Board-Folk/Camputers-Lynx/Lynx 96/Kicad/lynx96.kicad_sch

## KiCad design Lynx 96/Kicad/lynx96.kicad_sch (2025-07-15)

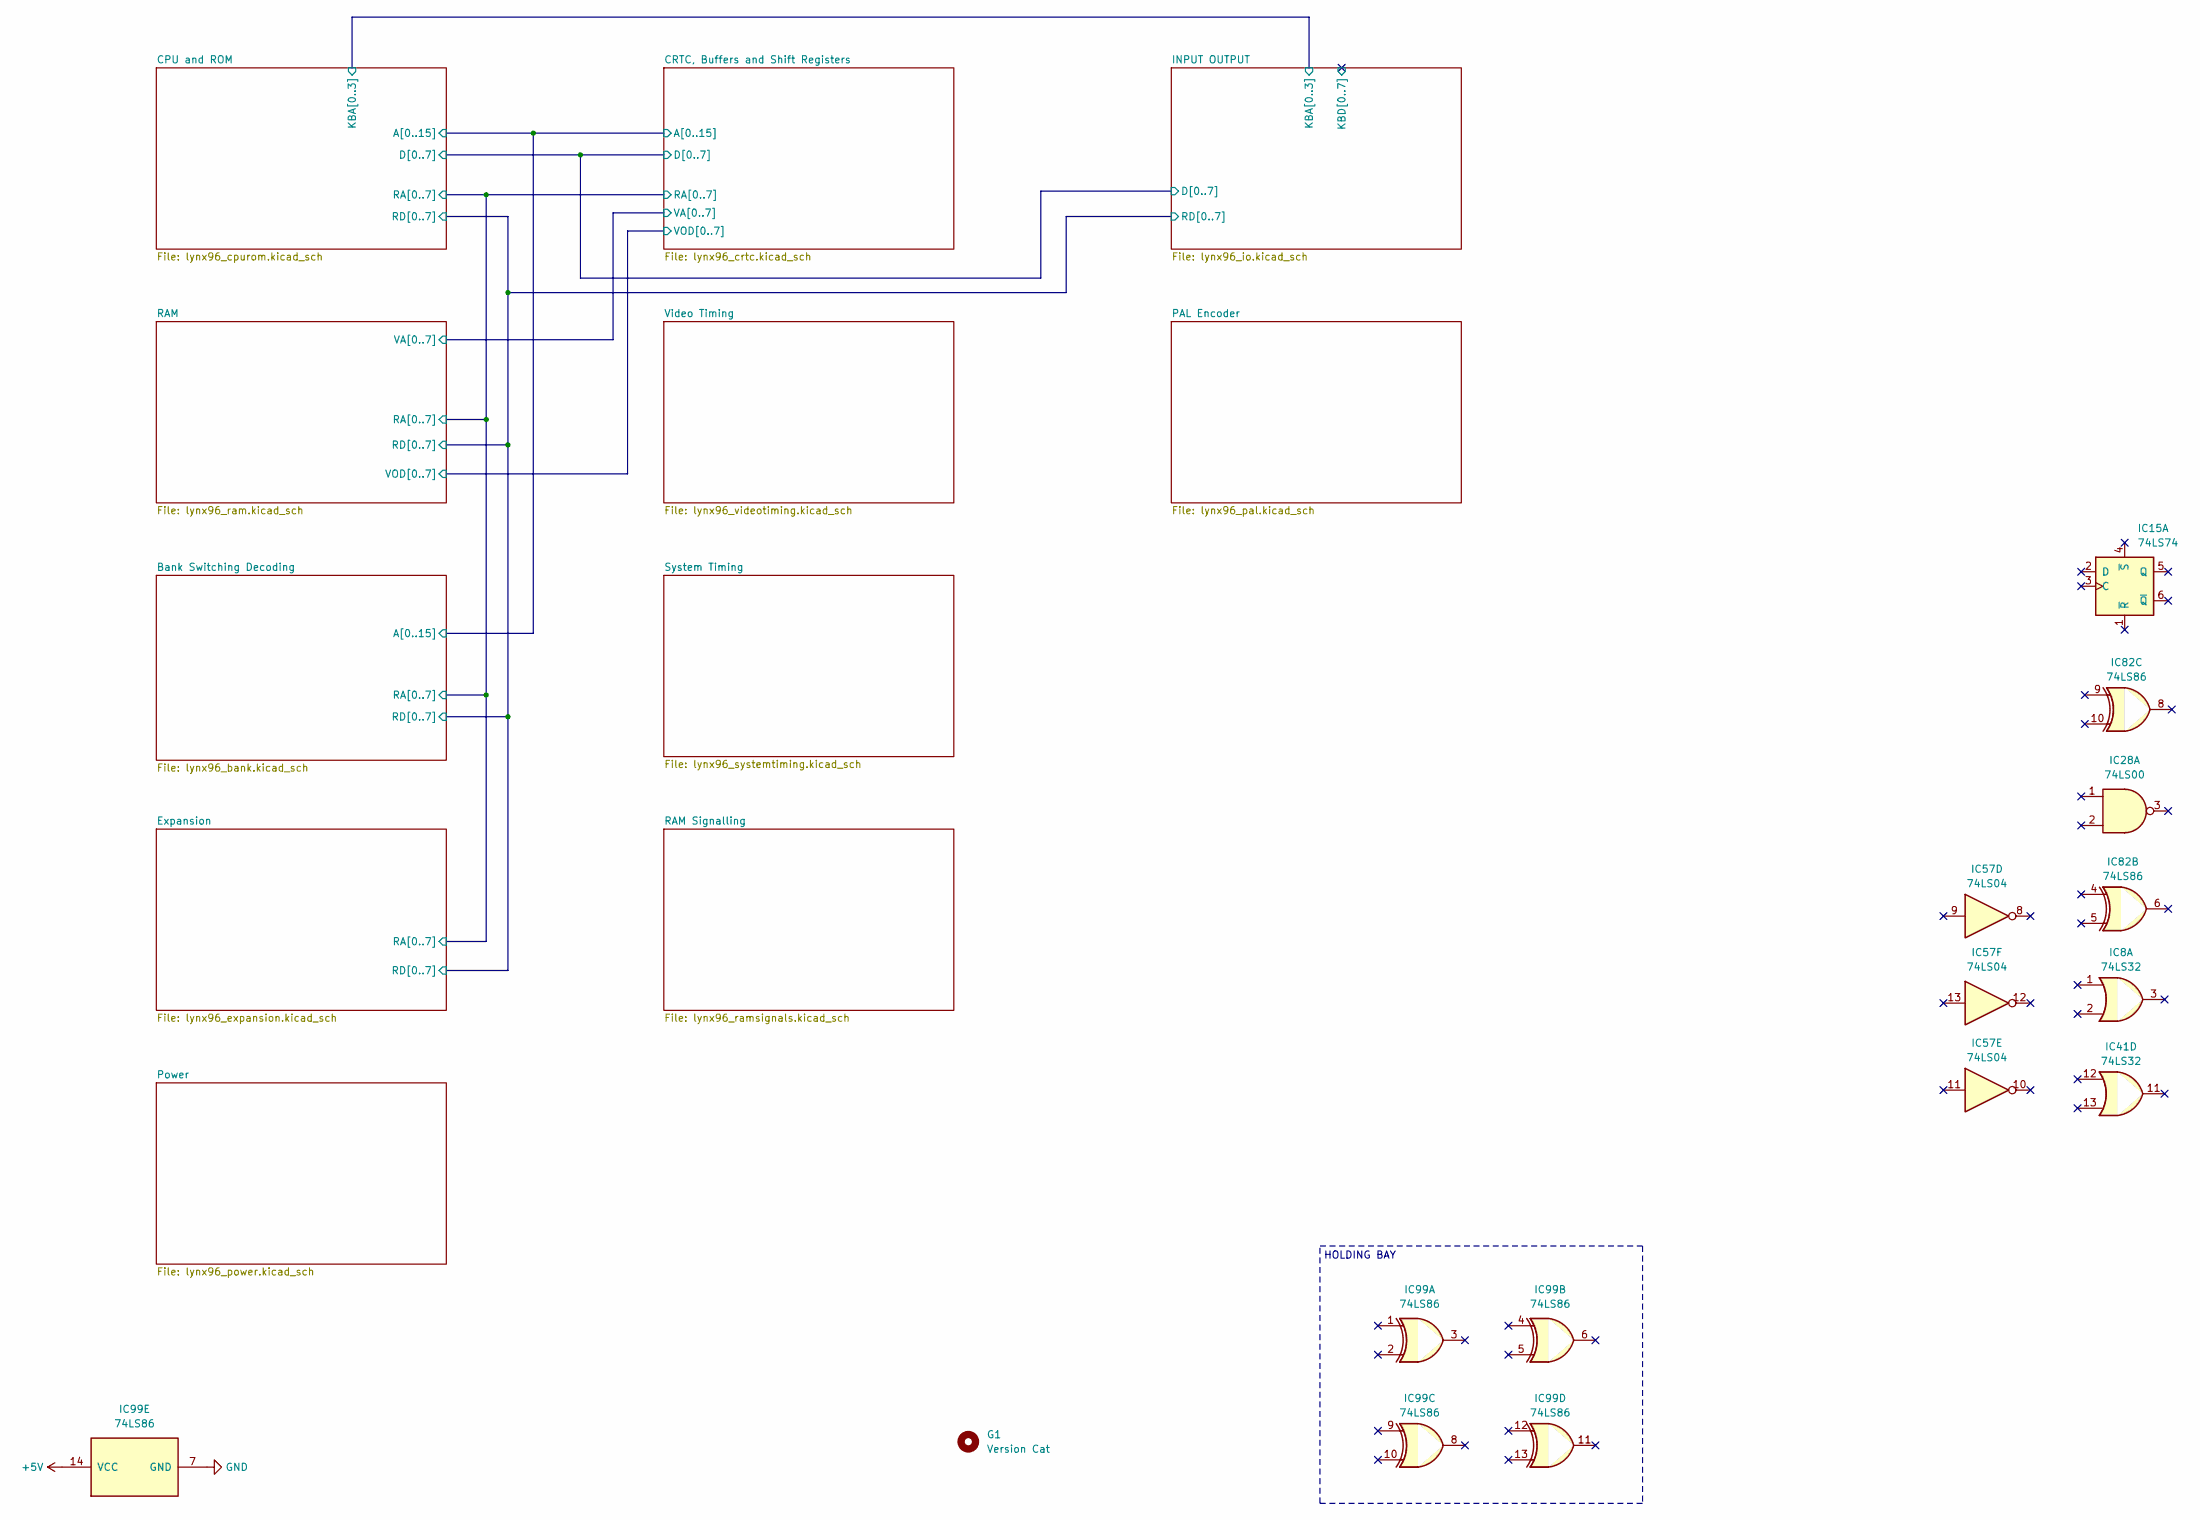
[picture p9: schematic lynx96.kicad_sch]

Parts:
G1: Version Cat; v1ncat
IC8, IC41: 74LS32; DIP-14_W7.62mm
IC15: 74LS74; DIP-14_W7.62mm
IC28: 74LS00; DIP-14_W7.62mm
IC57: 74LS04; DIP-14_W7.62mm
IC82: 74LS86; DIP-14_W7.62mm
IC99: 74LS86; FAKE

Connections:
+5V: IC99.14 (VCC)
GND: IC99.7 (GND)

Notes on the sheet:
HOLDING BAY
