Board-Folk/Camputers-Lynx/Lynx 96/Kicad/lynx96_bank.kicad_sch

## KiCad design Lynx 96/Kicad/lynx96_bank.kicad_sch (2025-07-15)

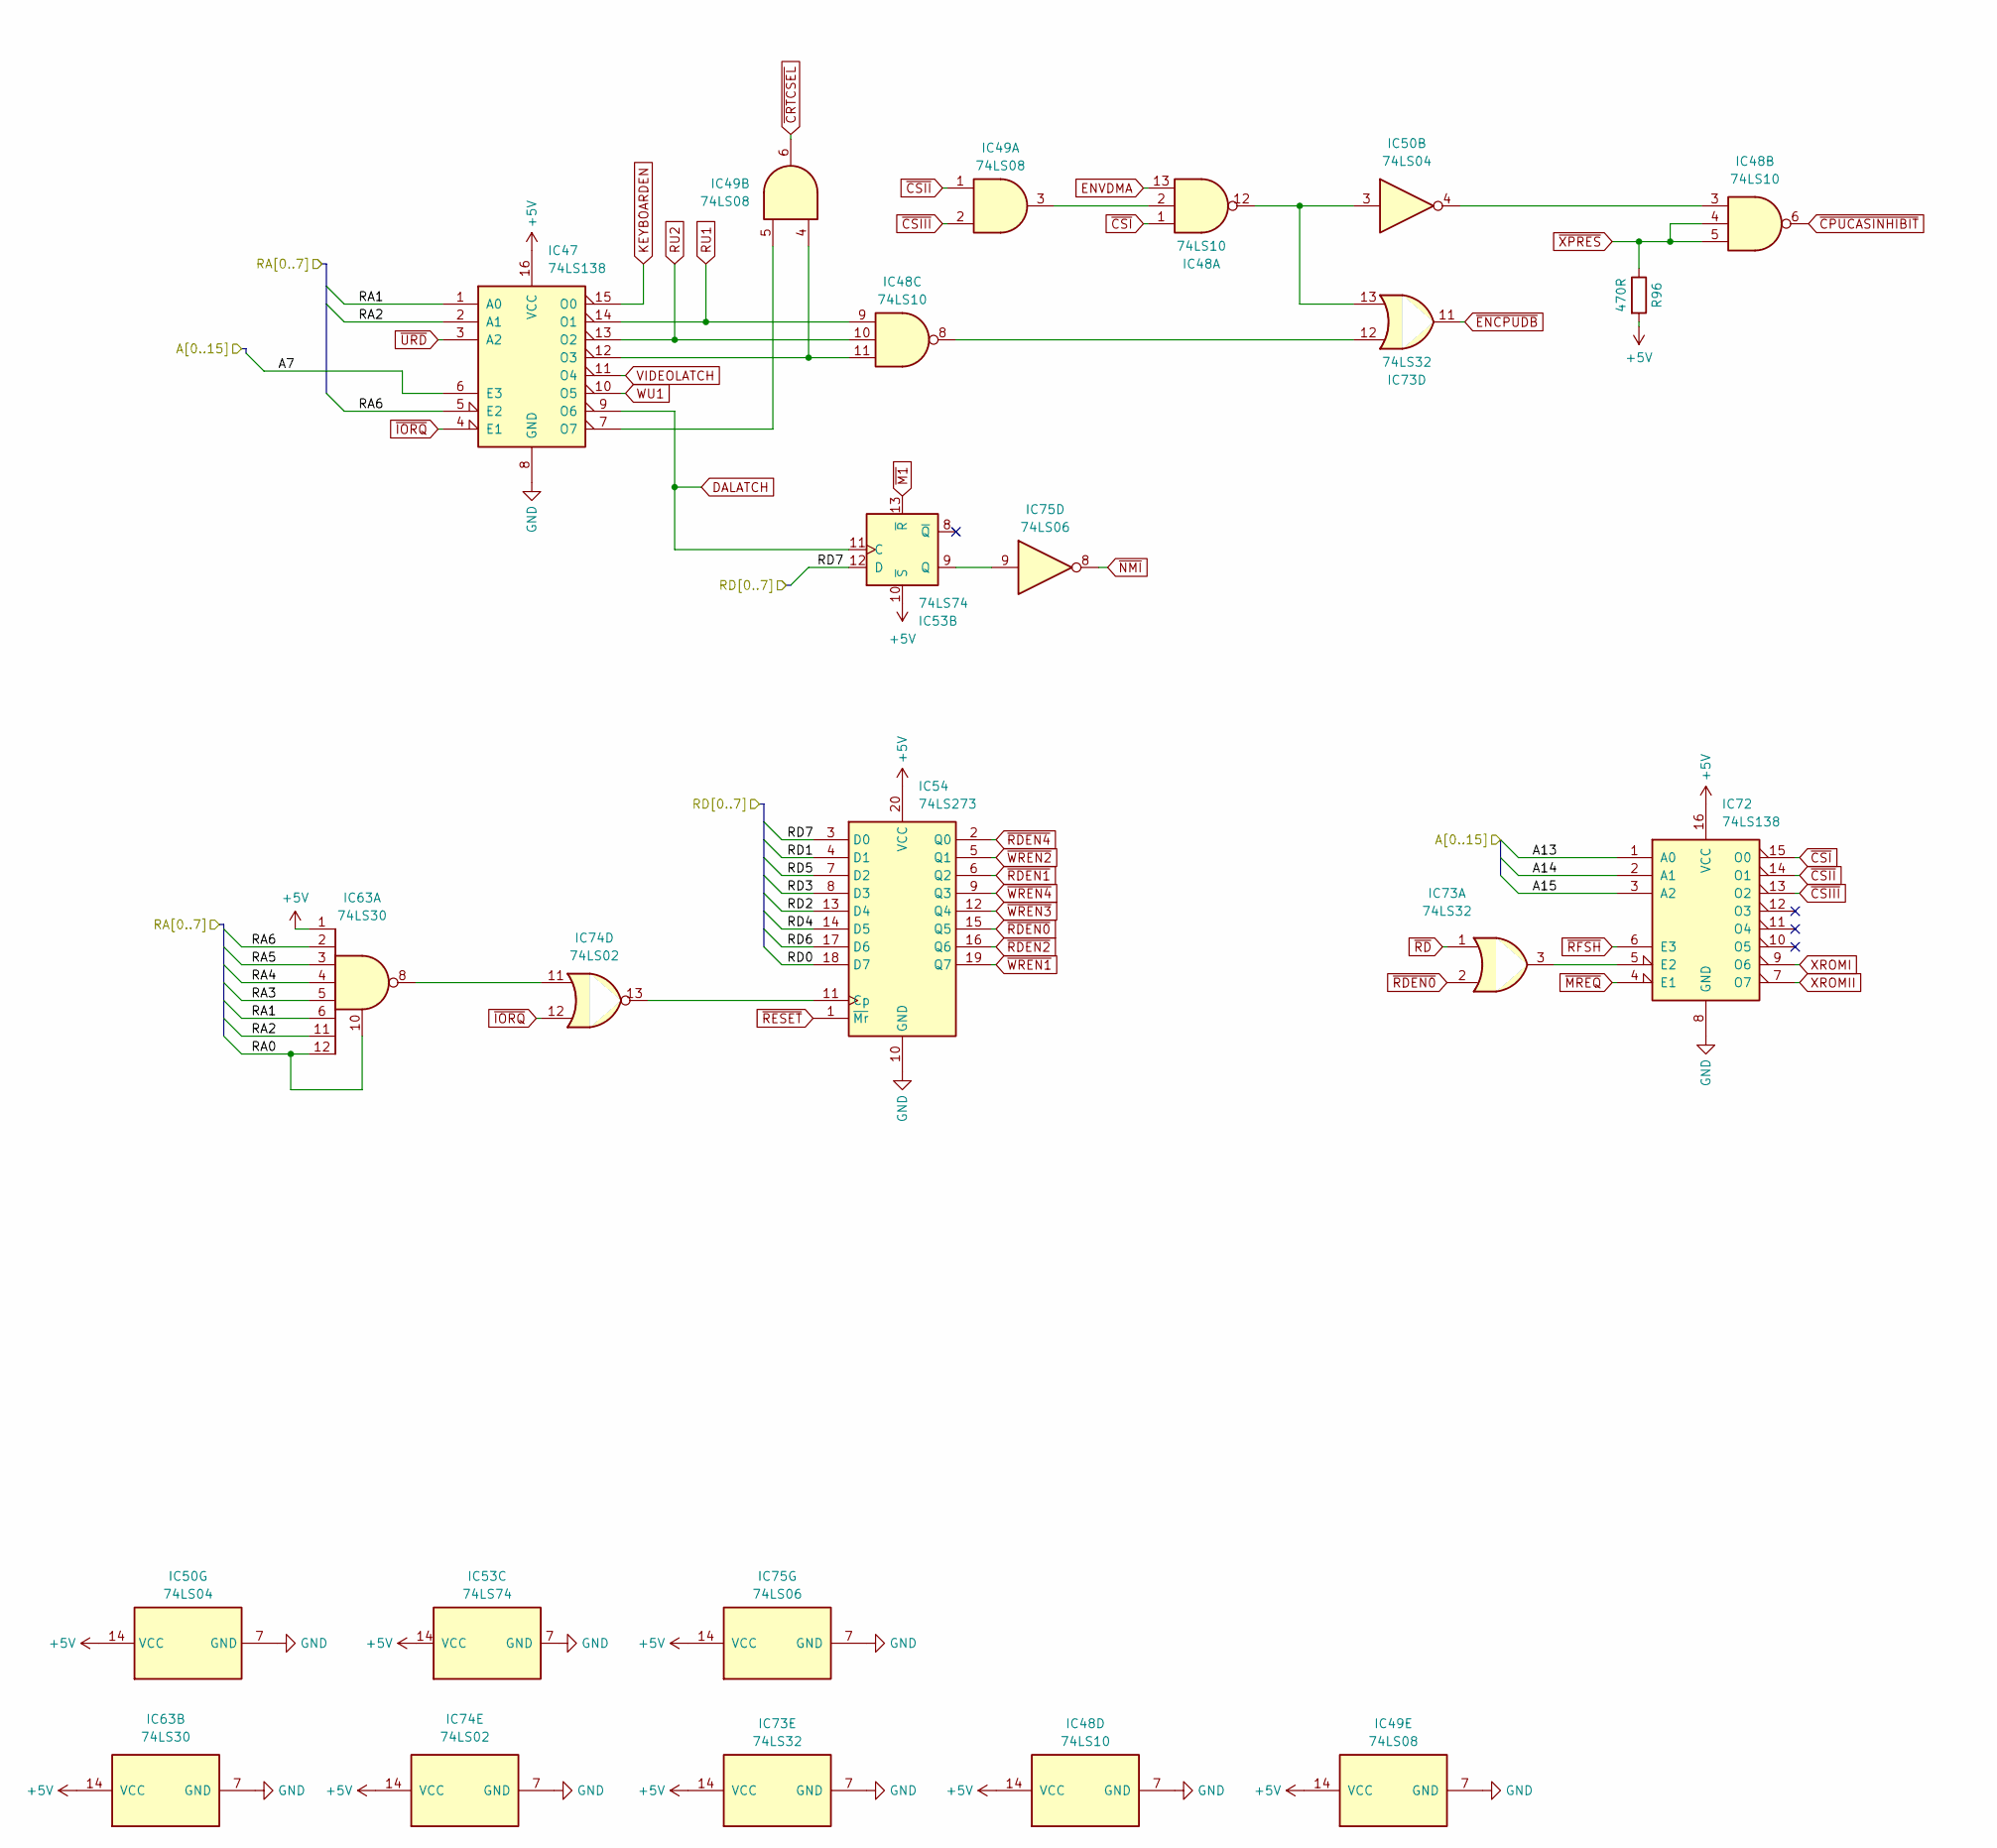
[picture p10: schematic lynx96_bank.kicad_sch]

Parts:
IC47, IC72: 74LS138; DIP-16_W7.62mm
IC48: 74LS10; DIP-14_W7.62mm
IC49: 74LS08; DIP-14_W7.62mm
IC50: 74LS04; DIP-14_W7.62mm
IC53: 74LS74; DIP-14_W7.62mm
IC54: 74LS273; DIP-20_W7.62mm
IC63: 74LS30; DIP-14_W7.62mm
IC73: 74LS32; DIP-14_W7.62mm
IC74: 74LS02; DIP-14_W7.62mm
IC75: 74LS06; DIP-14_W7.62mm
R96: 470R; Resistor 10.16mm

Connections:
+5V: IC47.16 (VCC), IC48.14 (VCC), IC49.14 (VCC), IC50.14 (VCC), IC53.10 (~S), IC53.14 (VCC), IC54.20 (VCC), IC63.1, IC63.14 (VCC), IC72.16 (VCC), IC73.14 (VCC), IC74.14 (VCC), IC75.14 (VCC), R96.2
A7: IC47.6 (E3)
A13: IC72.1 (A0)
A14: IC72.2 (A1)
A15: IC72.3 (A2)
DALATCH: IC47.9 (O6), IC53.11 (C)
ENVDMA: IC48.13
GND: IC47.8 (GND), IC48.7 (GND), IC49.7 (GND), IC50.7 (GND), IC53.7 (GND), IC54.10 (GND), IC63.7 (GND), IC72.8 (GND), IC73.7 (GND), IC74.7 (GND), IC75.7 (GND)
KEYBOARDEN: IC47.15 (O0)
unnamed: IC47.7 (O7), IC49.5
unnamed: IC47.12 (O3), IC48.11, IC49.4
unnamed: IC48.2, IC49.3
unnamed: IC48.3, IC50.4
unnamed: IC48.8, IC73.12
unnamed: IC48.12, IC50.3, IC73.13
unnamed: IC53.9 (Q), IC75.9
unnamed: IC54.11 (Cp), IC74.13
unnamed: IC63.8, IC74.11
unnamed: IC72.5 (E2), IC73.3
RA0: IC63.10, IC63.12
RA1: IC47.1 (A0), IC63.6
RA2: IC47.2 (A1), IC63.11
RA3: IC63.5
RA4: IC63.4
RA5: IC63.3
RA6: IC47.5 (E2), IC63.2
RD0: IC54.18 (D7)
RD1: IC54.4 (D1)
RD2: IC54.13 (D4)
RD3: IC54.8 (D3)
RD4: IC54.14 (D5)
RD5: IC54.7 (D2)
RD6: IC54.17 (D6)
RD7: IC53.12 (D), IC54.3 (D0)
RU1: IC47.14 (O1), IC48.9
RU2: IC47.13 (O2), IC48.10
VIDEOLATCH: IC47.11 (O4)
WU1: IC47.10 (O5)
XROMI: IC72.9 (O6)
XROMII: IC72.7 (O7)
~CPUCASINHIBIT: IC48.6
~CRTCSEL: IC49.6
~CSIII: IC49.2, IC72.13 (O2)
~CSII: IC49.1, IC72.14 (O1)
~CSI: IC48.1, IC72.15 (O0)
~ENCPUDB: IC73.11
~IORQ: IC47.4 (E1), IC74.12
~M1: IC53.13 (~R)
~MREQ: IC72.4 (E1)
~NMI: IC75.8
~RDEN0: IC54.15 (Q5), IC73.2
~RDEN1: IC54.6 (Q2)
~RDEN2: IC54.16 (Q6)
~RDEN4: IC54.2 (Q0)
~RD: IC73.1
~RESET: IC54.1 (~Mr)
~RFSH: IC72.6 (E3)
~URD: IC47.3 (A2)
~WREN1: IC54.19 (Q7)
~WREN2: IC54.5 (Q1)
~WREN3: IC54.12 (Q4)
~WREN4: IC54.9 (Q3)
~XPRES: IC48.4, IC48.5, R96.1
