Board-Folk/Camputers-Lynx/Lynx 96/Kicad/lynx96_cpurom.kicad_sch

## KiCad design Lynx 96/Kicad/lynx96_cpurom.kicad_sch (2025-07-15)

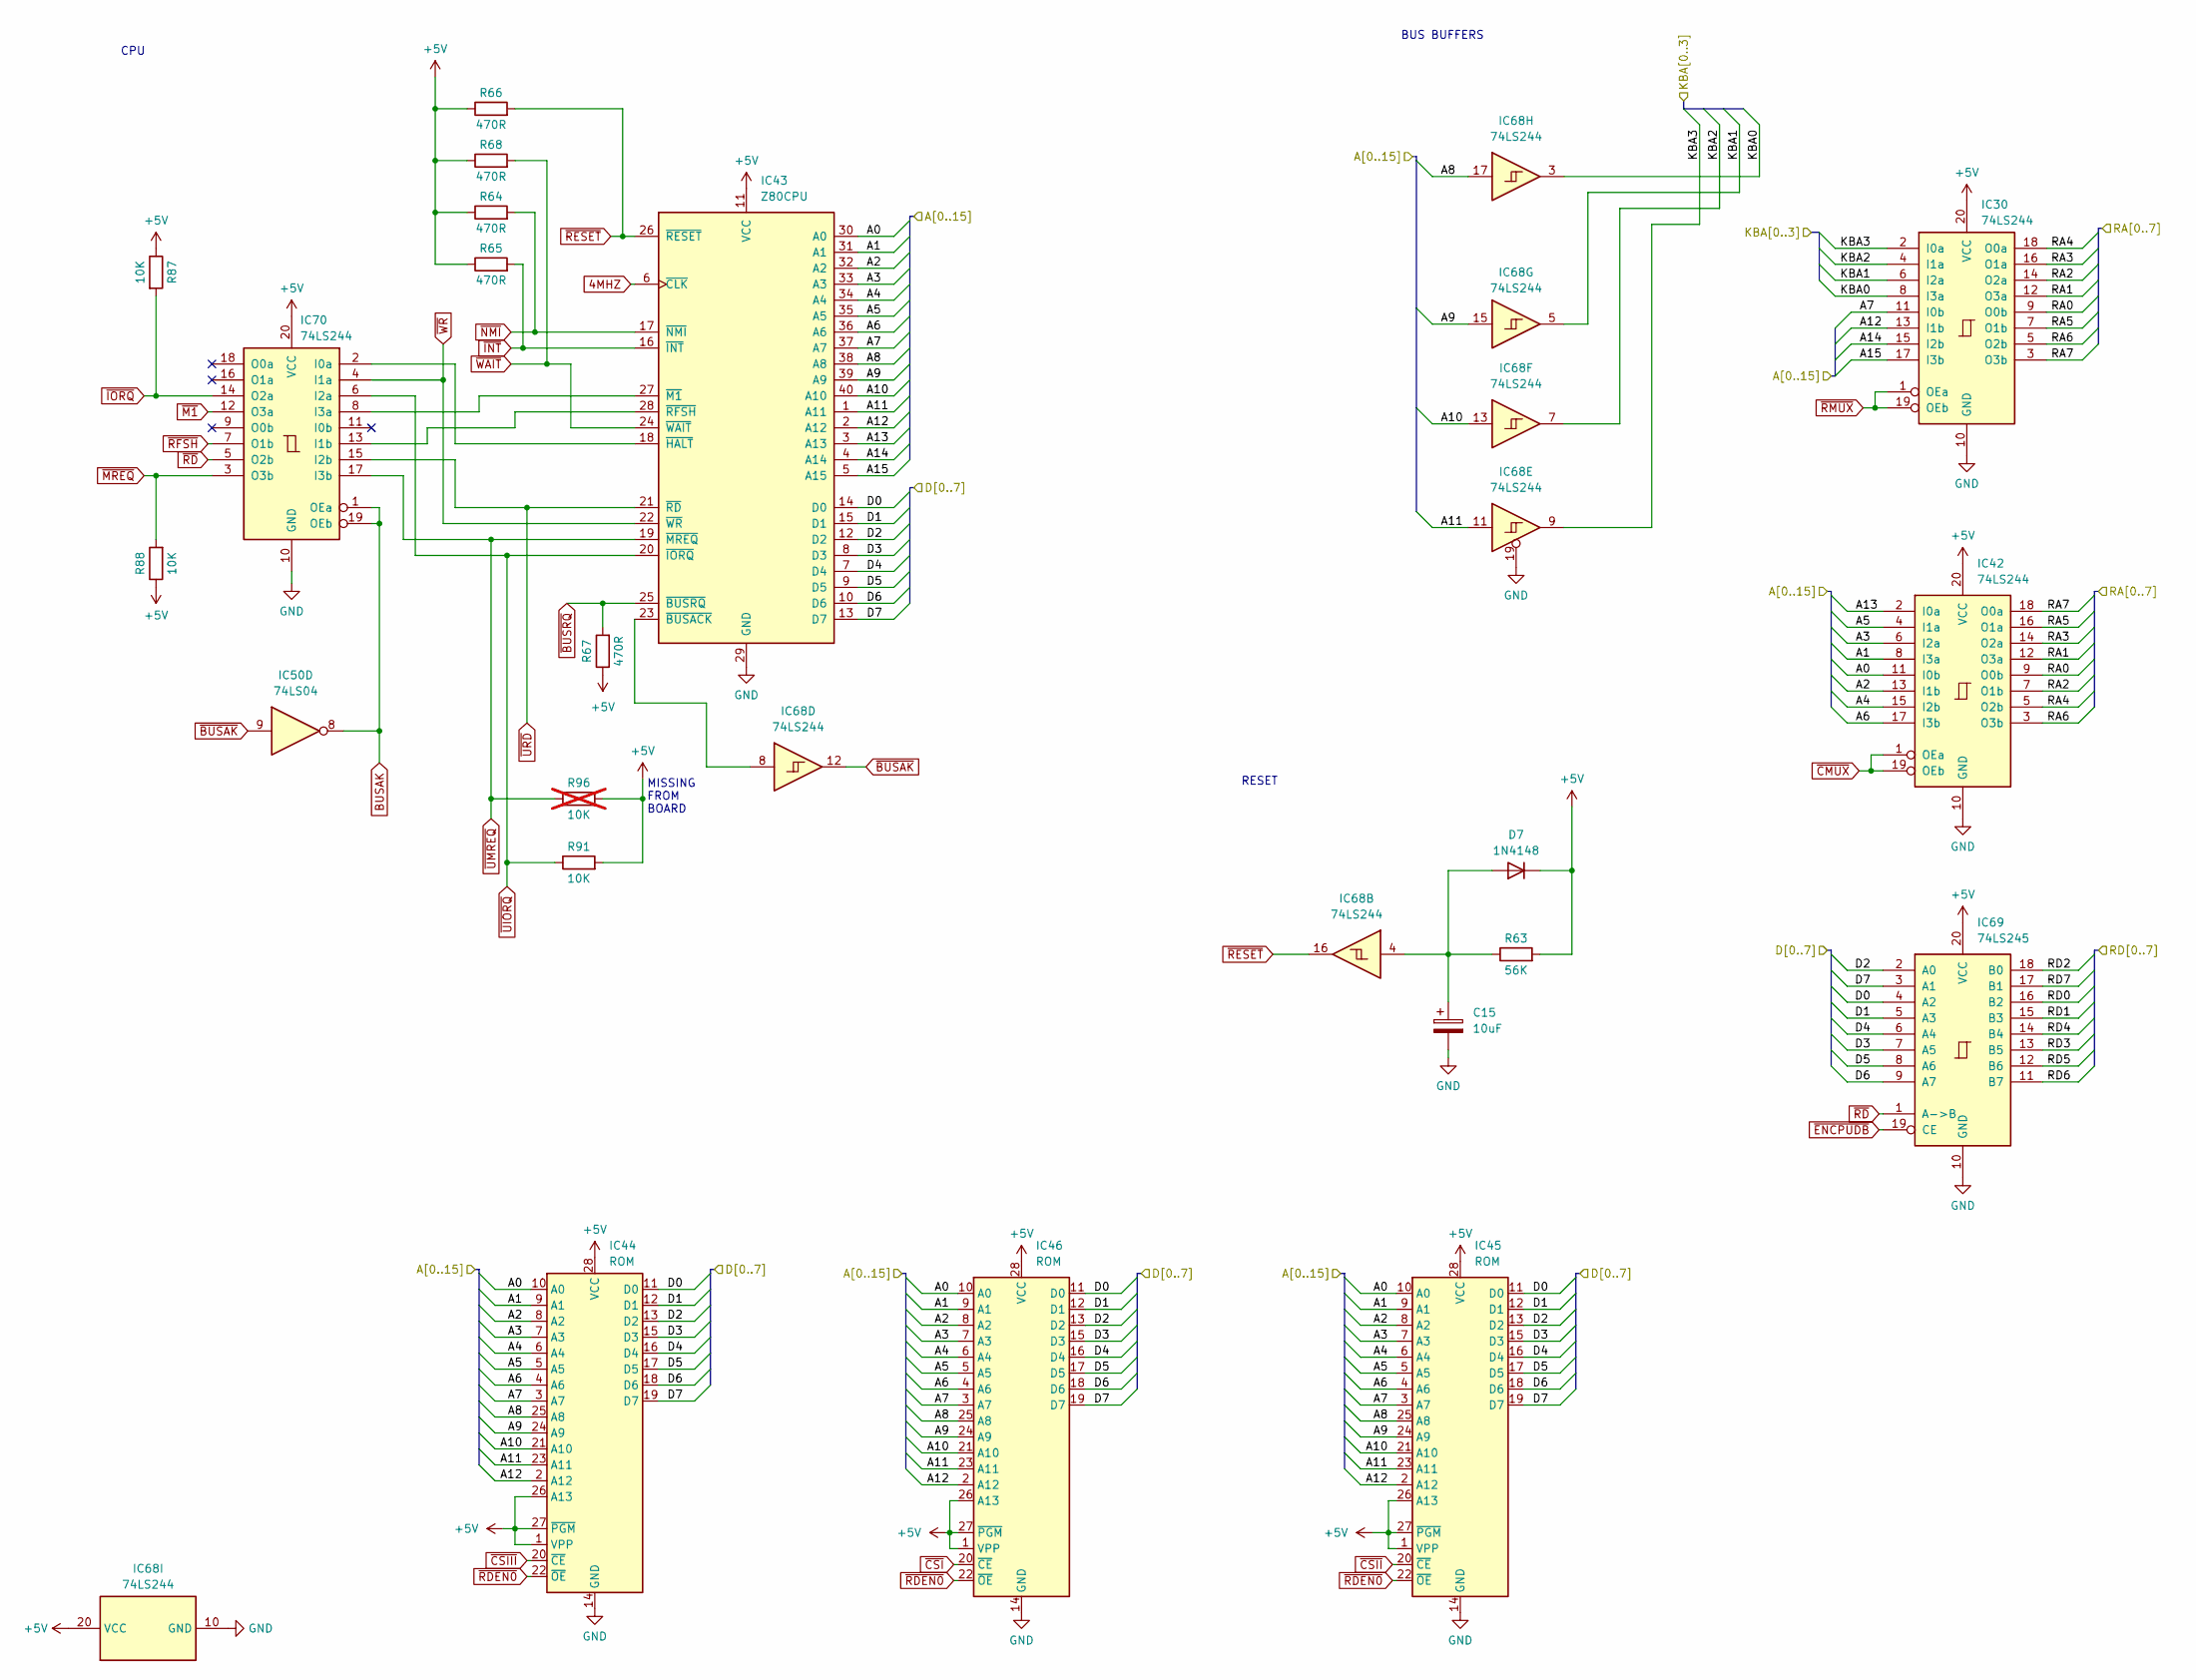
[picture p11: schematic lynx96_cpurom.kicad_sch]

Parts:
C15: 10uF; Elec_2.54mm
D7: 1N4148; Resistor 3.81mm
IC30, IC42, IC68, IC70: 74LS244; DIP-20_W7.62mm
IC43: Z80CPU; DIP-40_W15.24mm
IC44, IC45, IC46: ROM; DIP-28_W15.24mm - Double
IC50: 74LS04; DIP-14_W7.62mm
IC69: 74LS245; DIP-20_W7.62mm
R63: 56K; Resistor 3.81mm
R64, R65, R66, R67, R68: 470R; Resistor 10.16mm
R87, R88, R91: 10K; Resistor 10.16mm
R96: 10K; Resistor 5.08mm; not fitted

Connections:
4MHZ: IC43.6 (~CLK)
+5V: D7.1 (K), IC30.20 (VCC), IC42.20 (VCC), IC43.11 (VCC), IC44.1 (VPP), IC44.26 (A13), IC44.27 (~PGM), IC44.28 (VCC), IC45.1 (VPP), IC45.26 (A13), IC45.27 (~PGM), IC45.28 (VCC), IC46.1 (VPP), IC46.26 (A13), IC46.27 (~PGM), IC46.28 (VCC), IC68.20 (VCC), IC69.20 (VCC), IC70.20 (VCC), R63.2, R64.1, R65.1, R66.1, R67.1, R68.1, R87.1, R88.1, R91.2, R96.2
A0: IC42.11 (I0b), IC43.30 (A0), IC44.10 (A0), IC45.10 (A0), IC46.10 (A0)
A1: IC42.8 (I3a), IC43.31 (A1), IC44.9 (A1), IC45.9 (A1), IC46.9 (A1)
A2: IC42.13 (I1b), IC43.32 (A2), IC44.8 (A2), IC45.8 (A2), IC46.8 (A2)
A3: IC42.6 (I2a), IC43.33 (A3), IC44.7 (A3), IC45.7 (A3), IC46.7 (A3)
A4: IC42.15 (I2b), IC43.34 (A4), IC44.6 (A4), IC45.6 (A4), IC46.6 (A4)
A5: IC42.4 (I1a), IC43.35 (A5), IC44.5 (A5), IC45.5 (A5), IC46.5 (A5)
A6: IC42.17 (I3b), IC43.36 (A6), IC44.4 (A6), IC45.4 (A6), IC46.4 (A6)
A7: IC30.11 (I0b), IC43.37 (A7), IC44.3 (A7), IC45.3 (A7), IC46.3 (A7)
A8: IC43.38 (A8), IC44.25 (A8), IC45.25 (A8), IC46.25 (A8), IC68.17
A9: IC43.39 (A9), IC44.24 (A9), IC45.24 (A9), IC46.24 (A9), IC68.15
A10: IC43.40 (A10), IC44.21 (A10), IC45.21 (A10), IC46.21 (A10), IC68.13
A11: IC43.1 (A11), IC44.23 (A11), IC45.23 (A11), IC46.23 (A11), IC68.11
A12: IC30.13 (I1b), IC43.2 (A12), IC44.2 (A12), IC45.2 (A12), IC46.2 (A12)
A13: IC42.2 (I0a), IC43.3 (A13)
A14: IC30.15 (I2b), IC43.4 (A14)
A15: IC30.17 (I3b), IC43.5 (A15)
BUSAK: IC50.8, IC70.1 (OEa), IC70.19 (OEb)
D0: IC43.14 (D0), IC44.11 (D0), IC45.11 (D0), IC46.11 (D0), IC69.4 (A2)
D1: IC43.15 (D1), IC44.12 (D1), IC45.12 (D1), IC46.12 (D1), IC69.5 (A3)
D2: IC43.12 (D2), IC44.13 (D2), IC45.13 (D2), IC46.13 (D2), IC69.2 (A0)
D3: IC43.8 (D3), IC44.15 (D3), IC45.15 (D3), IC46.15 (D3), IC69.7 (A5)
D4: IC43.7 (D4), IC44.16 (D4), IC45.16 (D4), IC46.16 (D4), IC69.6 (A4)
D5: IC43.9 (D5), IC44.17 (D5), IC45.17 (D5), IC46.17 (D5), IC69.8 (A6)
D6: IC43.10 (D6), IC44.18 (D6), IC45.18 (D6), IC46.18 (D6), IC69.9 (A7)
D7: IC43.13 (D7), IC44.19 (D7), IC45.19 (D7), IC46.19 (D7), IC69.3 (A1)
GND: C15.2, IC30.10 (GND), IC42.10 (GND), IC43.29 (GND), IC44.14 (GND), IC45.14 (GND), IC46.14 (GND), IC68.10 (GND), IC68.19, IC69.10 (GND), IC70.10 (GND)
KBA0: IC30.8 (I3a), IC68.3
KBA1: IC30.6 (I2a), IC68.5
KBA2: IC30.4 (I1a), IC68.7
KBA3: IC30.2 (I0a), IC68.9
unnamed: C15.1, D7.2 (A), IC68.4, R63.1
unnamed: IC43.18 (~HALT), IC70.2 (I0a)
unnamed: IC43.23 (~BUSACK), IC68.8
unnamed: IC43.27 (~M1), IC70.8 (I3a)
unnamed: IC43.28 (~RFSH), IC70.13 (I1b)
RA0: IC30.9 (O0b), IC42.9 (O0b)
RA1: IC30.12 (O3a), IC42.12 (O3a)
RA2: IC30.14 (O2a), IC42.7 (O1b)
RA3: IC30.16 (O1a), IC42.14 (O2a)
RA4: IC30.18 (O0a), IC42.5 (O2b)
RA5: IC30.7 (O1b), IC42.16 (O1a)
RA6: IC30.5 (O2b), IC42.3 (O3b)
RA7: IC30.3 (O3b), IC42.18 (O0a)
RD0: IC69.16 (B2)
RD1: IC69.15 (B3)
RD2: IC69.18 (B0)
RD3: IC69.13 (B5)
RD4: IC69.14 (B4)
RD5: IC69.12 (B6)
RD6: IC69.11 (B7)
RD7: IC69.17 (B1)
~BUSAK: IC50.9, IC68.12
~BUSRQ: IC43.25 (~BUSRQ), R67.2
~CMUX: IC42.1 (OEa), IC42.19 (OEb)
~CSIII: IC44.20 (~CE)
~CSII: IC45.20 (~CE)
~CSI: IC46.20 (~CE)
~ENCPUDB: IC69.19 (CE)
~INT: IC43.16 (~INT), R65.2
~IORQ: IC70.14 (O2a), R87.2
~M1: IC70.12 (O3a)
~MREQ: IC70.3 (O3b), R88.2
~NMI: IC43.17 (~NMI), R64.2
~RDEN0: IC44.22 (~OE), IC45.22 (~OE), IC46.22 (~OE)
~RD: IC69.1 (A->B), IC70.5 (O2b)
~RESET: IC43.26 (~RESET), IC68.16, R66.2
~RFSH: IC70.7 (O1b)
~RMUX: IC30.1 (OEa), IC30.19 (OEb)
~UIORQ: IC43.20 (~IORQ), IC70.6 (I2a), R91.1
~UMREQ: IC43.19 (~MREQ), IC70.17 (I3b), R96.1
~URD: IC43.21 (~RD), IC70.15 (I2b)
~WAIT: IC43.24 (~WAIT), R68.2
~WR: IC43.22 (~WR), IC70.4 (I1a)

Notes on the sheet:
CPU
MISSING FROM BOARD
BUS BUFFERS
RESET
