Board-Folk/Camputers-Lynx/Lynx 96/Kicad/lynx96_crtc.kicad_sch

## KiCad design Lynx 96/Kicad/lynx96_crtc.kicad_sch (2025-07-15)

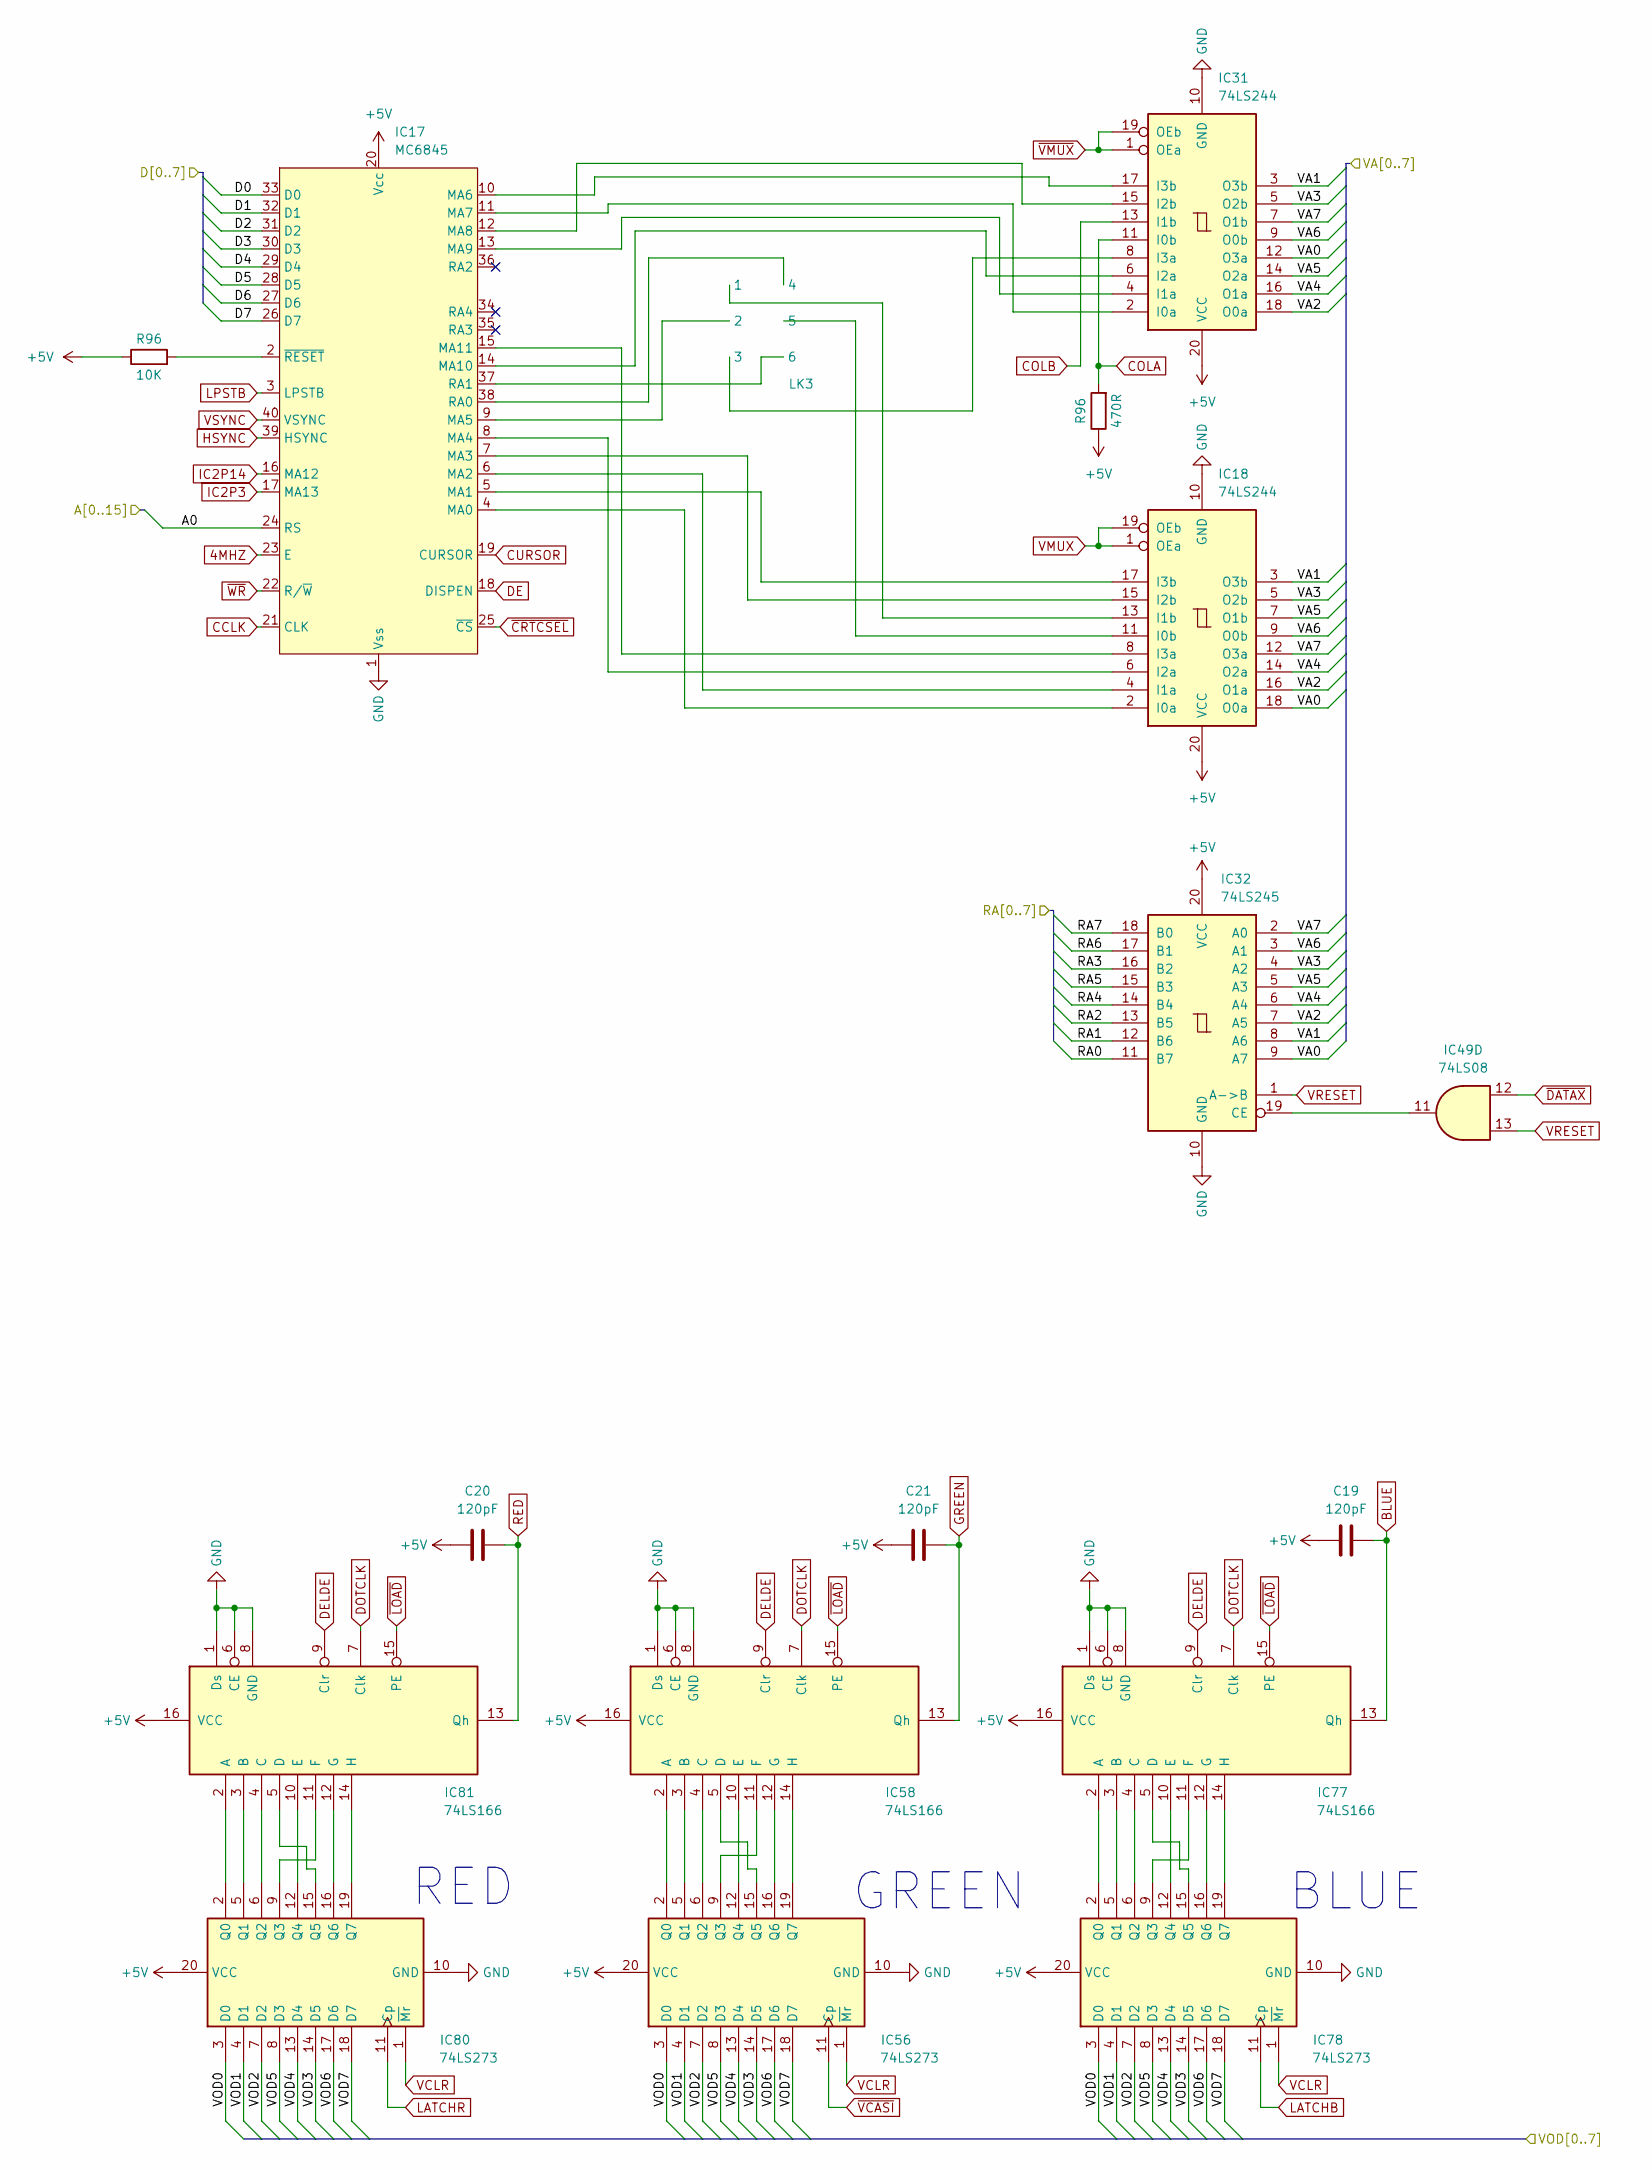
[picture p12: schematic lynx96_crtc.kicad_sch]

Parts:
C19, C20, C21: 120pF; Resistor 5.08mm
IC17: MC6845; DIP-40_W15.24mm
IC18, IC31: 74LS244; DIP-20_W7.62mm
IC32: 74LS245; DIP-20_W7.62mm
IC49: 74LS08; DIP-14_W7.62mm
IC56, IC78, IC80: 74LS273; DIP-20_W7.62mm
IC58, IC77, IC81: 74LS166; DIP-16_W7.62mm
LK3: LK9
R96: 470R; Resistor 4.20mm

Connections:
4MHZ: IC17.23 (E)
+5V: C19.1, C20.1, C21.1, IC17.20 (Vcc), IC18.20 (VCC), IC31.20 (VCC), IC32.20 (VCC), IC56.20 (VCC), IC58.16 (VCC), IC77.16 (VCC), IC78.20 (VCC), IC80.20 (VCC), IC81.16 (VCC), R96.1
A0: IC17.24 (RS)
BLUE: C19.2, IC77.13 (Qh)
CCLK: IC17.21 (CLK)
COLA: IC31.11 (I0b), R96.2
COLB: IC31.13 (I1b)
CURSOR: IC17.19 (CURSOR)
D0: IC17.33 (D0)
D1: IC17.32 (D1)
D2: IC17.31 (D2)
D3: IC17.30 (D3)
D4: IC17.29 (D4)
D5: IC17.28 (D5)
D6: IC17.27 (D6)
D7: IC17.26 (D7)
DE: IC17.18 (DISPEN)
DELDE: IC58.9 (Clr), IC77.9 (Clr), IC81.9 (Clr)
DOTCLK: IC58.7 (Clk), IC77.7 (Clk), IC81.7 (Clk)
GND: IC17.1 (Vss), IC18.10 (GND), IC31.10 (GND), IC32.10 (GND), IC56.10 (GND), IC58.1 (Ds), IC58.6 (CE), IC58.8 (GND), IC77.1 (Ds), IC77.6 (CE), IC77.8 (GND), IC78.10 (GND), IC80.10 (GND), IC81.1 (Ds), IC81.6 (CE), IC81.8 (GND)
GREEN: C21.2, IC58.13 (Qh)
HSYNC: IC17.39 (HSYNC)
IC2P3: IC17.17 (MA13)
IC2P14: IC17.16 (MA12)
LATCHB: IC78.11 (Cp)
LATCHR: IC80.11 (Cp)
LPSTB: IC17.3 (LPSTB)
unnamed: IC17.2 (~RESET), R96.2
unnamed: IC17.4 (MA0), IC18.2 (I0a)
unnamed: IC17.5 (MA1), IC18.17 (I3b)
unnamed: IC17.6 (MA2), IC18.4 (I1a)
unnamed: IC17.7 (MA3), IC18.15 (I2b)
unnamed: IC17.8 (MA4), IC18.6 (I2a)
unnamed: IC17.9 (MA5), LK3.2
unnamed: IC17.10 (MA6), IC31.17 (I3b)
unnamed: IC17.11 (MA7), IC31.2 (I0a)
unnamed: IC17.12 (MA8), IC31.15 (I2b)
unnamed: IC17.13 (MA9), IC31.4 (I1a)
unnamed: IC17.14 (MA10), IC31.6 (I2a)
unnamed: IC17.15 (MA11), IC18.8 (I3a)
unnamed: IC17.37 (RA1), LK3.6
unnamed: IC17.38 (RA0), LK3.4
unnamed: IC18.11 (I0b), LK3.5
unnamed: IC18.13 (I1b), LK3.1
unnamed: IC31.8 (I3a), LK3.3
unnamed: IC32.19 (CE), IC49.11
unnamed: IC56.2 (Q0), IC58.2 (A)
unnamed: IC56.5 (Q1), IC58.3 (B)
unnamed: IC56.6 (Q2), IC58.4 (C)
unnamed: IC56.9 (Q3), IC58.11 (F)
unnamed: IC56.12 (Q4), IC58.10 (E)
unnamed: IC56.15 (Q5), IC58.5 (D)
unnamed: IC56.16 (Q6), IC58.12 (G)
unnamed: IC56.19 (Q7), IC58.14 (H)
unnamed: IC77.2 (A), IC78.2 (Q0)
unnamed: IC77.3 (B), IC78.5 (Q1)
unnamed: IC77.4 (C), IC78.6 (Q2)
unnamed: IC77.5 (D), IC78.15 (Q5)
unnamed: IC77.10 (E), IC78.12 (Q4)
unnamed: IC77.11 (F), IC78.9 (Q3)
unnamed: IC77.12 (G), IC78.16 (Q6)
unnamed: IC77.14 (H), IC78.19 (Q7)
unnamed: IC80.2 (Q0), IC81.2 (A)
unnamed: IC80.5 (Q1), IC81.3 (B)
unnamed: IC80.6 (Q2), IC81.4 (C)
unnamed: IC80.9 (Q3), IC81.11 (F)
unnamed: IC80.12 (Q4), IC81.10 (E)
unnamed: IC80.15 (Q5), IC81.5 (D)
unnamed: IC80.16 (Q6), IC81.12 (G)
unnamed: IC80.19 (Q7), IC81.14 (H)
RA0: IC32.11 (B7)
RA1: IC32.12 (B6)
RA2: IC32.13 (B5)
RA3: IC32.16 (B2)
RA4: IC32.14 (B4)
RA5: IC32.15 (B3)
RA6: IC32.17 (B1)
RA7: IC32.18 (B0)
RED: C20.2, IC81.13 (Qh)
VA0: IC18.18 (O0a), IC31.12 (O3a), IC32.9 (A7)
VA1: IC18.3 (O3b), IC31.3 (O3b), IC32.8 (A6)
VA2: IC18.16 (O1a), IC31.18 (O0a), IC32.7 (A5)
VA3: IC18.5 (O2b), IC31.5 (O2b), IC32.4 (A2)
VA4: IC18.14 (O2a), IC31.16 (O1a), IC32.6 (A4)
VA5: IC18.7 (O1b), IC31.14 (O2a), IC32.5 (A3)
VA6: IC18.9 (O0b), IC31.9 (O0b), IC32.3 (A1)
VA7: IC18.12 (O3a), IC31.7 (O1b), IC32.2 (A0)
VCLR: IC56.1 (~Mr), IC78.1 (~Mr), IC80.1 (~Mr)
VMUX: IC18.1 (OEa), IC18.19 (OEb)
VOD0: IC56.3 (D0), IC78.3 (D0), IC80.3 (D0)
VOD1: IC56.4 (D1), IC78.4 (D1), IC80.4 (D1)
VOD2: IC56.7 (D2), IC78.7 (D2), IC80.7 (D2)
VOD3: IC56.14 (D5), IC78.14 (D5), IC80.14 (D5)
VOD4: IC56.13 (D4), IC78.13 (D4), IC80.13 (D4)
VOD5: IC56.8 (D3), IC78.8 (D3), IC80.8 (D3)
VOD6: IC56.17 (D6), IC78.17 (D6), IC80.17 (D6)
VOD7: IC56.18 (D7), IC78.18 (D7), IC80.18 (D7)
VRESET: IC32.1 (A->B), IC49.13
VSYNC: IC17.40 (VSYNC)
~CRTCSEL: IC17.25 (~CS)
~DATAX: IC49.12
~LOAD: IC58.15 (PE), IC77.15 (PE), IC81.15 (PE)
~VCASI: IC56.11 (Cp)
~VMUX: IC31.1 (OEa), IC31.19 (OEb)
~WR: IC17.22 (R/~W)

Notes on the sheet:
RED
BLUE
GREEN
