Board-Folk/Camputers-Lynx/Lynx 96/Kicad/lynx96_expansion.kicad_sch

## KiCad design Lynx 96/Kicad/lynx96_expansion.kicad_sch (2025-07-15)

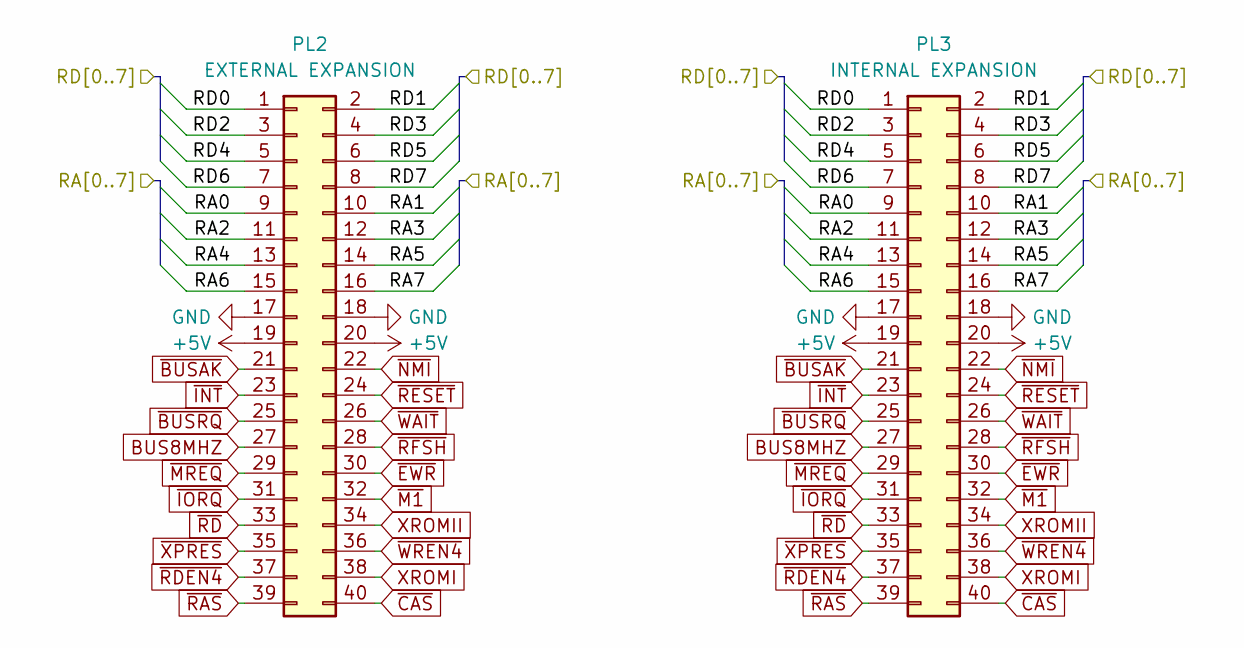
[picture p13: schematic lynx96_expansion.kicad_sch]

Parts:
PL2: EXTERNAL EXPANSION; PL - 02x20
PL3: INTERNAL EXPANSION; PL - 02x20

Connections:
+5V: PL2.19, PL2.20, PL3.19, PL3.20
BUS8MHZ: PL2.27, PL3.27
GND: PL2.17, PL2.18, PL3.17, PL3.18
RA0: PL2.9, PL3.9
RA1: PL2.10, PL3.10
RA2: PL2.11, PL3.11
RA3: PL2.12, PL3.12
RA4: PL2.13, PL3.13
RA5: PL2.14, PL3.14
RA6: PL2.15, PL3.15
RA7: PL2.16, PL3.16
RD0: PL2.1, PL3.1
RD1: PL2.2, PL3.2
RD2: PL2.3, PL3.3
RD3: PL2.4, PL3.4
RD4: PL2.5, PL3.5
RD5: PL2.6, PL3.6
RD6: PL2.7, PL3.7
RD7: PL2.8, PL3.8
XROMI: PL2.38, PL3.38
XROMII: PL2.34, PL3.34
~BUSAK: PL2.21, PL3.21
~BUSRQ: PL2.25, PL3.25
~CAS: PL2.40, PL3.40
~EWR: PL2.30, PL3.30
~INT: PL2.23, PL3.23
~IORQ: PL2.31, PL3.31
~M1: PL2.32, PL3.32
~MREQ: PL2.29, PL3.29
~NMI: PL2.22, PL3.22
~RAS: PL2.39, PL3.39
~RDEN4: PL2.37, PL3.37
~RD: PL2.33, PL3.33
~RESET: PL2.24, PL3.24
~RFSH: PL2.28, PL3.28
~WAIT: PL2.26, PL3.26
~WREN4: PL2.36, PL3.36
~XPRES: PL2.35, PL3.35
