Board-Folk/Camputers-Lynx/Lynx 96/Kicad/lynx96_io.kicad_sch

## KiCad design Lynx 96/Kicad/lynx96_io.kicad_sch (2025-07-15)

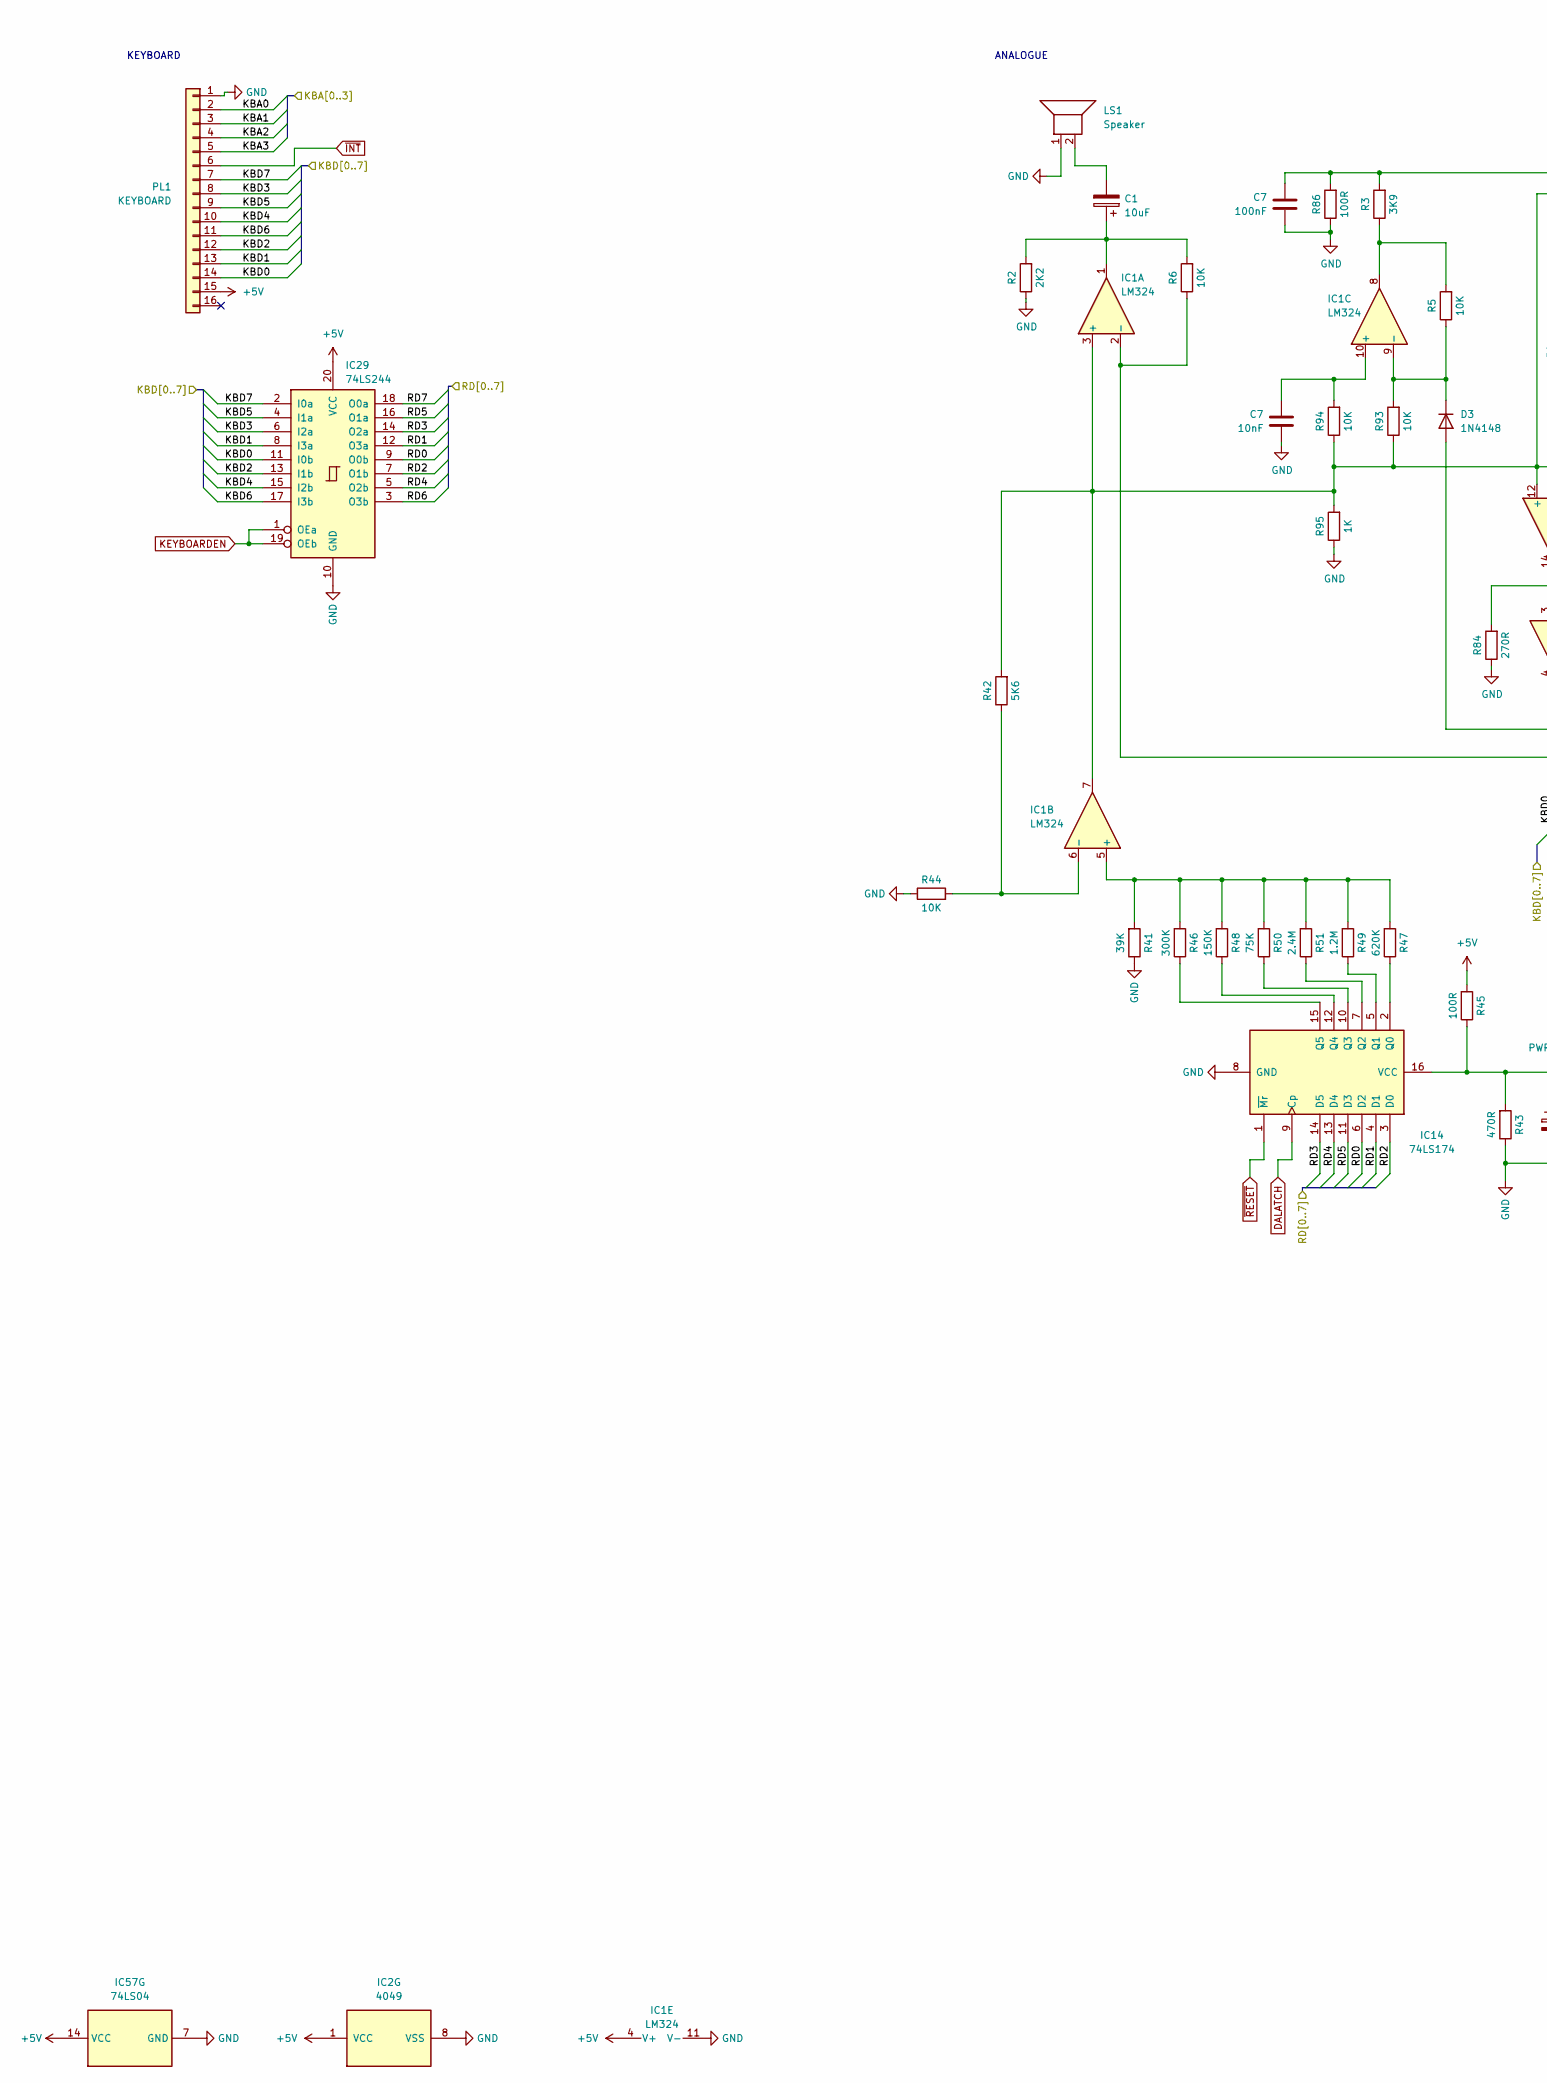
[picture p14: schematic lynx96_io.kicad_sch, part in row 1, column 1]

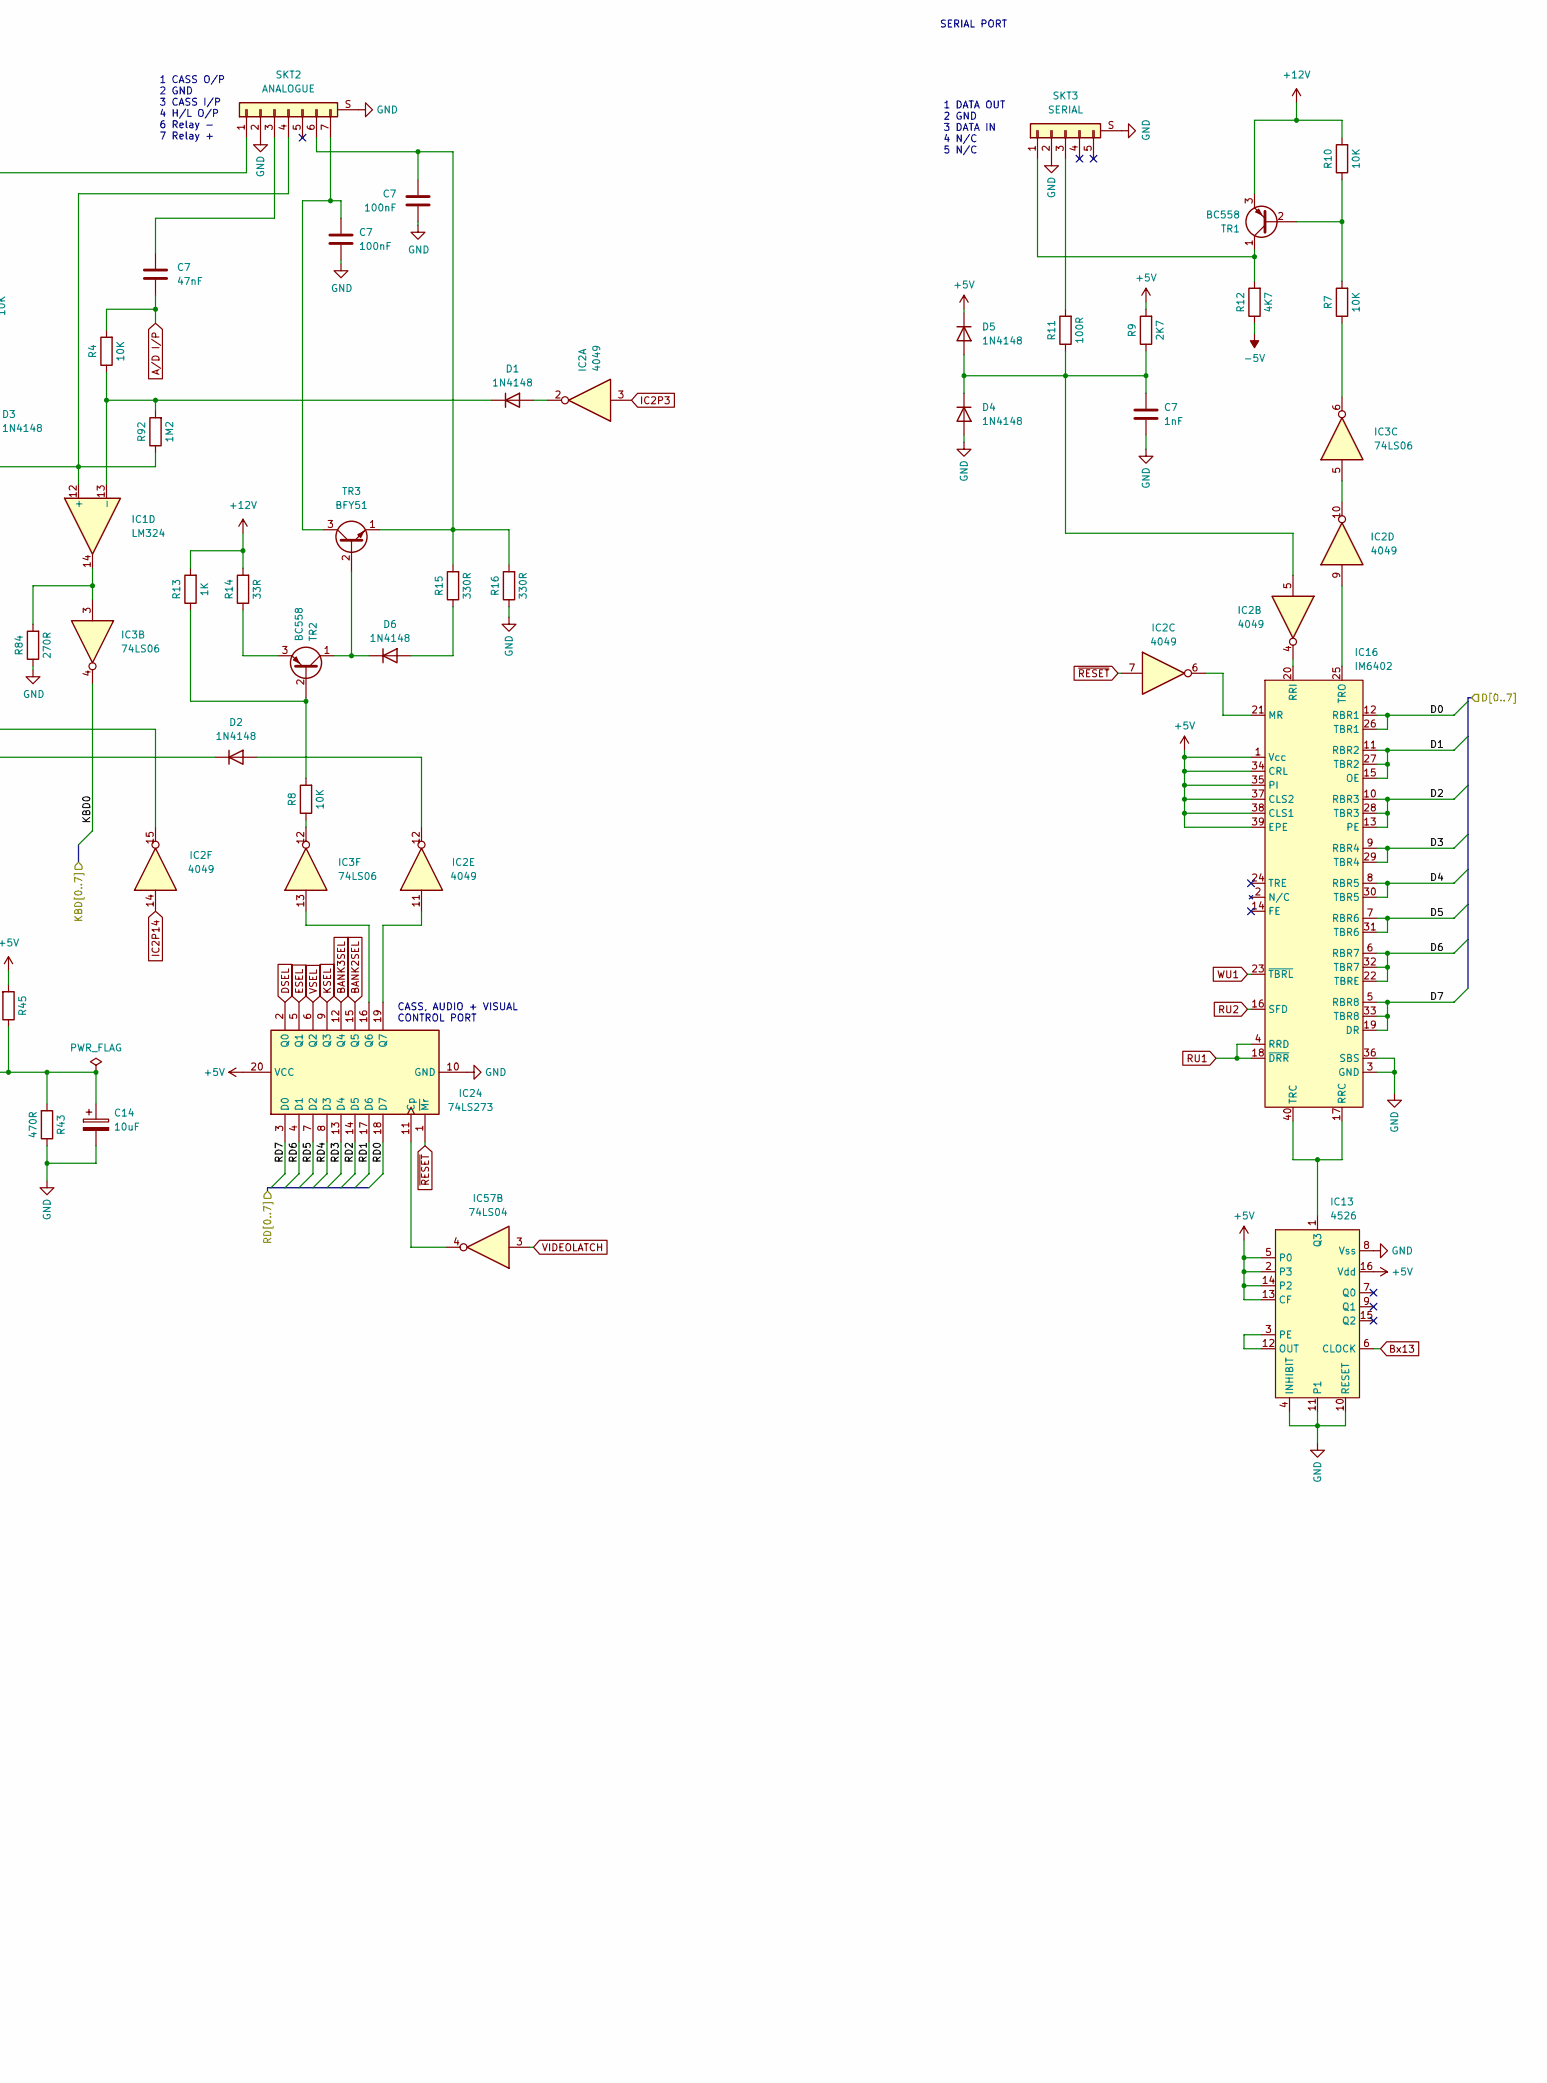
[picture p15: schematic lynx96_io.kicad_sch, part in row 1, column 2]

Parts:
C1, C14: 10uF; Elec_2.54mm
C7: 100nF; Resistor 5.08mm
D1, D2, D3, D6: 1N4148; Diode 10.16mm
D4, D5: 1N4148; Resistor 3.81mm
IC1: LM324; DIP-14_W7.62mm
IC2: 4049; DIP-16_W7.62mm
IC3: 74LS06; DIP-14_W7.62mm
IC13: 4526; DIP-16_W7.62mm
IC14: 74LS174; DIP-16_W7.62mm
IC16: IM6402; DIP-40_W15.24mm
IC24: 74LS273; DIP-20_W7.62mm
IC29: 74LS244; DIP-20_W7.62mm
IC57: 74LS04; DIP-14_W7.62mm
LS1: Speaker; LK 2-pin 2.54mm - No Box
PL1: KEYBOARD; PL1
R2: 2K2; Resistor 10.16mm
R3: 3K9; Resistor 10.16mm
R4, R5, R6, R7, R8, R93, R94: 10K; Resistor 10.16mm
R9: 2K7; Resistor 5.08mm
R10, R44: 10K; Resistor 3.81mm
R11: 100R; Resistor 5.08mm
R12: 4K7; Resistor R12
R13: 1K; Resistor 5.08mm
R14: 33R; Resistor 4.20mm
R15, R16: 330R; Resistor 10.16mm
R41: 39K; Resistor 4.20mm
R42: 5K6; Resistor 3.81mm
R43: 470R; Resistor 3.81mm
R45, R86: 100R; Resistor 10.16mm
R46: 300K; Resistor 5.08mm
R47: 620K; Resistor 5.08mm
R48: 150K; Resistor 5.08mm
R49: 1.2M; Resistor 5.08mm
R50: 75K; Resistor 5.08mm
R51: 2.4M; Resistor 5.08mm
R84: 270R; Resistor 10.16mm
R92: 1M2; Resistor 10.16mm
R95: 1K; Resistor 10.16mm
SKT2: ANALOGUE; SKT2
SKT3: SERIAL; SKT3
TR1: BC558; Transistor - No Box
TR2: BC558; Transistor
TR3: BFY51; Transistor - Alt Pads

Connections:
+5V: D5.1 (K), IC1.4 (V+), IC2.1 (VCC), IC13.2 (P3), IC13.5 (P0), IC13.13 (CF), IC13.14 (P2), IC13.16 (Vdd), IC16.1 (Vcc), IC16.34 (CRL), IC16.35 (PI), IC16.37 (CLS2), IC16.38 (CLS1), IC16.39 (EPE), IC24.20 (VCC), IC29.20 (VCC), IC57.14 (VCC), PL1.15, R9.2, R45.2
+12V: R10.2, R13.2, R14.2, TR1.3 (E)
-5V: R12.1
A/D I/P: C7.2, R4.2
BANK2SEL: IC24.15 (Q5)
BANK3SEL: IC24.12 (Q4)
Bx13: IC13.6 (CLOCK)
D0: IC16.12 (RBR1), IC16.26 (TBR1)
D1: IC16.11 (RBR2), IC16.15 (OE), IC16.27 (TBR2)
D2: IC16.10 (RBR3), IC16.13 (PE), IC16.28 (TBR3)
D3: IC16.9 (RBR4), IC16.29 (TBR4)
D4: IC16.8 (RBR5), IC16.30 (TBR5)
D5: IC16.7 (RBR6), IC16.31 (TBR6)
D6: IC16.6 (RBR7), IC16.22 (TBRE), IC16.32 (TBR7)
D7: IC16.5 (RBR8), IC16.19 (DR), IC16.33 (TBR8)
DALATCH: IC14.9 (Cp)
DSEL: IC24.2 (Q0)
ESEL: IC24.5 (Q1)
GND: C7.2, C14.2, D4.2 (A), IC1.11 (V-), IC2.8 (VSS), IC13.4 (INHIBIT), IC13.8 (Vss), IC13.10 (RESET), IC13.11 (P1), IC14.8 (GND), IC16.3 (GND), IC16.36 (SBS), IC24.10 (GND), IC29.10 (GND), IC57.7 (GND), LS1.1, PL1.1, R2.1, R16.1, R41.1, R43.1, R44.1, R84.1, R86.1, R95.1, SKT2.2, SKT2.S (SHIELD), SKT3.2, SKT3.S (SHIELD)
IC2P3: IC2.3
IC2P14: IC2.14
KBA0: PL1.2
KBA1: PL1.3
KBA2: PL1.4
KBA3: PL1.5
KBD0: IC3.4, IC29.11 (I0b), PL1.14
KBD1: IC29.8 (I3a), PL1.13
KBD2: IC29.13 (I1b), PL1.12
KBD3: IC29.6 (I2a), PL1.8
KBD4: IC29.15 (I2b), PL1.10
KBD5: IC29.4 (I1a), PL1.9
KBD6: IC29.17 (I3b), PL1.11
KBD7: IC29.2 (I0a), PL1.7
KEYBOARDEN: IC29.1 (OEa), IC29.19 (OEb)
KSEL: IC24.9 (Q3)
unnamed: C1.1, IC1.1, R2.2, R6.2
unnamed: C1.2, LS1.2
unnamed: C7.1, D4.1 (K), D5.2 (A), IC1.10 (+), IC2.5, R3.2, R9.1, R11.1, R15.2, R16.2, R86.2, R94.2, SKT2.1, SKT2.3, SKT2.6, SKT2.7, TR3.1 (E), TR3.3 (C)
unnamed: C14.1, IC14.16 (VCC), R43.2, R45.1
unnamed: D1.1 (K), IC1.13 (-), R4.1, R92.2
unnamed: D1.2 (A), IC2.2
unnamed: D2.1 (K), IC1.2 (-), R6.1
unnamed: D2.2 (A), IC2.12
unnamed: D3.1 (K), IC1.9 (-), R5.1, R93.2
unnamed: D3.2 (A), IC2.15
unnamed: D6.1 (K), TR2.1 (C), TR3.2 (B)
unnamed: D6.2 (A), R15.1
unnamed: IC1.5 (+), R41.2, R46.2, R47.2, R48.2, R49.2, R50.2, R51.2
unnamed: IC1.6 (-), R42.1, R44.2
unnamed: IC1.8, R3.1, R5.2
unnamed: IC1.3 (+), IC1.7, IC1.12 (+), R42.2, R92.1, R93.1, R94.1, R95.2, SKT2.4
unnamed: IC1.14, IC3.3, R84.2
unnamed: IC2.10, IC3.5
unnamed: IC2.11, IC24.19 (Q7)
unnamed: IC3.6, R7.1
unnamed: IC3.12, R8.1
unnamed: IC13.1 (Q3), IC16.17 (RRC), IC16.40 (TRC)
unnamed: IC13.3 (PE), IC13.12 (OUT)
unnamed: IC14.2 (Q0), R47.1
unnamed: IC14.5 (Q1), R49.1
unnamed: IC14.7 (Q2), R51.1
unnamed: IC14.10 (Q3), R50.1
unnamed: IC14.12 (Q4), R48.1
unnamed: IC14.15 (Q5), R46.1
unnamed: IC2.4, IC16.20 (RRI)
unnamed: IC2.6, IC16.21 (MR)
unnamed: IC2.9, IC16.25 (TRO)
unnamed: IC24.11 (Cp), IC57.4
unnamed: IC3.13, IC24.16 (Q6)
unnamed: R7.2, R10.1, TR1.2 (B)
unnamed: R11.2, SKT3.3
unnamed: R12.2, SKT3.1, TR1.1 (C)
unnamed: R8.2, R13.1, TR2.2 (B)
unnamed: R14.1, TR2.3 (E)
RD0: IC14.6 (D2), IC24.18 (D7), IC29.9 (O0b)
RD1: IC14.4 (D1), IC24.17 (D6), IC29.12 (O3a)
RD2: IC14.3 (D0), IC24.14 (D5), IC29.7 (O1b)
RD3: IC14.14 (D5), IC24.13 (D4), IC29.14 (O2a)
RD4: IC14.13 (D4), IC24.8 (D3), IC29.5 (O2b)
RD5: IC14.11 (D3), IC24.7 (D2), IC29.16 (O1a)
RD6: IC24.4 (D1), IC29.3 (O3b)
RD7: IC24.3 (D0), IC29.18 (O0a)
RU1: IC16.4 (RRD), IC16.18 (~DRR)
RU2: IC16.16 (SFD)
VIDEOLATCH: IC57.3
VSEL: IC24.6 (Q2)
WU1: IC16.23 (~TBRL)
~INT: PL1.6
~RESET: IC2.7, IC14.1 (~Mr), IC24.1 (~Mr)

Notes on the sheet:
SERIAL PORT
1 DATA OUT 2 GND 3 DATA IN 4 N/C 5 N/C
CASS, AUDIO + VISUAL CONTROL PORT
ANALOGUE
1 CASS O/P 2 GND 3 CASS I/P 4 H/L O/P 6 Relay - 7 Relay +
KEYBOARD
