Board-Folk/Camputers-Lynx/Lynx 96/Kicad/lynx96_pal.kicad_sch

## KiCad design Lynx 96/Kicad/lynx96_pal.kicad_sch (2025-07-15)

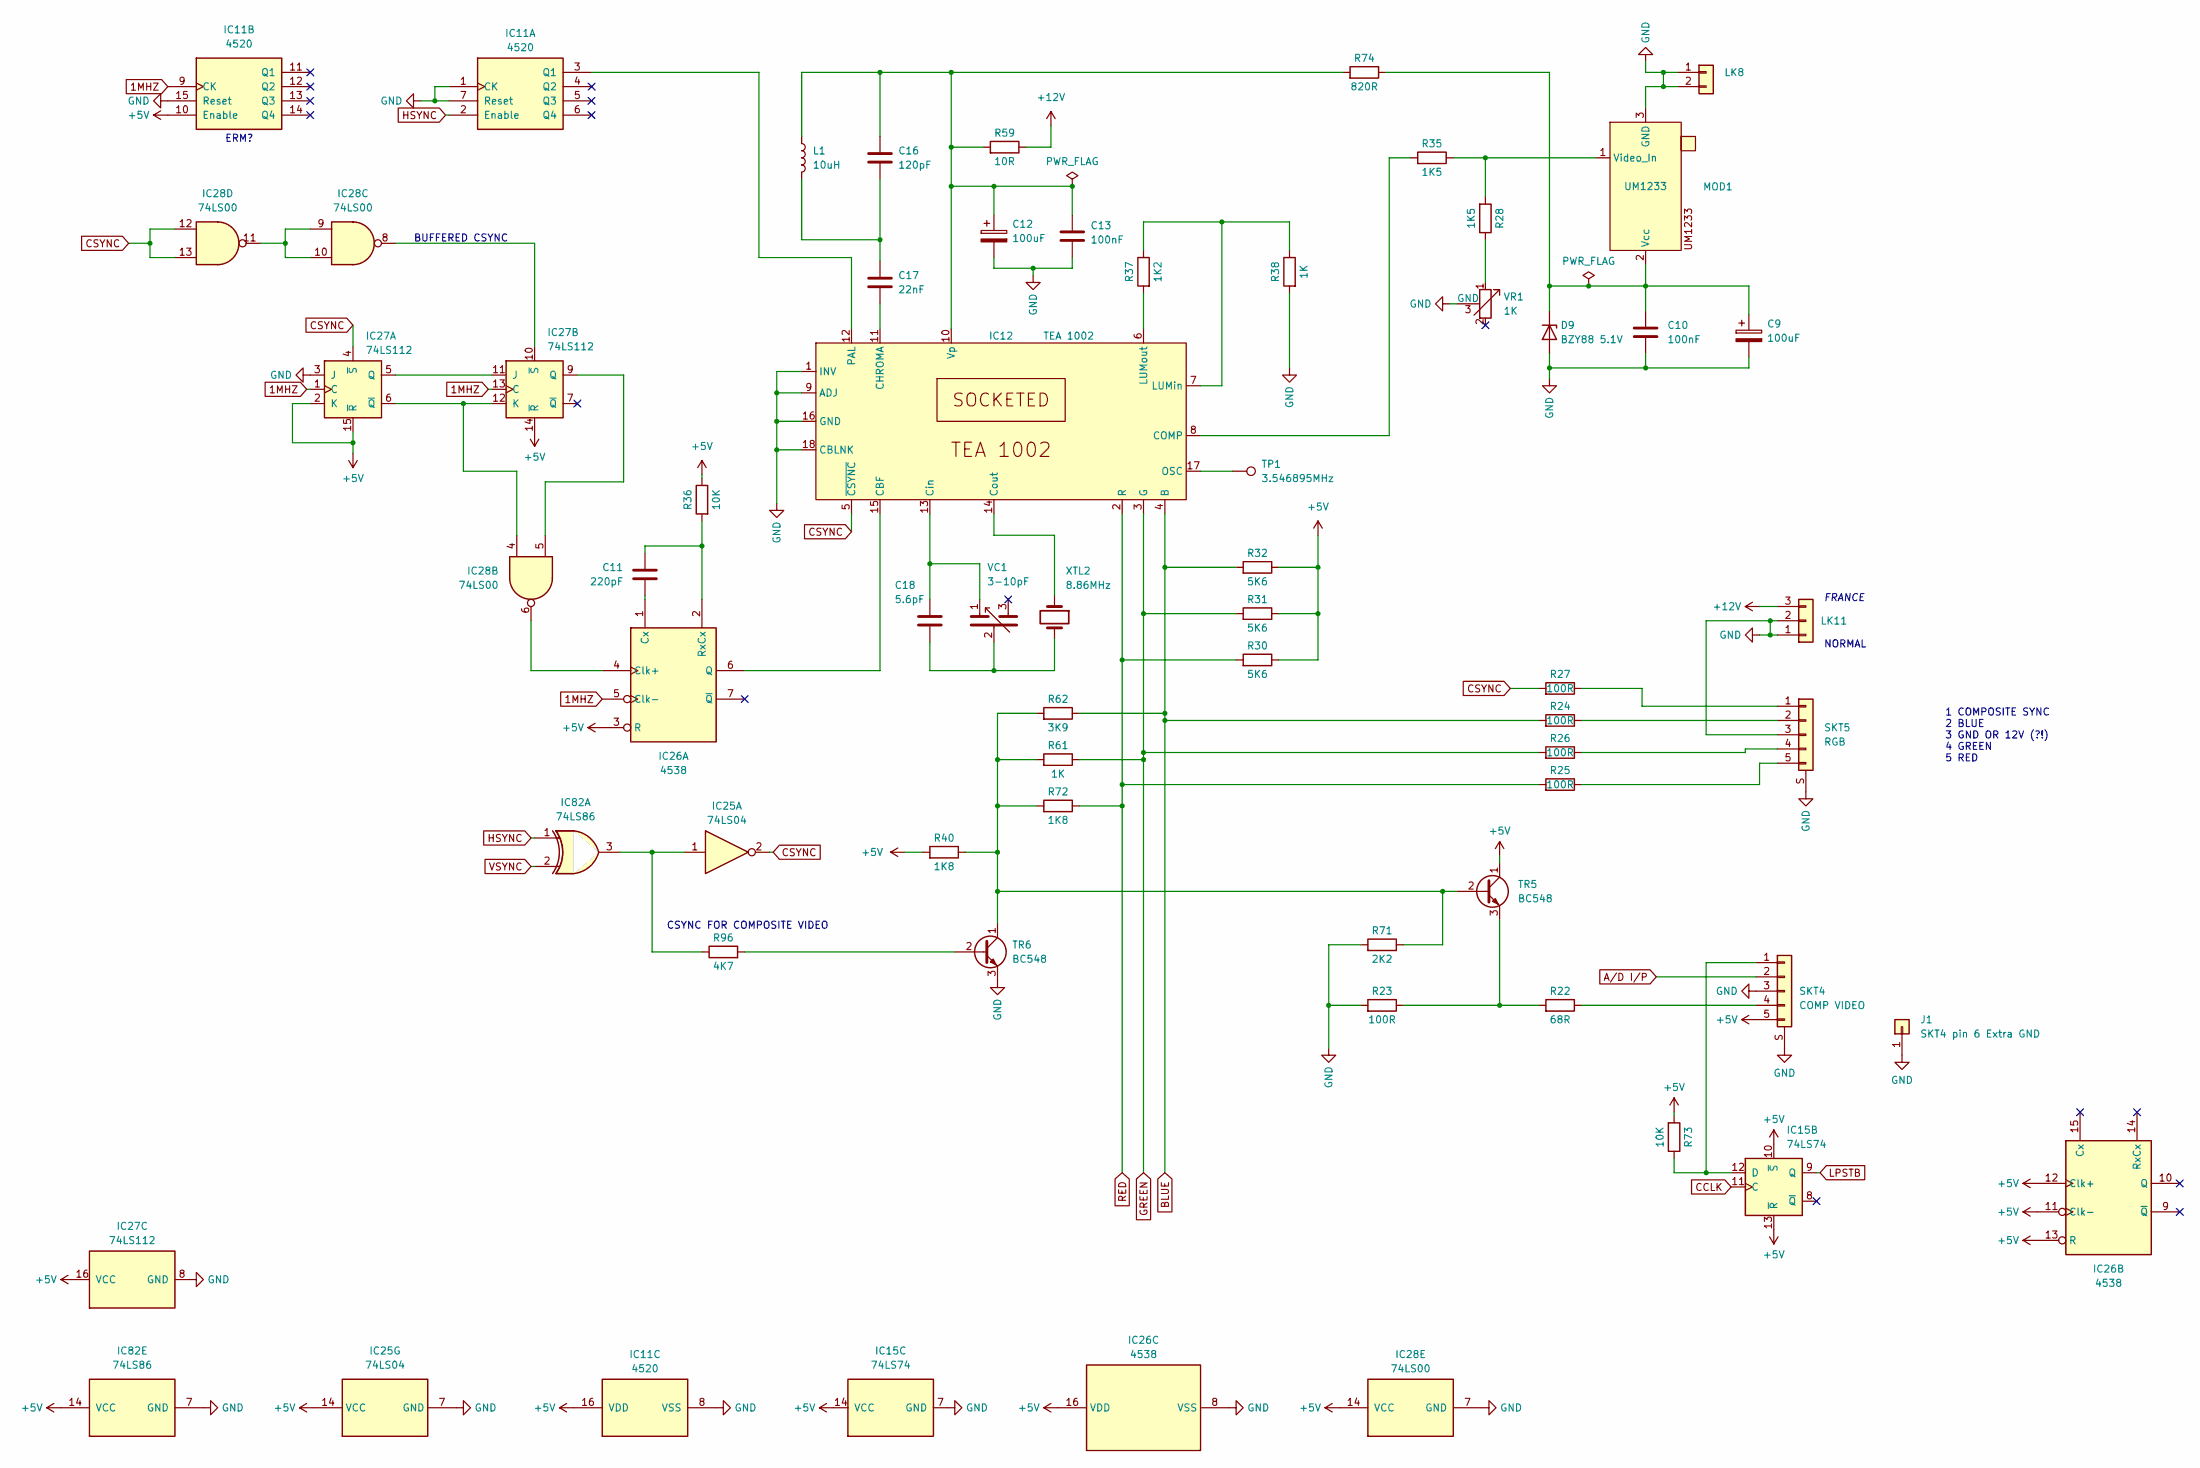
[picture p16: schematic lynx96_pal.kicad_sch]

Parts:
C9: 100uF; Elec_3.81mm
C10, C13: 100nF; Resistor 5.08mm
C11: 220pF; Resistor 5.08mm
C12: 100uF; Elec C12
C16: 120pF; Resistor 5.08mm
C17: 22nF; Resistor 5.08mm
C18: 5.6pF; Resistor 5.08mm
D9: BZY88 5.1V; Diode 5.08mm
IC11: 4520; DIP-16_W7.62mm
IC12: TEA 1002; DIP-18_W7.62mm
IC15: 74LS74; DIP-14_W7.62mm
IC25: 74LS04; DIP-14_W7.62mm
IC26: 4538; DIP-16_W7.62mm
IC27: 74LS112; DIP-16_W7.62mm
IC28: 74LS00; DIP-14_W7.62mm
IC82: 74LS86; DIP-14_W7.62mm
J1: SKT4 pin 6 Extra GND; Pin
L1: 10uH; L1
LK8: -; LK 2-pin 2.54mm - No Box
LK11: FRANCE; LK 11-Pin 2.54mm - No Box
MOD1: UM1233; Modulator
R22: 68R; Resistor 10.16mm
R23: 100R; Resistor 10.16mm
R24, R25, R26, R27: 100R; Resistor 3.81mm
R28: 1K5; Resistor R85
R30, R31: 5K6; Resistor 3.81mm
R32: 5K6; Resistor 10.16mm
R35: 1K5; Resistor 10.16mm
R36: 10K; Resistor 3.81mm
R37: 1K2; Resistor 10.16mm
R38: 1K; Resistor 10.16mm
R40: 1K8; Resistor R40
R59: 10R; Resistor 10.16mm
R61: 1K; Resistor 3.81mm
R62: 3K9; Resistor 3.81mm
R71: 2K2; Resistor R12
R72: 1K8; Resistor 3.81mm
R73: 10K; Resistor 5.08mm
R74: 820R; Resistor 10.16mm
R96: 4K7; Resistor 3.81mm
SKT4: COMP VIDEO; SKT5
SKT5: RGB; SKT5
TP1: 3.546895MHz; Test Point
TR5: BC548; Transistor
TR6: BC548; Transistor - No Box
VC1: 3-10pF; VC1 Trimmer
VR1: 1K; VR1
XTL2: 8.86MHz; 5.08mm Misc - No Box

Connections:
1MHZ: IC11.9 (CK), IC26.5 (Clk-), IC27.1 (C), IC27.13 (C)
+5V: IC11.10 (Enable), IC11.16 (VDD), IC15.10 (~S), IC15.13 (~R), IC15.14 (VCC), IC25.14 (VCC), IC26.3 (R), IC26.11 (Clk-), IC26.12 (Clk+), IC26.13 (R), IC26.16 (VDD), IC27.2 (K), IC27.14 (~R), IC27.15 (~R), IC27.16 (VCC), IC28.14 (VCC), IC82.14 (VCC), R30.1, R31.1, R32.1, R36.1, R40.2, R73.2, SKT4.5, TR5.1 (C)
+12V: LK11.3, R59.1
A/D I/P: SKT4.2
BLUE: IC12.4 (B), R24.2, R32.2, R62.1
CCLK: IC15.11 (C)
CSYNC: IC12.5 (~CSYNC), IC25.2, IC27.4 (~S), IC28.12, IC28.13, R27.2
GND: C9.2, C10.2, C12.2, C13.1, D9.2 (A), IC11.1 (CK), IC11.7 (Reset), IC11.8 (VSS), IC11.15 (Reset), IC12.1 (INV), IC12.9 (ADJ), IC12.16 (GND), IC12.18 (CBLNK), IC15.7 (GND), IC25.7 (GND), IC26.8 (VSS), IC27.3 (J), IC27.8 (GND), IC28.7 (GND), IC82.7 (GND), J1.1, LK8.1, LK8.2, LK11.1, LK11.2, MOD1.3 (GND), R23.2, R38.2, R71.2, SKT4.3, SKT4.S (SHIELD), SKT5.3, SKT5.S (SHIELD), TR6.3 (E), VR1.3 (GND)
GREEN: IC12.3 (G), R26.2, R31.2, R61.1
HSYNC: IC11.2 (Enable), IC82.1
LPSTB: IC15.9 (Q)
unnamed: C9.1, C10.1, D9.1 (K), MOD1.2 (Vcc), R74.1
unnamed: C11.1, IC26.1 (Cx)
unnamed: C11.2, IC26.2 (RxCx), R36.2
unnamed: C12.1, C13.2, C16.2, IC12.10 (Vp), L1.1, R59.2, R74.2
unnamed: C16.1, C17.2, L1.2
unnamed: C17.1, IC12.11 (CHROMA)
unnamed: C18.1, VC1.2, XTL2.2
unnamed: C18.2, IC12.13 (Cin), VC1.1
unnamed: IC11.3 (Q1), IC12.12 (PAL)
unnamed: IC12.6 (LUMout), R37.2
unnamed: IC12.7 (LUMin), R37.1, R38.1
unnamed: IC12.8 (COMP), R35.2
unnamed: IC12.14 (Cout), XTL2.1
unnamed: IC12.15 (CBF), IC26.6 (Q)
unnamed: IC12.17 (OSC), TP1.1
unnamed: IC15.12 (D), R73.1, SKT4.1
unnamed: IC25.1, IC82.3, R96.1
unnamed: IC26.4 (Clk+), IC28.6
unnamed: IC27.9 (Q), IC28.5
unnamed: IC27.10 (~S), IC28.8
unnamed: IC27.5 (Q), IC27.11 (J)
unnamed: IC27.6 (~Q), IC27.12 (K), IC28.4
unnamed: IC28.9, IC28.10, IC28.11
unnamed: MOD1.1 (Video_In), R28.2, R35.1
unnamed: R22.1, SKT4.4
unnamed: R22.2, R23.1, TR5.3 (E)
unnamed: R24.1, SKT5.2
unnamed: R25.1, SKT5.5
unnamed: R26.1, SKT5.4
unnamed: R27.1, SKT5.1
unnamed: R28.1, VR1.1
unnamed: R40.1, R61.2, R62.2, R71.1, R72.2, TR5.2 (B), TR6.1 (C)
unnamed: R96.2, TR6.2 (B)
RED: IC12.2 (R), R25.2, R30.2, R72.1
VSYNC: IC82.2

Notes on the sheet:
1 COMPOSITE SYNC 2 BLUE 3 GND OR 12V (?!) 4 GREEN 5 RED
BUFFERED CSYNC
FRANCE
NORMAL
CSYNC FOR COMPOSITE VIDEO
ERM?
