Board-Folk/Camputers-Lynx/Lynx 96/Kicad/lynx96_power.kicad_sch

## KiCad design Lynx 96/Kicad/lynx96_power.kicad_sch (2025-07-15)

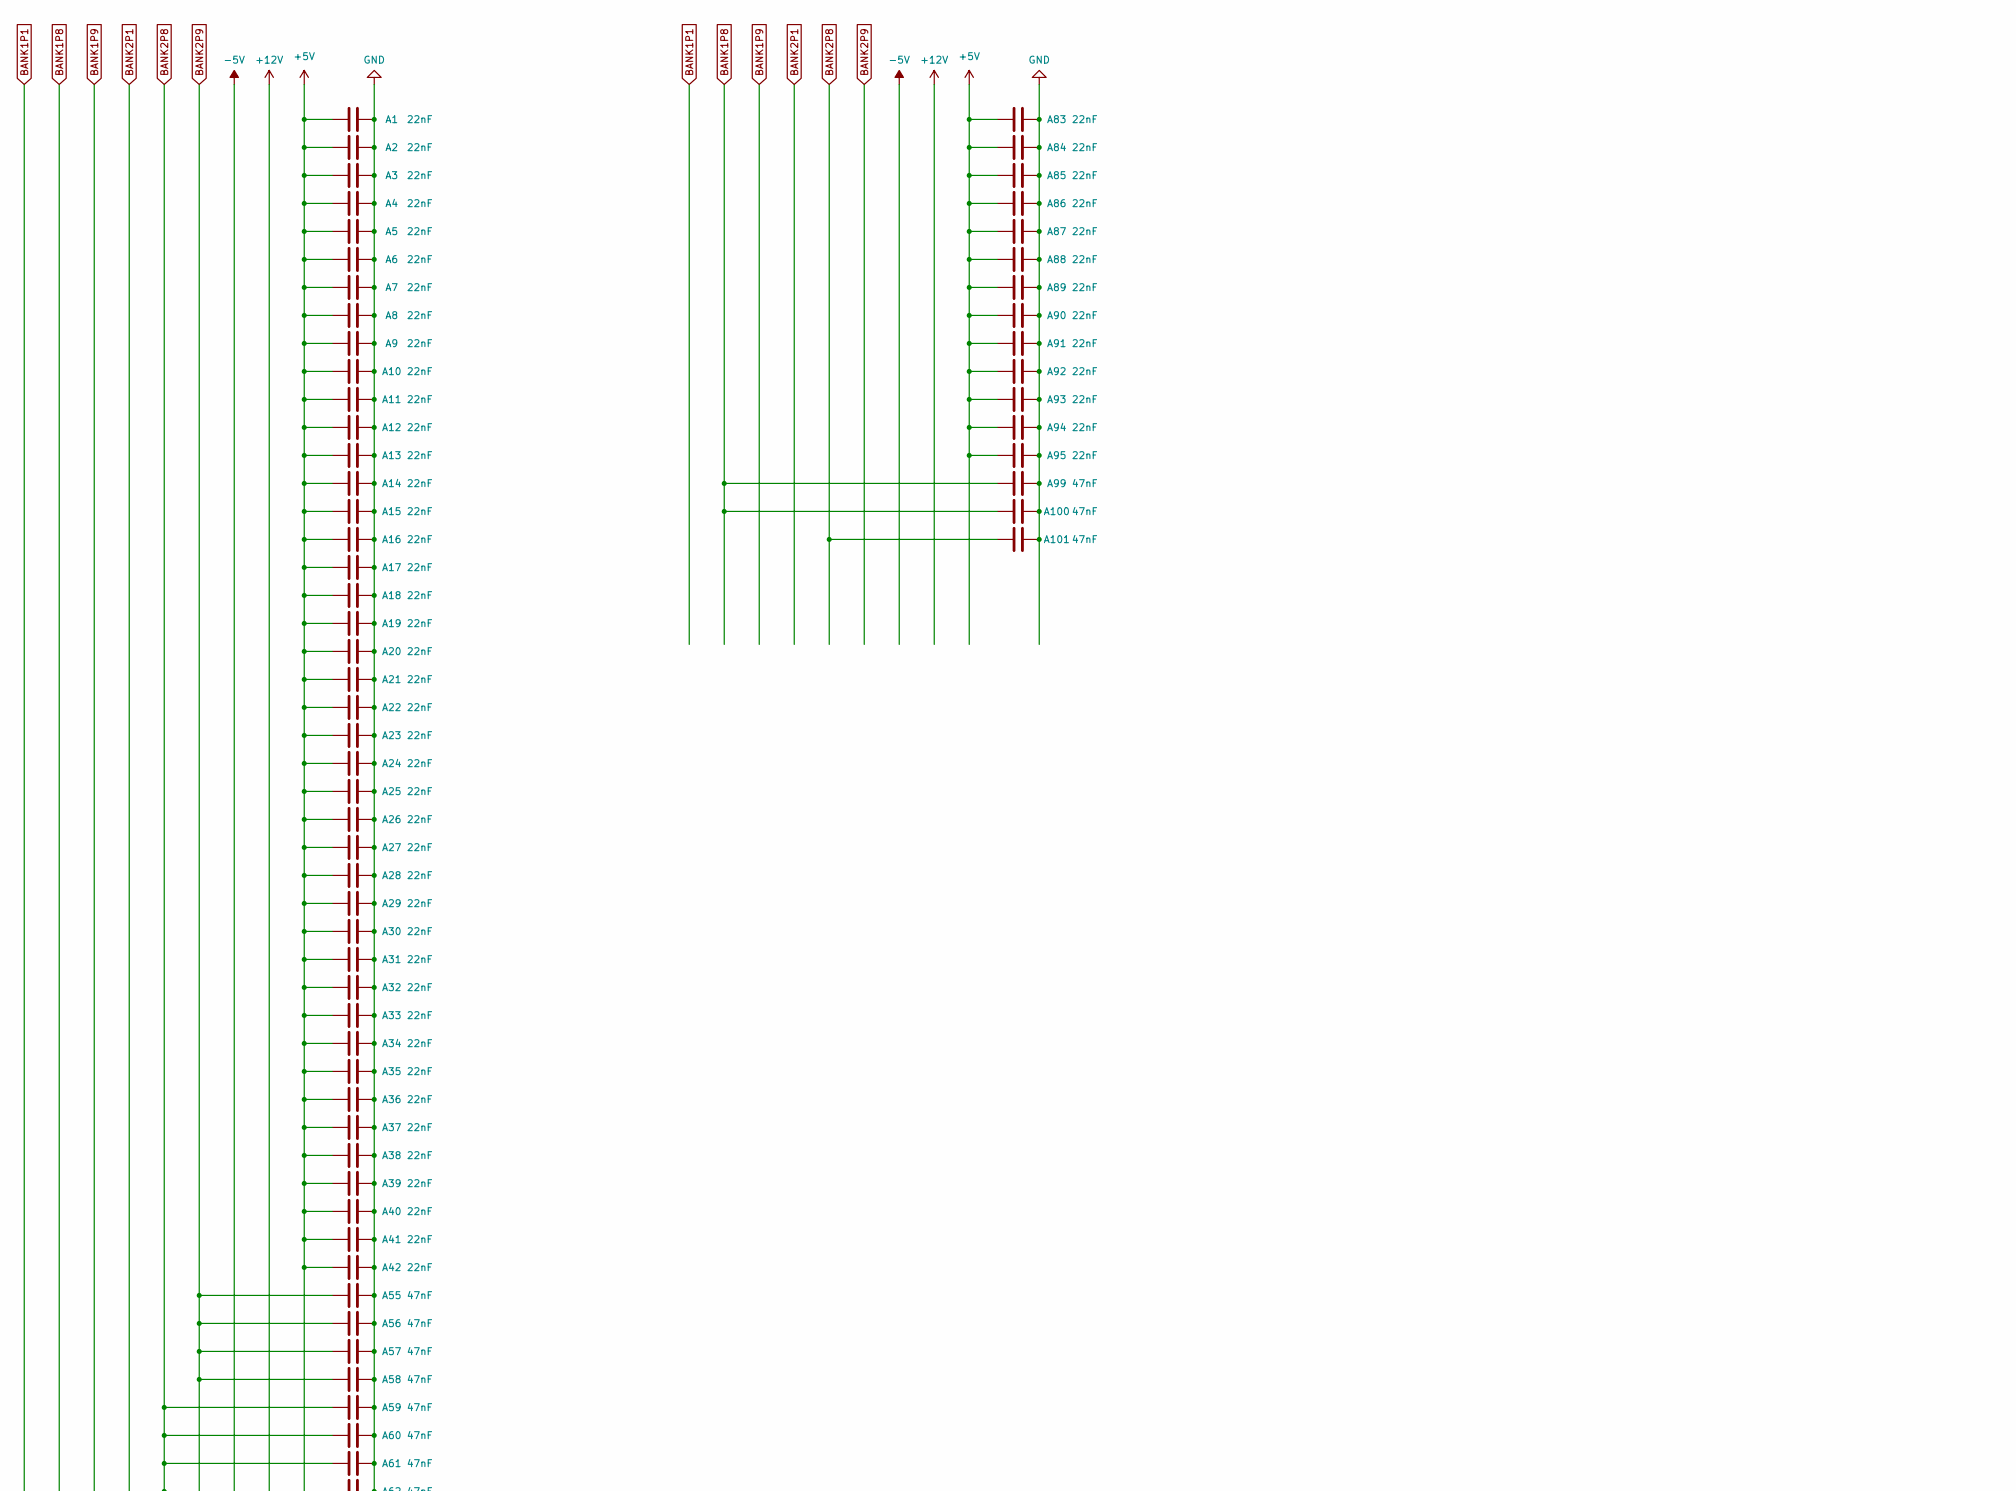
[picture p17: schematic lynx96_power.kicad_sch, part in row 1, column 1]

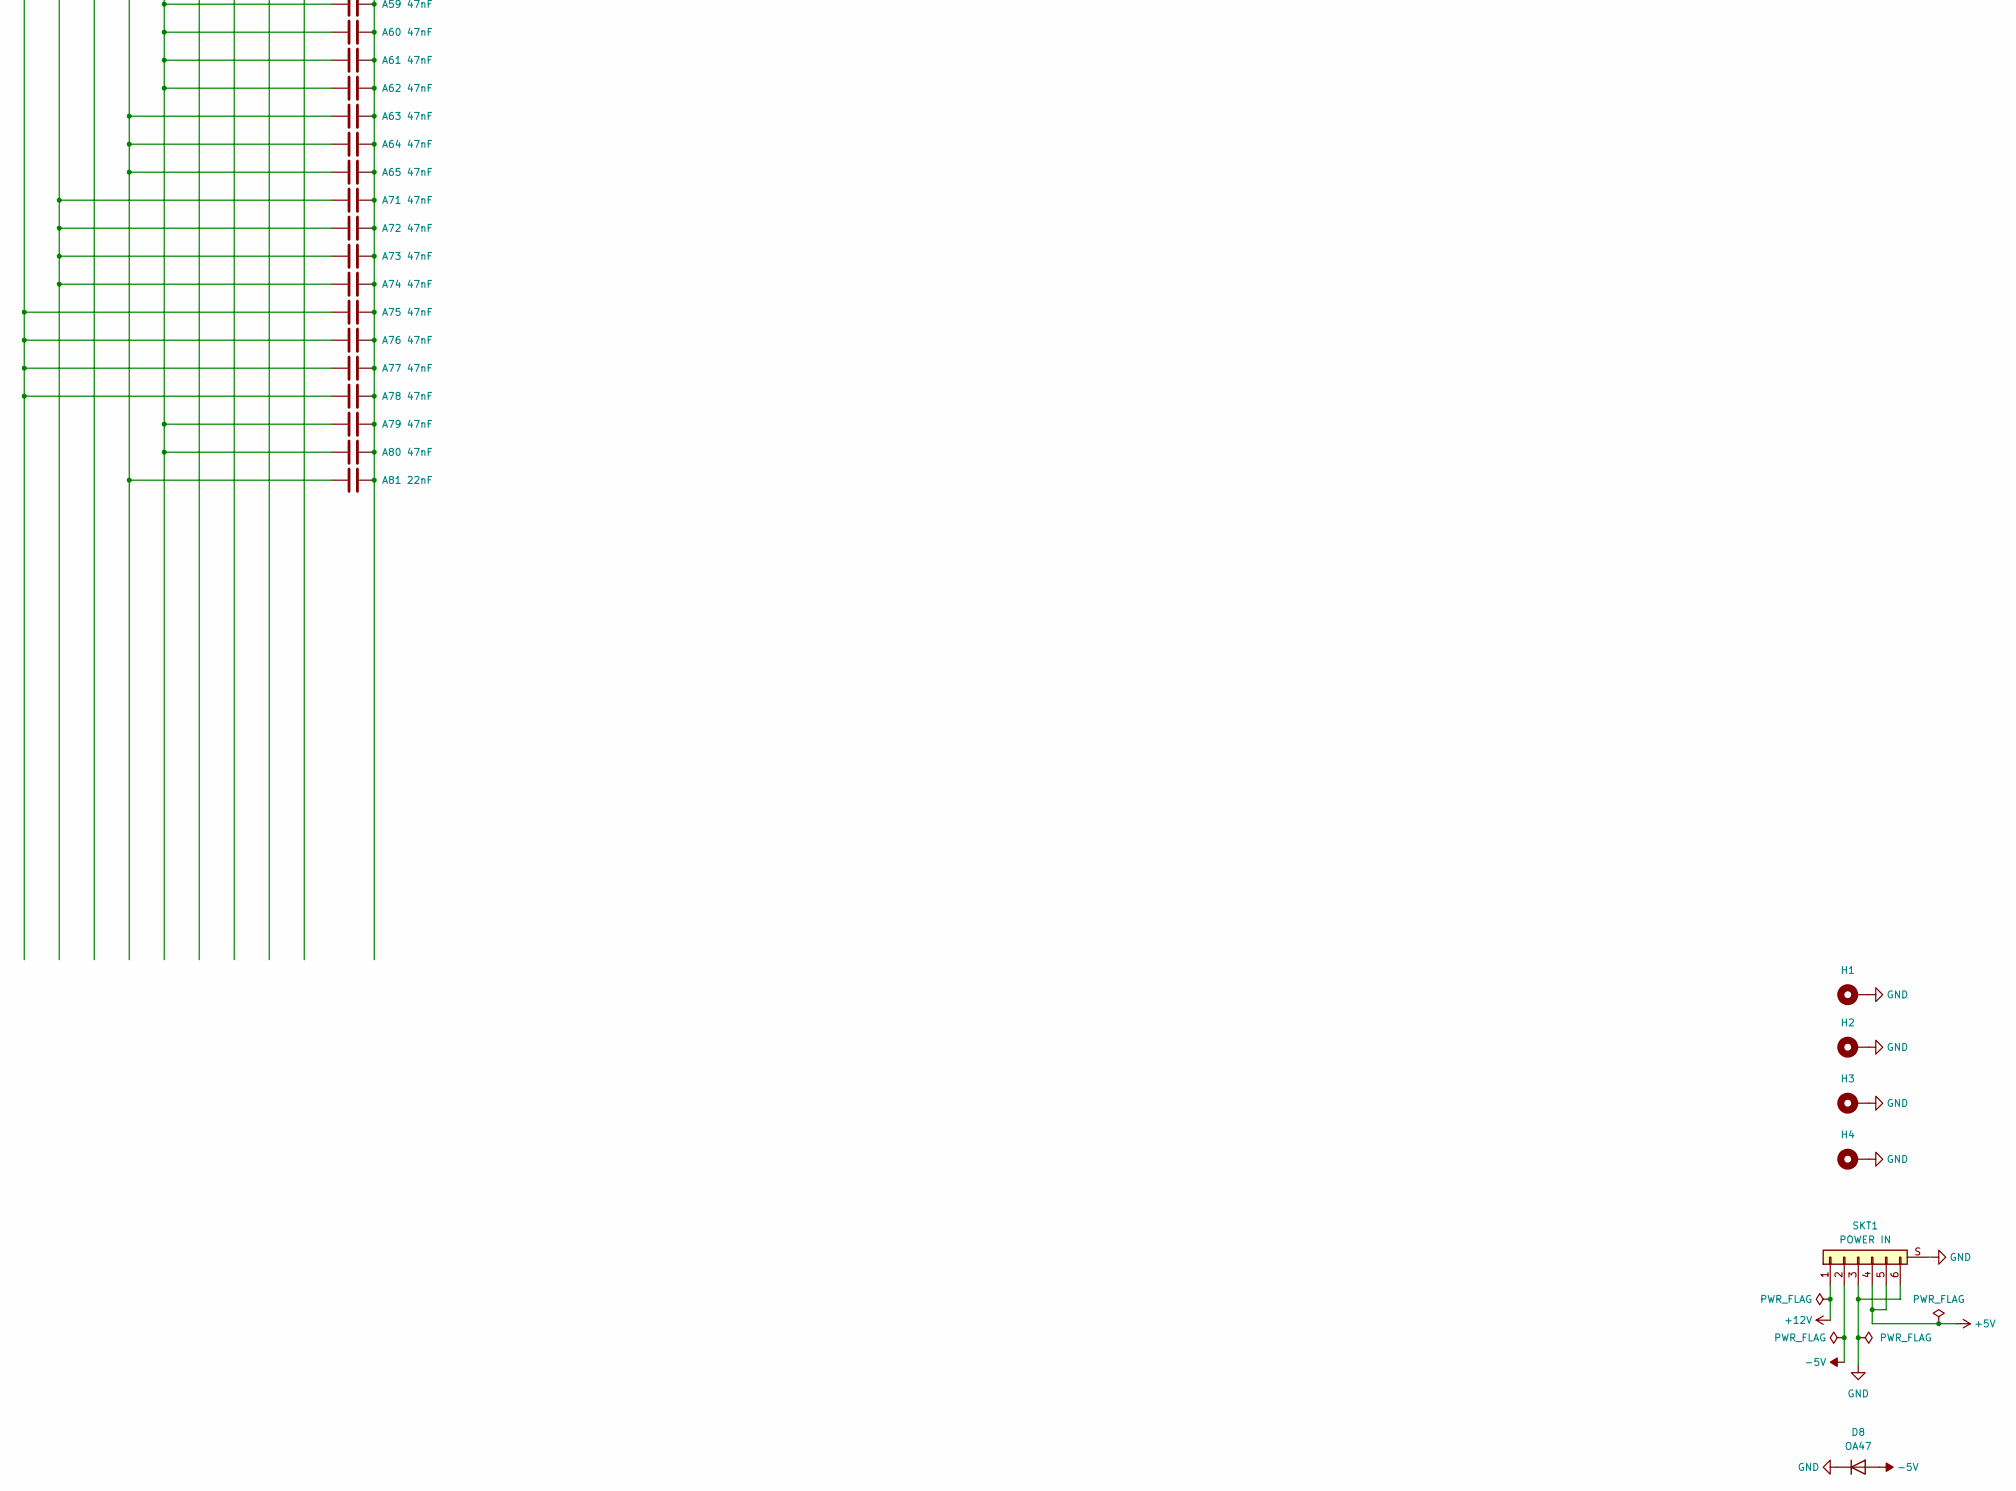
[picture p18: schematic lynx96_power.kicad_sch, part in row 2, column 1]

Parts:
A1, A2, A3, A4, A5, A6, A7, A8, A9, A10, A11, A12, A13, A14, A15, A16, A17, A18, A19, A20, A21, A22, A23, A24, A25, A26, A27, A28, A29, A30, A31, A32, A33, A34, A35, A36, A37, A38, A39, A40, A41, A42, A81, A83, A84, A85, A86, A87, A88, A89, A90, A91, A92, A93, A94, A95: 22nF; A_Standard
A55, A56, A57, A58, A59, A60, A61, A62, A63, A64, A65, A71, A72, A73, A74, A75, A76, A77, A78, A79, A80, A99, A100, A101: 47nF; A_Standard
D8: OA47; Diode D8
H1, H2, H3, H4: GND; Mounting Hole
SKT1: POWER IN; DIN6

Connections:
+5V: A1.1, A2.1, A3.1, A4.1, A5.1, A6.1, A7.1, A8.1, A9.1, A10.1, A11.1, A12.1, A13.1, A14.1, A15.1, A16.1, A17.1, A18.1, A19.1, A20.1, A21.1, A22.1, A23.1, A24.1, A25.1, A26.1, A27.1, A28.1, A29.1, A30.1, A31.1, A32.1, A33.1, A34.1, A35.1, A36.1, A37.1, A38.1, A39.1, A40.1, A41.1, A42.1, A83.1, A84.1, A85.1, A86.1, A87.1, A88.1, A89.1, A90.1, A91.1, A92.1, A93.1, A94.1, A95.1, SKT1.4, SKT1.5
+12V: SKT1.1
-5V: D8.2 (A), SKT1.2
BANK1P1: A75.1, A76.1, A77.1, A78.1
BANK1P8: A71.1, A72.1, A73.1, A74.1, A99.1, A100.1
BANK2P1: A63.1, A64.1, A65.1, A81.1
BANK2P8: A59.1, A60.1, A61.1, A62.1, A79.1, A80.1, A101.1
BANK2P9: A55.1, A56.1, A57.1, A58.1
GND: A1.2, A2.2, A3.2, A4.2, A5.2, A6.2, A7.2, A8.2, A9.2, A10.2, A11.2, A12.2, A13.2, A14.2, A15.2, A16.2, A17.2, A18.2, A19.2, A20.2, A21.2, A22.2, A23.2, A24.2, A25.2, A26.2, A27.2, A28.2, A29.2, A30.2, A31.2, A32.2, A33.2, A34.2, A35.2, A36.2, A37.2, A38.2, A39.2, A40.2, A41.2, A42.2, A55.2, A56.2, A57.2, A58.2, A59.2, A60.2, A61.2, A62.2, A63.2, A64.2, A65.2, A71.2, A72.2, A73.2, A74.2, A75.2, A76.2, A77.2, A78.2, A79.2, A80.2, A81.2, A83.2, A84.2, A85.2, A86.2, A87.2, A88.2, A89.2, A90.2, A91.2, A92.2, A93.2, A94.2, A95.2, A99.2, A100.2, A101.2, D8.1 (K), H1.1, H2.1, H3.1, H4.1, SKT1.3, SKT1.6, SKT1.S (SHIELD)
