Board-Folk/Camputers-Lynx/Lynx 96/Kicad/lynx96_ram.kicad_sch

## KiCad design Lynx 96/Kicad/lynx96_ram.kicad_sch (2025-07-15)

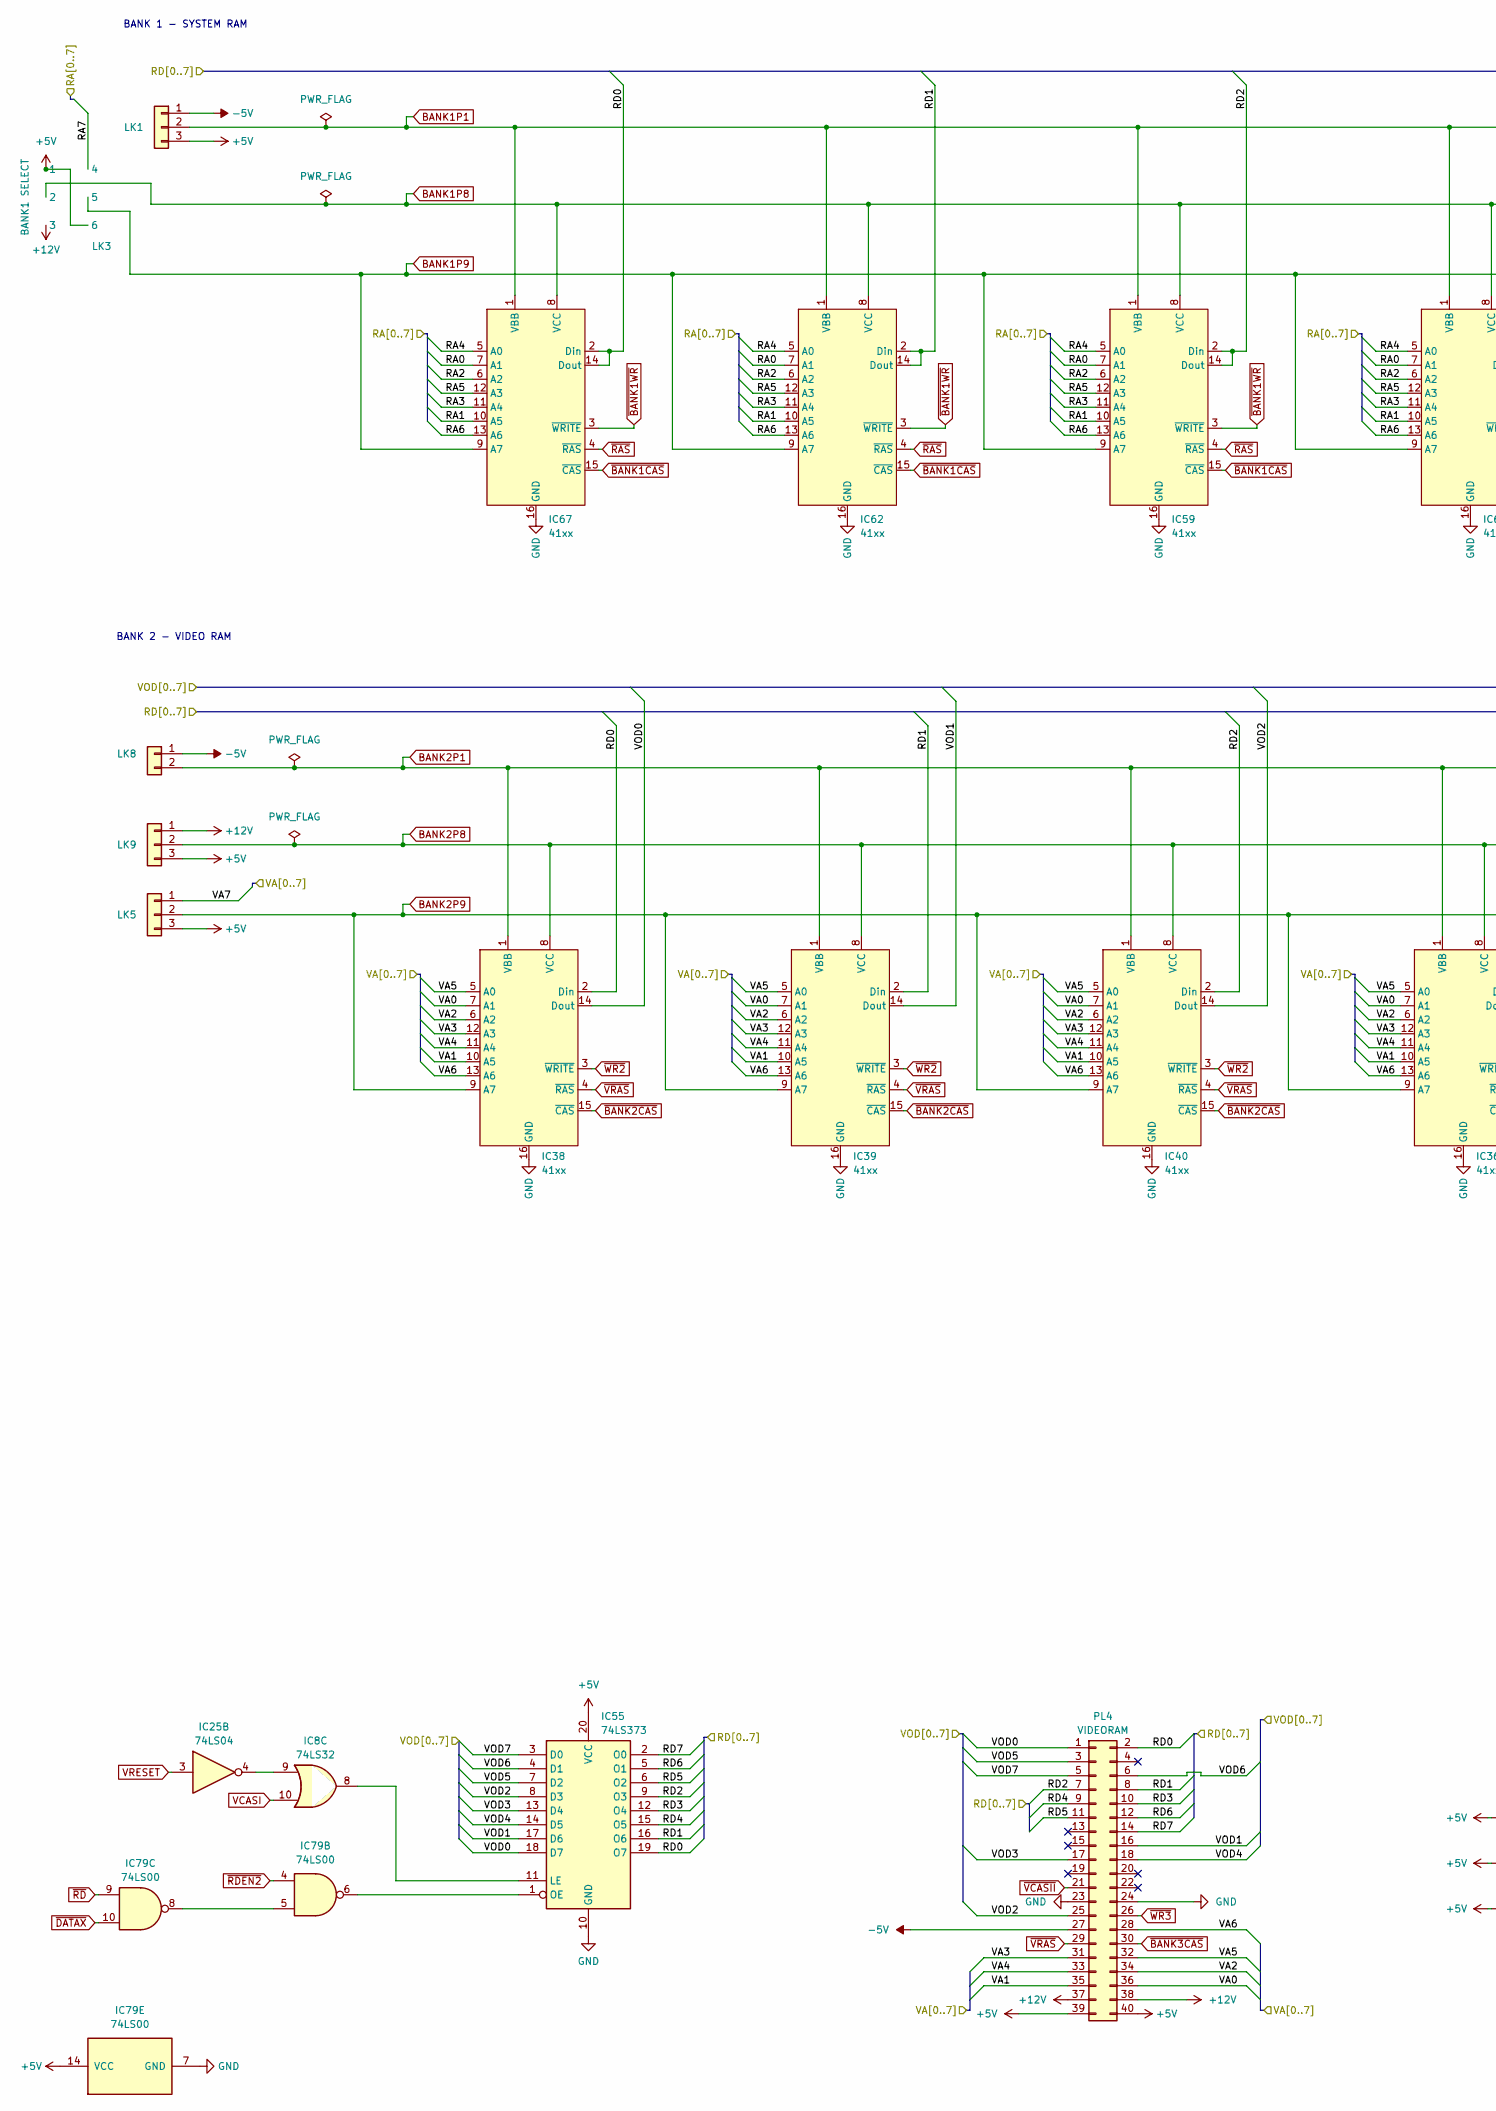
[picture p19: schematic lynx96_ram.kicad_sch, part in row 1, column 1]

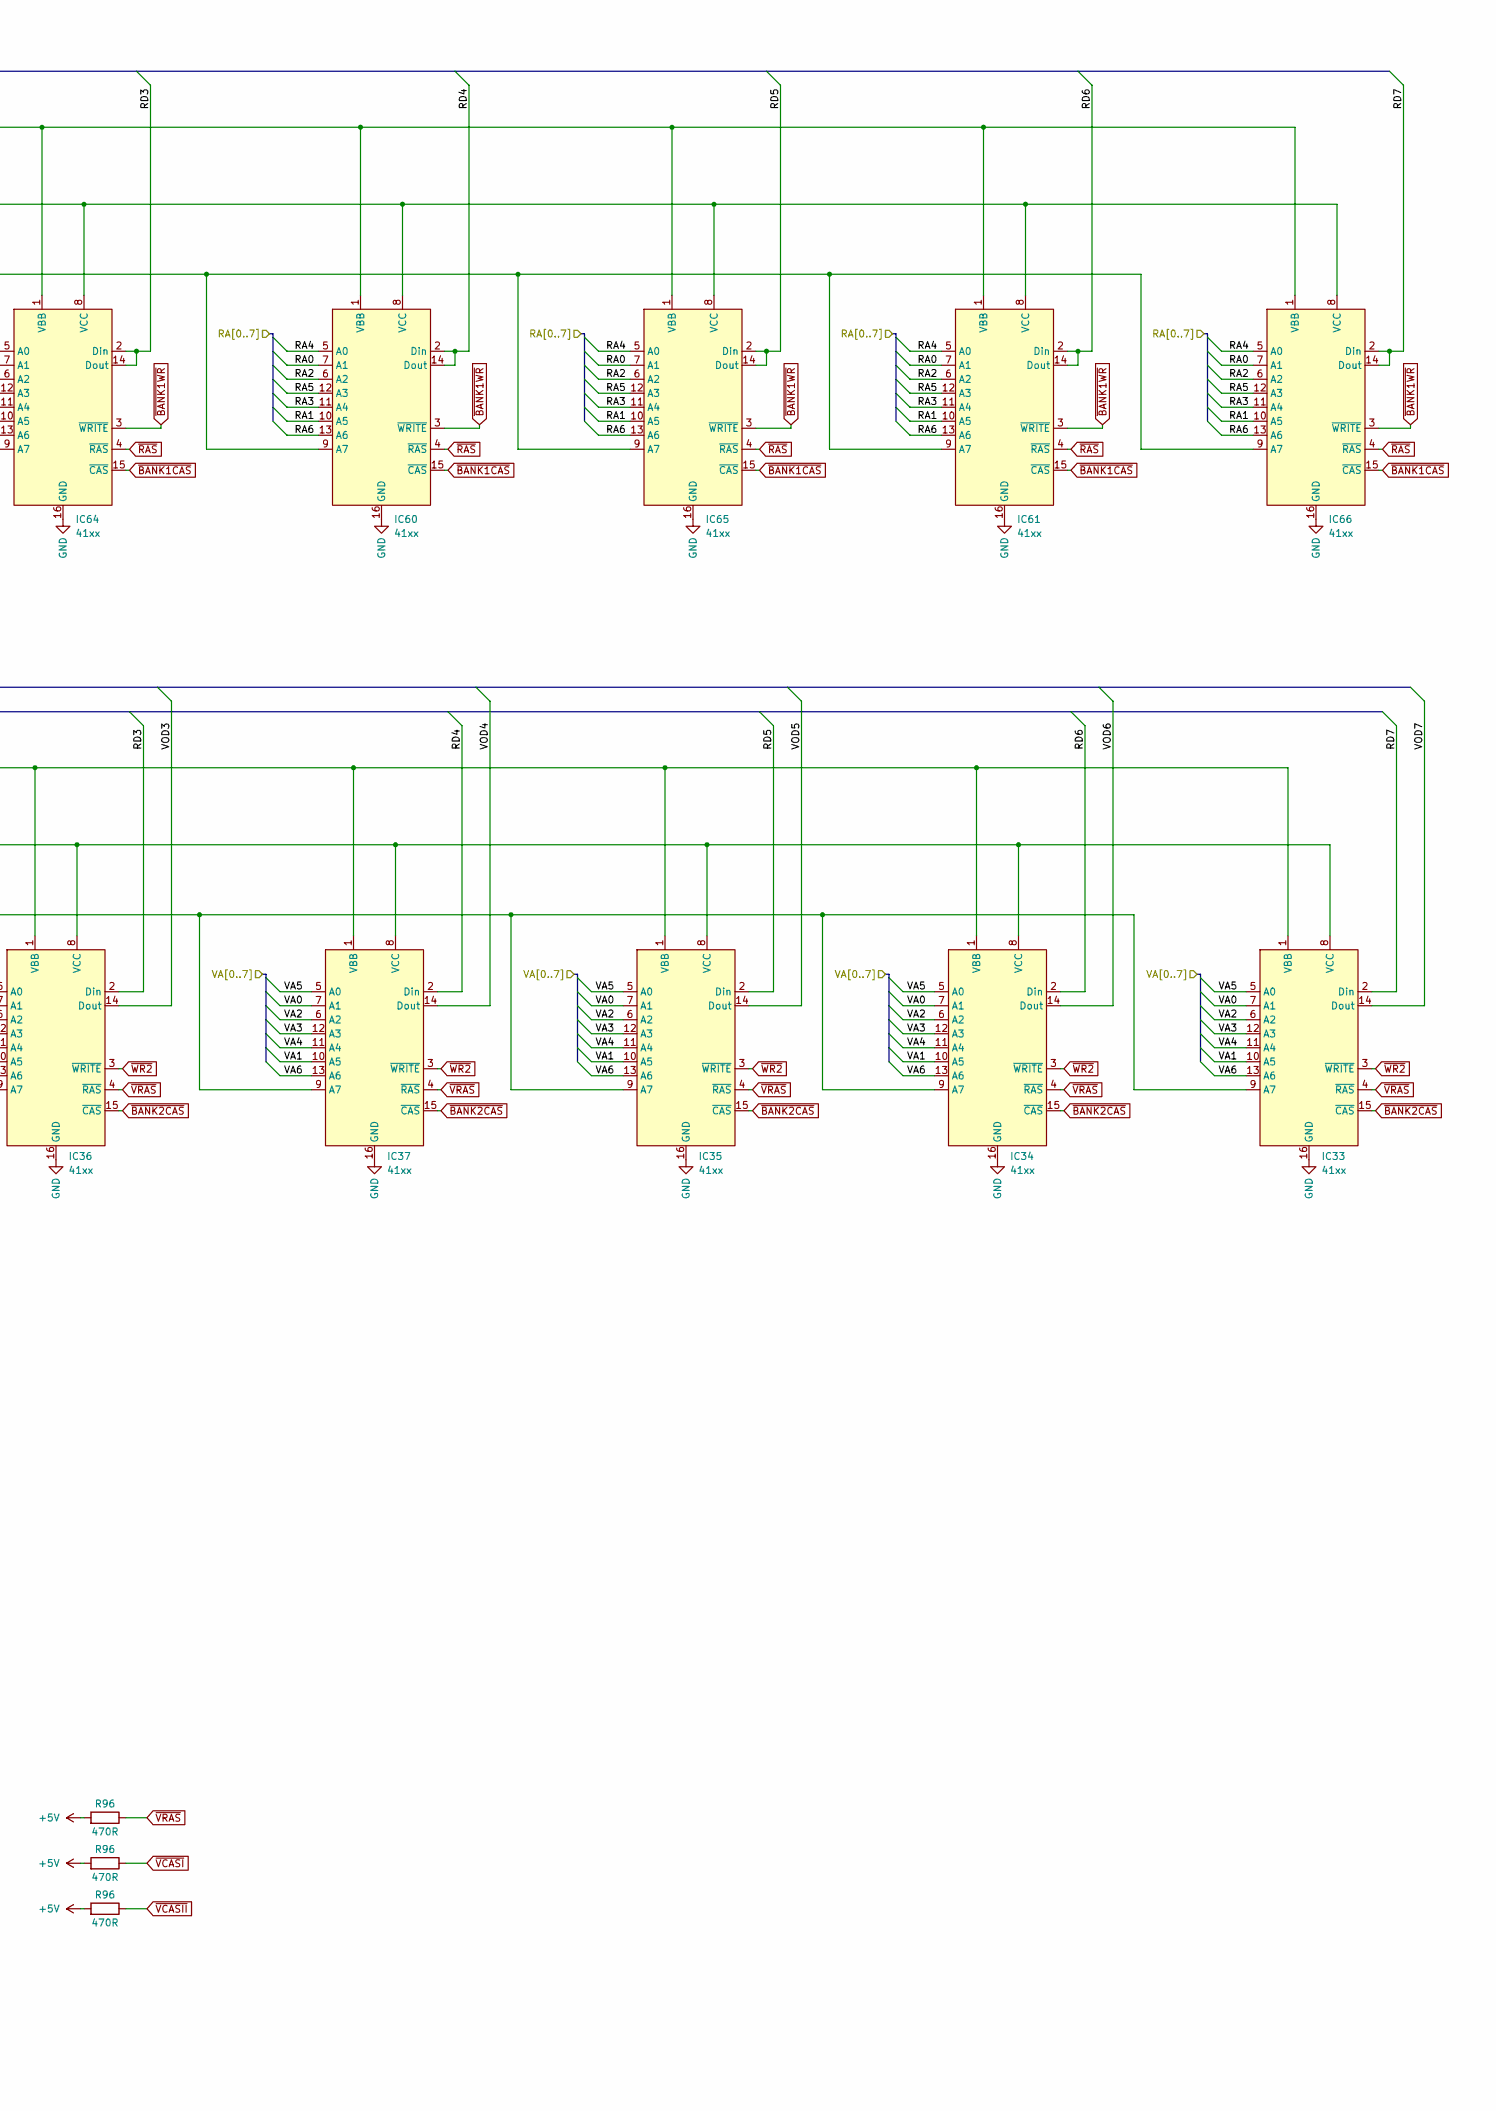
[picture p20: schematic lynx96_ram.kicad_sch, part in row 1, column 2]

Parts:
IC8: 74LS32; DIP-14_W7.62mm
IC25: 74LS04; DIP-14_W7.62mm
IC33, IC34, IC35, IC36, IC37, IC38, IC39, IC40, IC59, IC60, IC61, IC62, IC64, IC65, IC66, IC67: 41xx; DIP-16_W7.62mm
IC55: 74LS373; DIP-20_W7.62mm
IC79: 74LS00; DIP-14_W7.62mm
LK1, LK5, LK9: -; LK 3-Pin 2.54mm - No Box
LK3: BANK1 SELECT; LK2
LK8: -; LK 2-pin 2.54mm - No Box
PL4: VIDEORAM; PL - 02x20
R96: 470R; Resistor 10.16mm

Connections:
+5V: IC55.20 (VCC), IC79.14 (VCC), LK1.3, LK3.1, LK3.6, LK5.3, LK9.3, PL4.39, PL4.40, R96.2
+12V: LK3.3, LK9.1, PL4.37, PL4.38
-5V: LK1.1, LK8.1, PL4.27
BANK1P1: IC59.1 (VBB), IC60.1 (VBB), IC61.1 (VBB), IC62.1 (VBB), IC64.1 (VBB), IC65.1 (VBB), IC66.1 (VBB), IC67.1 (VBB), LK1.2
BANK1P8: IC59.8 (VCC), IC60.8 (VCC), IC61.8 (VCC), IC62.8 (VCC), IC64.8 (VCC), IC65.8 (VCC), IC66.8 (VCC), IC67.8 (VCC), LK3.2
BANK1P9: IC59.9 (A7), IC60.9 (A7), IC61.9 (A7), IC62.9 (A7), IC64.9 (A7), IC65.9 (A7), IC66.9 (A7), IC67.9 (A7), LK3.5
BANK2P1: IC33.1 (VBB), IC34.1 (VBB), IC35.1 (VBB), IC36.1 (VBB), IC37.1 (VBB), IC38.1 (VBB), IC39.1 (VBB), IC40.1 (VBB), LK8.2
BANK2P8: IC33.8 (VCC), IC34.8 (VCC), IC35.8 (VCC), IC36.8 (VCC), IC37.8 (VCC), IC38.8 (VCC), IC39.8 (VCC), IC40.8 (VCC), LK9.2
BANK2P9: IC33.9 (A7), IC34.9 (A7), IC35.9 (A7), IC36.9 (A7), IC37.9 (A7), IC38.9 (A7), IC39.9 (A7), IC40.9 (A7), LK5.2
GND: IC33.16 (GND), IC34.16 (GND), IC35.16 (GND), IC36.16 (GND), IC37.16 (GND), IC38.16 (GND), IC39.16 (GND), IC40.16 (GND), IC55.10 (GND), IC59.16 (GND), IC60.16 (GND), IC61.16 (GND), IC62.16 (GND), IC64.16 (GND), IC65.16 (GND), IC66.16 (GND), IC67.16 (GND), IC79.7 (GND), PL4.23, PL4.24
unnamed: IC8.9, IC25.4
unnamed: IC55.1 (OE), IC79.6
unnamed: IC8.8, IC55.11 (LE)
unnamed: IC79.5, IC79.8
RA0: IC59.7 (A1), IC60.7 (A1), IC61.7 (A1), IC62.7 (A1), IC64.7 (A1), IC65.7 (A1), IC66.7 (A1), IC67.7 (A1)
RA1: IC59.10 (A5), IC60.10 (A5), IC61.10 (A5), IC62.10 (A5), IC64.10 (A5), IC65.10 (A5), IC66.10 (A5), IC67.10 (A5)
RA2: IC59.6 (A2), IC60.6 (A2), IC61.6 (A2), IC62.6 (A2), IC64.6 (A2), IC65.6 (A2), IC66.6 (A2), IC67.6 (A2)
RA3: IC59.11 (A4), IC60.11 (A4), IC61.11 (A4), IC62.11 (A4), IC64.11 (A4), IC65.11 (A4), IC66.11 (A4), IC67.11 (A4)
RA4: IC59.5 (A0), IC60.5 (A0), IC61.5 (A0), IC62.5 (A0), IC64.5 (A0), IC65.5 (A0), IC66.5 (A0), IC67.5 (A0)
RA5: IC59.12 (A3), IC60.12 (A3), IC61.12 (A3), IC62.12 (A3), IC64.12 (A3), IC65.12 (A3), IC66.12 (A3), IC67.12 (A3)
RA6: IC59.13 (A6), IC60.13 (A6), IC61.13 (A6), IC62.13 (A6), IC64.13 (A6), IC65.13 (A6), IC66.13 (A6), IC67.13 (A6)
RA7: LK3.4
RD0: IC38.2 (Din), IC55.19 (O7), IC67.2 (Din), IC67.14 (Dout), PL4.2
RD1: IC39.2 (Din), IC55.16 (O6), IC62.2 (Din), IC62.14 (Dout), PL4.8
RD2: IC40.2 (Din), IC55.9 (O3), IC59.2 (Din), IC59.14 (Dout), PL4.7
RD3: IC36.2 (Din), IC55.12 (O4), IC64.2 (Din), IC64.14 (Dout), PL4.10
RD4: IC37.2 (Din), IC55.15 (O5), IC60.2 (Din), IC60.14 (Dout), PL4.9
RD5: IC35.2 (Din), IC55.6 (O2), IC65.2 (Din), IC65.14 (Dout), PL4.11
RD6: IC34.2 (Din), IC55.5 (O1), IC61.2 (Din), IC61.14 (Dout), PL4.12
RD7: IC33.2 (Din), IC55.2 (O0), IC66.2 (Din), IC66.14 (Dout), PL4.14
VA0: IC33.7 (A1), IC34.7 (A1), IC35.7 (A1), IC36.7 (A1), IC37.7 (A1), IC38.7 (A1), IC39.7 (A1), IC40.7 (A1), PL4.36
VA1: IC33.10 (A5), IC34.10 (A5), IC35.10 (A5), IC36.10 (A5), IC37.10 (A5), IC38.10 (A5), IC39.10 (A5), IC40.10 (A5), PL4.35
VA2: IC33.6 (A2), IC34.6 (A2), IC35.6 (A2), IC36.6 (A2), IC37.6 (A2), IC38.6 (A2), IC39.6 (A2), IC40.6 (A2), PL4.34
VA3: IC33.12 (A3), IC34.12 (A3), IC35.12 (A3), IC36.12 (A3), IC37.12 (A3), IC38.12 (A3), IC39.12 (A3), IC40.12 (A3), PL4.31
VA4: IC33.11 (A4), IC34.11 (A4), IC35.11 (A4), IC36.11 (A4), IC37.11 (A4), IC38.11 (A4), IC39.11 (A4), IC40.11 (A4), PL4.33
VA5: IC33.5 (A0), IC34.5 (A0), IC35.5 (A0), IC36.5 (A0), IC37.5 (A0), IC38.5 (A0), IC39.5 (A0), IC40.5 (A0), PL4.32
VA6: IC33.13 (A6), IC34.13 (A6), IC35.13 (A6), IC36.13 (A6), IC37.13 (A6), IC38.13 (A6), IC39.13 (A6), IC40.13 (A6), PL4.28
VA7: LK5.1
VCASI: IC8.10
VOD0: IC38.14 (Dout), IC55.18 (D7), PL4.1
VOD1: IC39.14 (Dout), IC55.17 (D6), PL4.16
VOD2: IC40.14 (Dout), IC55.8 (D3), PL4.25
VOD3: IC36.14 (Dout), IC55.13 (D4), PL4.17
VOD4: IC37.14 (Dout), IC55.14 (D5), PL4.18
VOD5: IC35.14 (Dout), IC55.7 (D2), PL4.3
VOD6: IC34.14 (Dout), IC55.4 (D1), PL4.6
VOD7: IC33.14 (Dout), IC55.3 (D0), PL4.5
VRESET: IC25.3
~BANK1CAS: IC59.15 (~CAS), IC60.15 (~CAS), IC61.15 (~CAS), IC62.15 (~CAS), IC64.15 (~CAS), IC65.15 (~CAS), IC66.15 (~CAS), IC67.15 (~CAS)
~BANK1WR: IC59.3 (~WRITE), IC60.3 (~WRITE), IC61.3 (~WRITE), IC62.3 (~WRITE), IC64.3 (~WRITE), IC65.3 (~WRITE), IC66.3 (~WRITE), IC67.3 (~WRITE)
~BANK2CAS: IC33.15 (~CAS), IC34.15 (~CAS), IC35.15 (~CAS), IC36.15 (~CAS), IC37.15 (~CAS), IC38.15 (~CAS), IC39.15 (~CAS), IC40.15 (~CAS)
~BANK3CAS: PL4.30
~DATAX: IC79.10
~RAS: IC59.4 (~RAS), IC60.4 (~RAS), IC61.4 (~RAS), IC62.4 (~RAS), IC64.4 (~RAS), IC65.4 (~RAS), IC66.4 (~RAS), IC67.4 (~RAS)
~RDEN2: IC79.4
~RD: IC79.9
~VCASII: PL4.21, R96.1
~VCASI: R96.1
~VRAS: IC33.4 (~RAS), IC34.4 (~RAS), IC35.4 (~RAS), IC36.4 (~RAS), IC37.4 (~RAS), IC38.4 (~RAS), IC39.4 (~RAS), IC40.4 (~RAS), PL4.29, R96.1
~WR2: IC33.3 (~WRITE), IC34.3 (~WRITE), IC35.3 (~WRITE), IC36.3 (~WRITE), IC37.3 (~WRITE), IC38.3 (~WRITE), IC39.3 (~WRITE), IC40.3 (~WRITE)
~WR3: PL4.26

Notes on the sheet:
BANK 2 - VIDEO RAM
BANK 1 - SYSTEM RAM
