Board-Folk/Camputers-Lynx/Lynx 96/Kicad/lynx96_ramsignals.kicad_sch

## KiCad design Lynx 96/Kicad/lynx96_ramsignals.kicad_sch (2025-07-15)

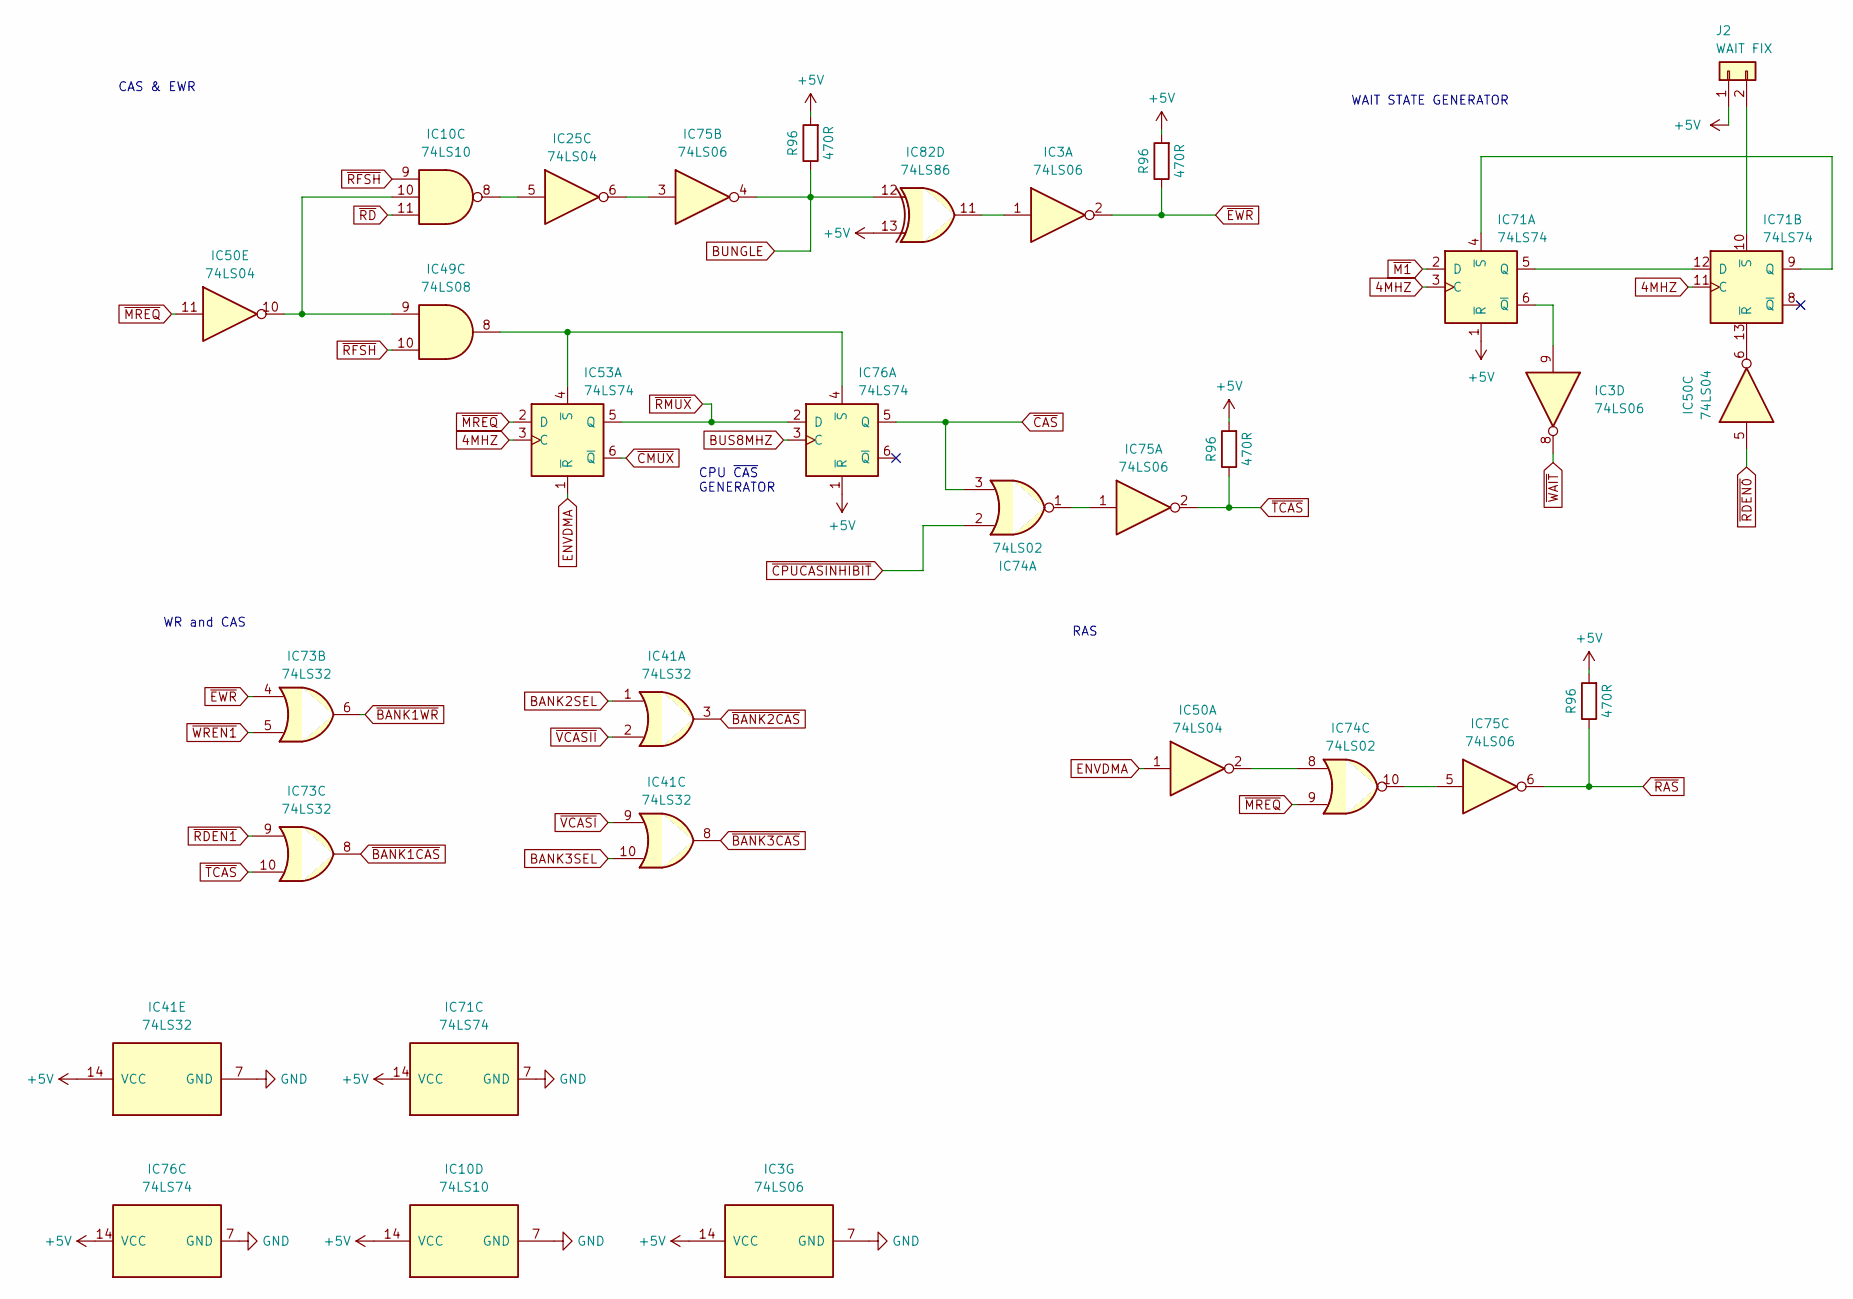
[picture p21: schematic lynx96_ramsignals.kicad_sch]

Parts:
IC3, IC75: 74LS06; DIP-14_W7.62mm
IC10: 74LS10; DIP-14_W7.62mm
IC25, IC50: 74LS04; DIP-14_W7.62mm
IC41, IC73: 74LS32; DIP-14_W7.62mm
IC49: 74LS08; DIP-14_W7.62mm
IC53, IC71, IC76: 74LS74; DIP-14_W7.62mm
IC74: 74LS02; DIP-14_W7.62mm
IC82: 74LS86; DIP-14_W7.62mm
J2: WAIT FIX; Jumper
R96: 470R; Resistor 3.81mm

Connections:
4MHZ: IC53.3 (C), IC71.3 (C), IC71.11 (C)
+5V: IC3.14 (VCC), IC10.14 (VCC), IC41.14 (VCC), IC71.1 (~R), IC71.14 (VCC), IC76.1 (~R), IC76.14 (VCC), IC82.13, J2.1, R96.2
BANK2SEL: IC41.1
BANK3SEL: IC41.10
BUNGLE: IC75.4, IC82.12, R96.1
BUS8MHZ: IC76.3 (C)
ENVDMA: IC50.1, IC53.1 (~R)
GND: IC3.7 (GND), IC10.7 (GND), IC41.7 (GND), IC71.7 (GND), IC76.7 (GND)
unnamed: IC3.1, IC82.11
unnamed: IC3.9, IC71.6 (~Q)
unnamed: IC10.8, IC25.5
unnamed: IC10.10, IC49.9, IC50.10
unnamed: IC25.6, IC75.3
unnamed: IC49.8, IC53.4 (~S), IC76.4 (~S)
unnamed: IC50.2, IC74.8
unnamed: IC50.6, IC71.13 (~R)
unnamed: IC71.4 (~S), IC71.9 (Q)
unnamed: IC71.10 (~S), J2.2
unnamed: IC71.5 (Q), IC71.12 (D)
unnamed: IC74.1, IC75.1
unnamed: IC74.10, IC75.5
~BANK1CAS: IC73.8
~BANK1WR: IC73.6
~BANK2CAS: IC41.3
~BANK3CAS: IC41.8
~CAS: IC74.3, IC76.5 (Q)
~CMUX: IC53.6 (~Q)
~CPUCASINHIBIT: IC74.2
~EWR: IC3.2, IC73.4, R96.1
~M1: IC71.2 (D)
~MREQ: IC50.11, IC53.2 (D), IC74.9
~RAS: IC75.6, R96.1
~RDEN0: IC50.5
~RDEN1: IC73.9
~RD: IC10.11
~RFSH: IC10.9, IC49.10
~RMUX: IC53.5 (Q), IC76.2 (D)
~TCAS: IC73.10, IC75.2, R96.1
~VCASII: IC41.2
~VCASI: IC41.9
~WAIT: IC3.8
~WREN1: IC73.5

Notes on the sheet:
WR and CAS
CAS & EWR
WAIT STATE GENERATOR
RAS
CPU ~{CAS} GENERATOR
