Board-Folk/Camputers-Lynx/Lynx 96/Kicad/lynx96_systemtiming.kicad_sch

## KiCad design Lynx 96/Kicad/lynx96_systemtiming.kicad_sch (2025-07-15)

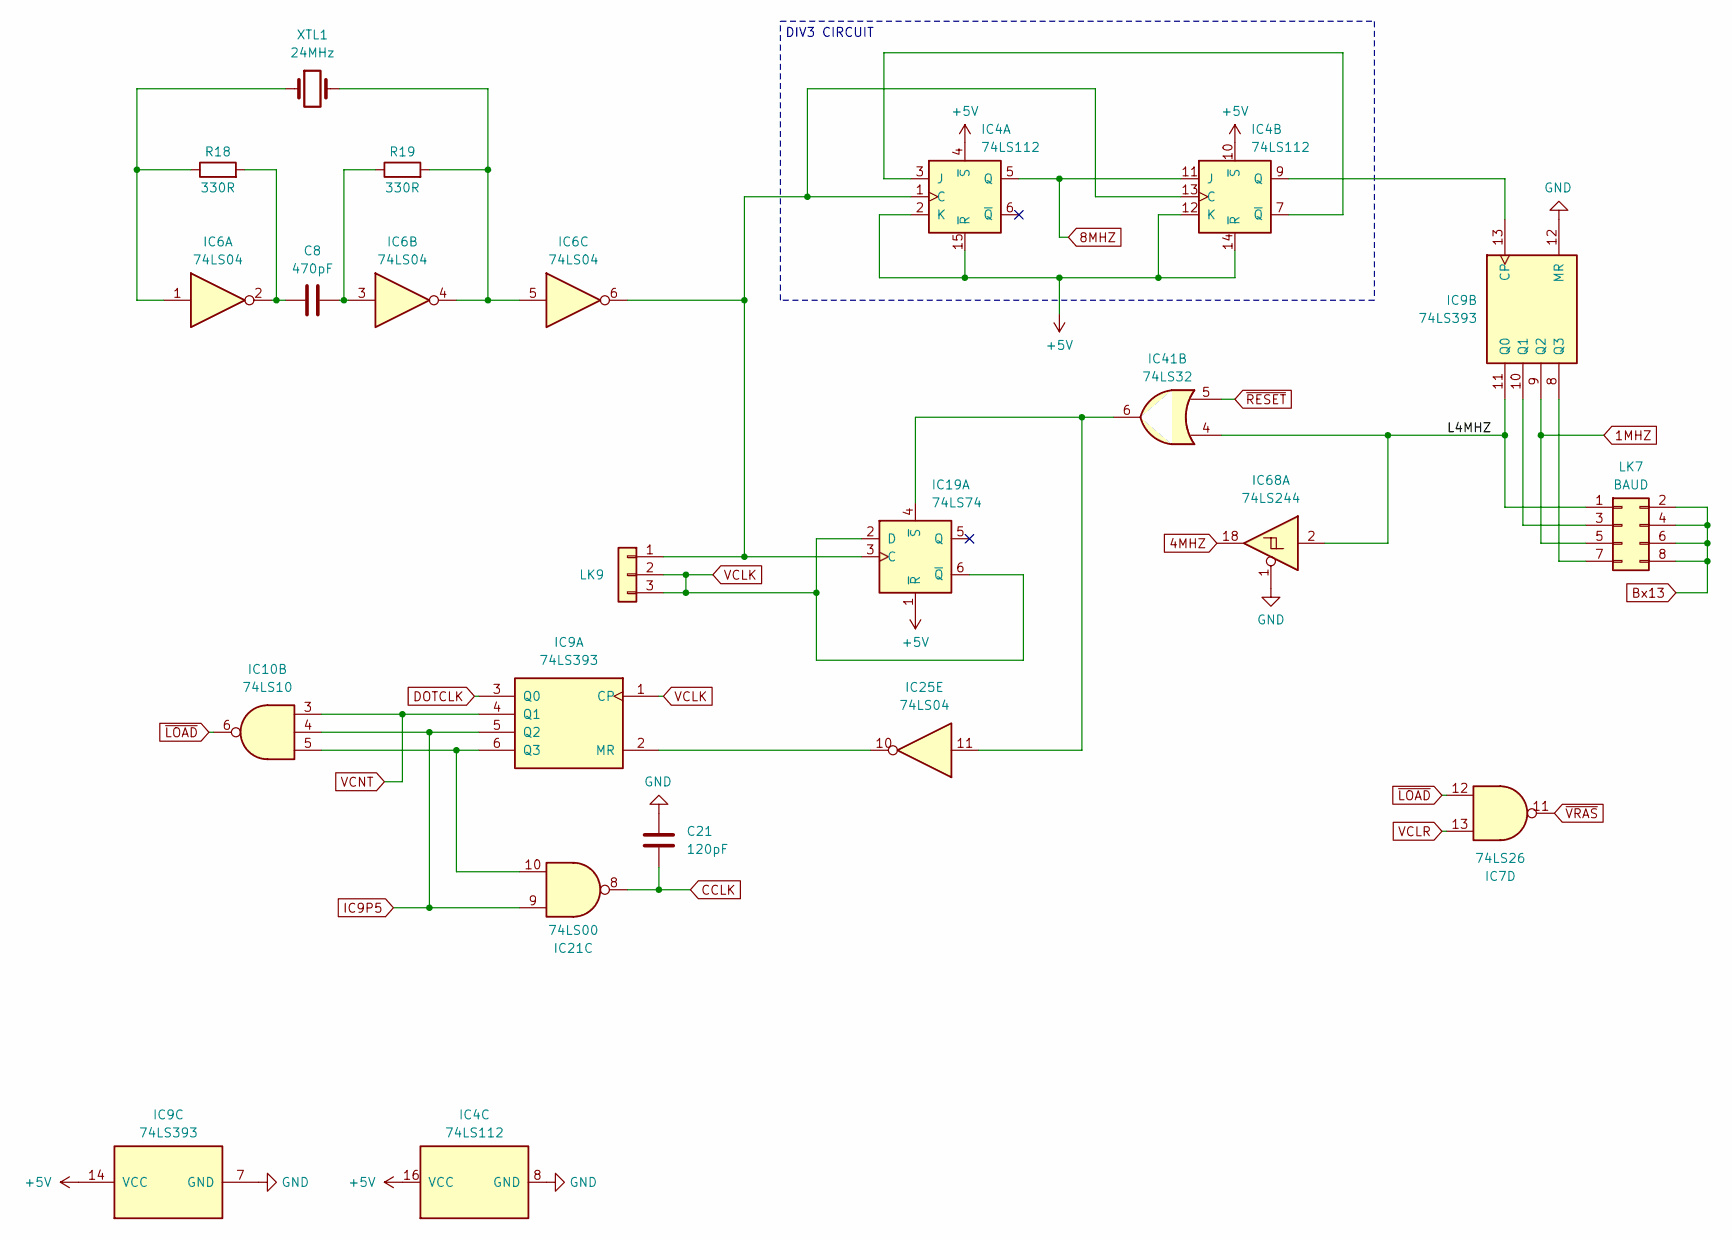
[picture p22: schematic lynx96_systemtiming.kicad_sch]

Parts:
C8: 470pF; Resistor 5.08mm
C21: 120pF; Resistor 5.08mm
IC4: 74LS112; DIP-16_W7.62mm
IC6, IC25: 74LS04; DIP-14_W7.62mm
IC7: 74LS26; DIP-14_W7.62mm
IC9: 74LS393; DIP-14_W7.62mm
IC10: 74LS10; DIP-14_W7.62mm
IC19: 74LS74; DIP-14_W7.62mm
IC21: 74LS00; DIP-14_W7.62mm
IC41: 74LS32; DIP-14_W7.62mm
IC68: 74LS244; DIP-20_W7.62mm
LK7: BAUD; LK7
LK9: -; LK 3-Pin 2.54mm - No Box
R18, R19: 330R; Resistor 2.54mm
XTL1: 24MHz; Resistor 5.08mm

Connections:
1MHZ: IC9.9 (Q2), LK7.5
4MHZ: IC68.18
8MHZ: IC4.5 (Q), IC4.11 (J)
+5V: IC4.2 (K), IC4.4 (~S), IC4.10 (~S), IC4.12 (K), IC4.14 (~R), IC4.15 (~R), IC4.16 (VCC), IC9.14 (VCC), IC19.1 (~R)
Bx13: LK7.2, LK7.4, LK7.6, LK7.8
CCLK: C21.1, IC21.8
DOTCLK: IC9.3 (Q0)
GND: C21.2, IC4.8 (GND), IC9.7 (GND), IC9.12 (MR), IC68.1
IC9P5: IC9.5 (Q2), IC10.4, IC21.9
L4MHZ: IC9.11 (Q0), IC41.4, IC68.2, LK7.1
unnamed: C8.1, IC6.2, R18.2
unnamed: C8.2, IC6.3, R19.1
unnamed: IC4.3 (J), IC4.7 (~Q)
unnamed: IC4.9 (Q), IC9.13 (CP)
unnamed: IC6.1, R18.1, XTL1.1
unnamed: IC6.4, IC6.5, R19.2, XTL1.2
unnamed: IC9.8 (Q3), LK7.7
unnamed: IC9.10 (Q1), LK7.3
unnamed: IC9.6 (Q3), IC10.5, IC21.10
unnamed: IC4.1 (C), IC4.13 (C), IC6.6, IC19.3 (C), LK9.1
unnamed: IC19.4 (~S), IC25.11, IC41.6
unnamed: IC9.2 (MR), IC25.10
VCLK: IC9.1 (CP), IC19.2 (D), IC19.6 (~Q), LK9.2, LK9.3
VCLR: IC7.13
VCNT: IC9.4 (Q1), IC10.3
~LOAD: IC7.12, IC10.6
~RESET: IC41.5
~VRAS: IC7.11

Notes on the sheet:
DIV3 CIRCUIT
