Board-Folk/Camputers-Lynx/Lynx 96/Kicad/lynx96_videotiming.kicad_sch

## KiCad design Lynx 96/Kicad/lynx96_videotiming.kicad_sch (2025-07-15)

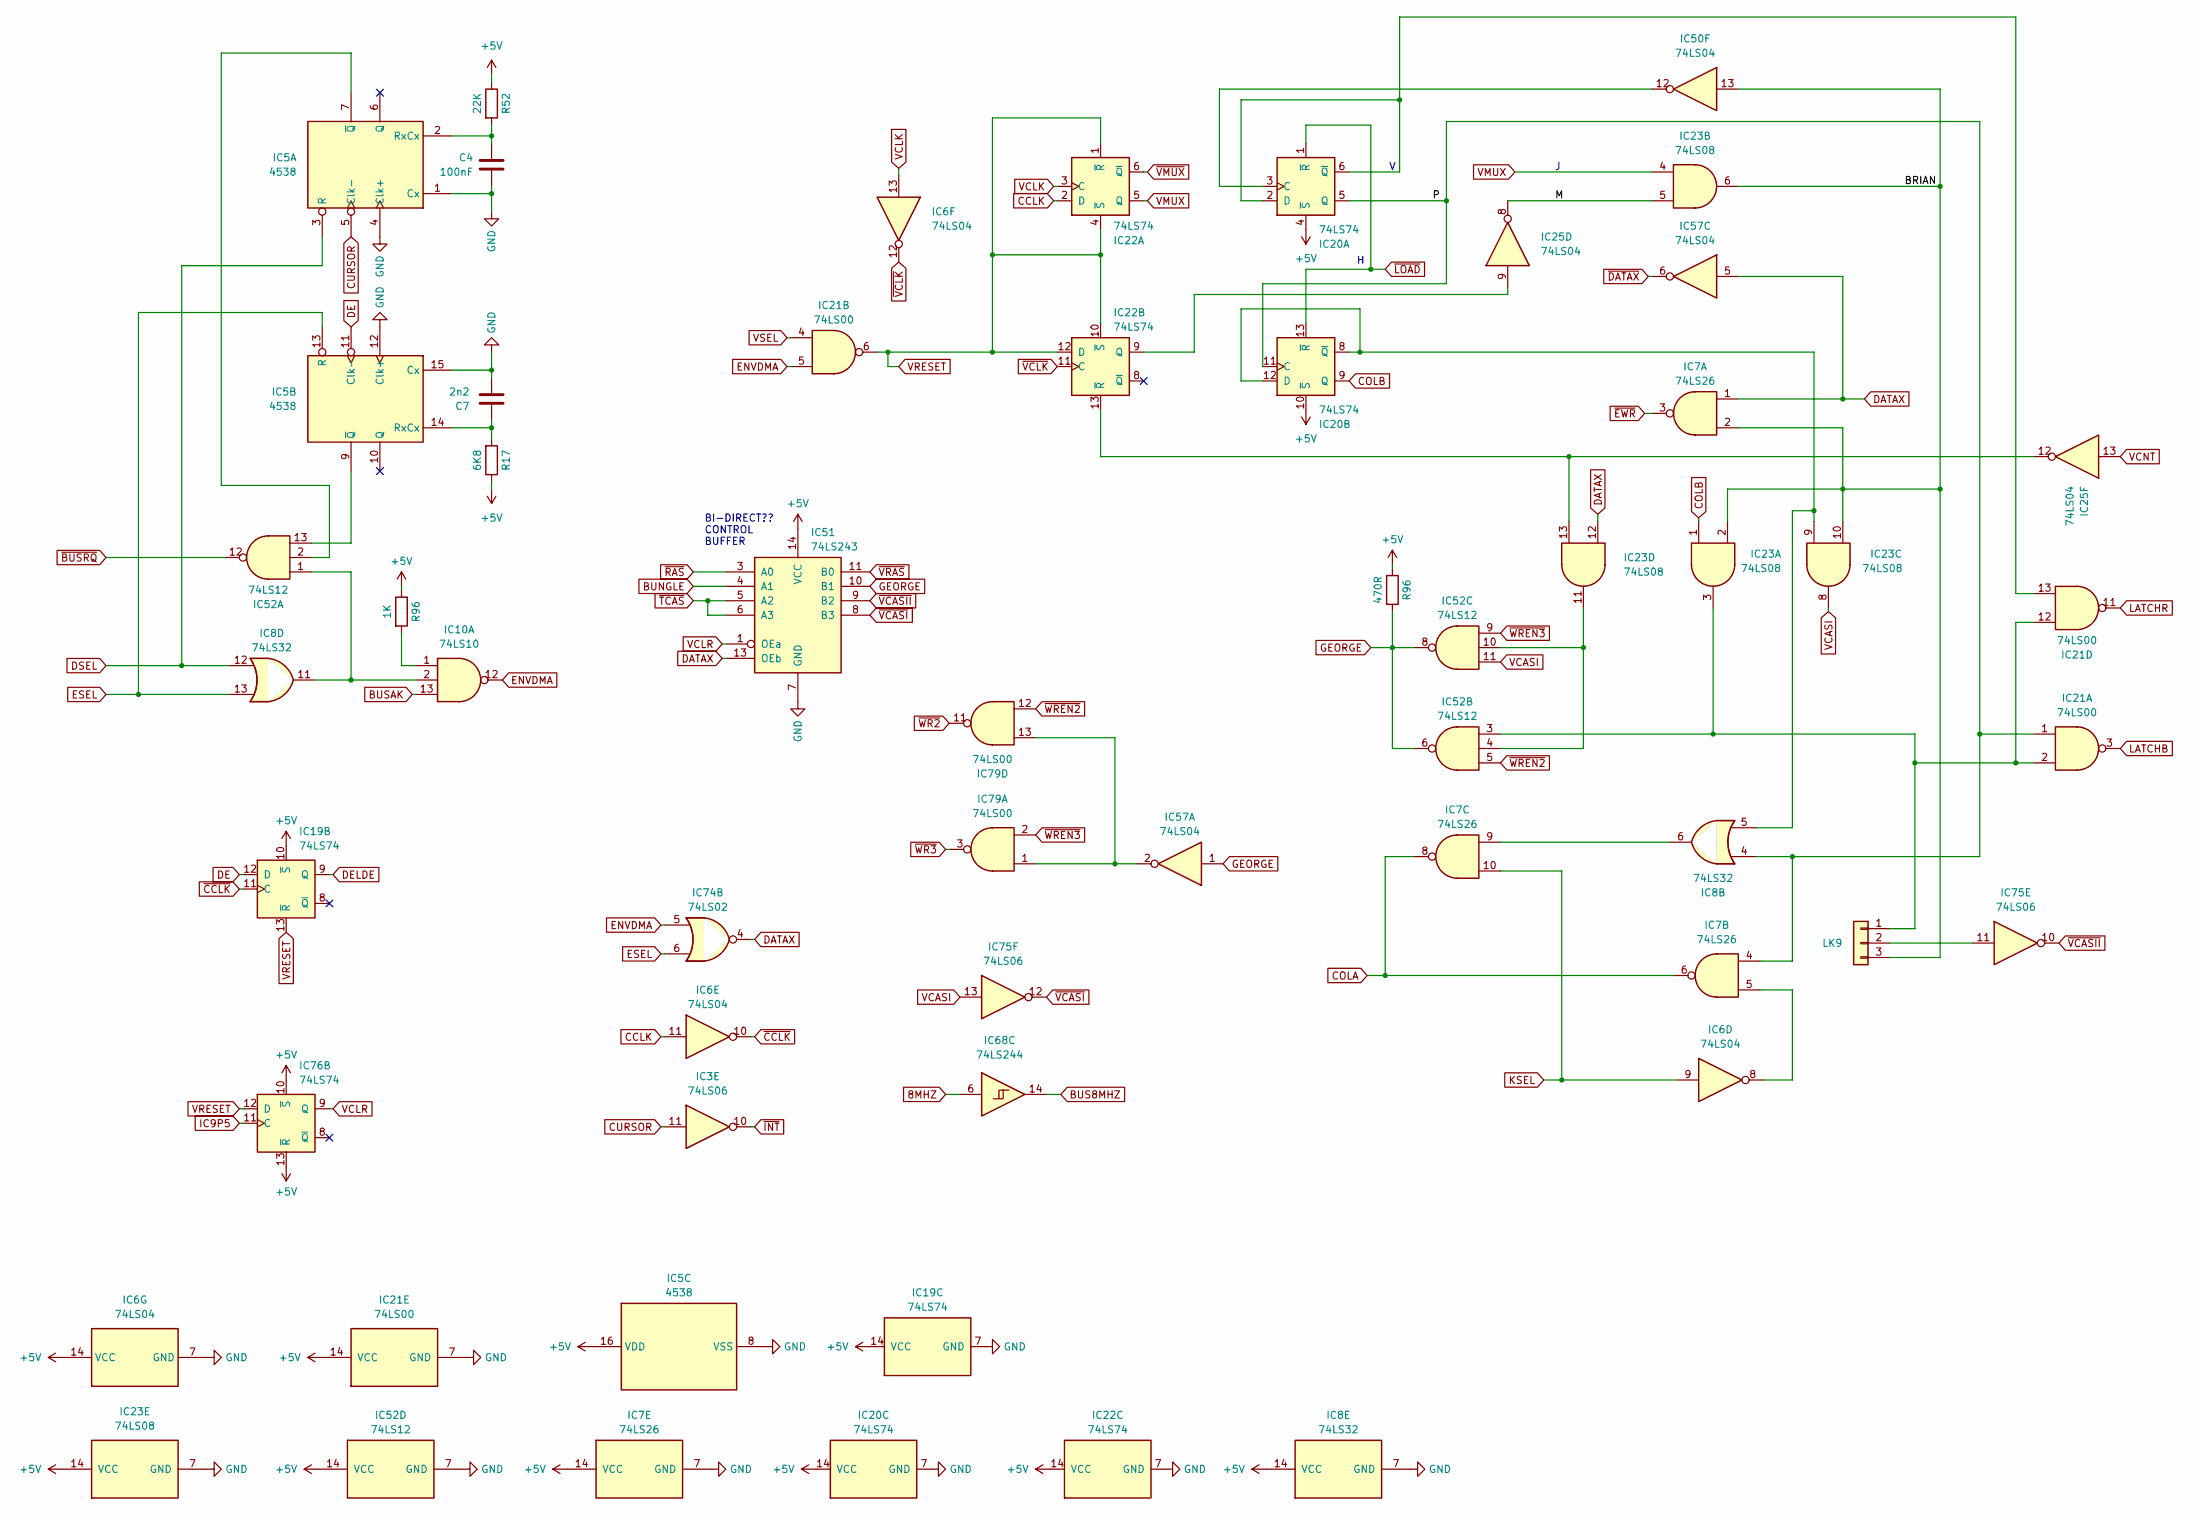
[picture p23: schematic lynx96_videotiming.kicad_sch]

Parts:
C4: 100nF; Resistor 5.08mm
C7: 2n2; Resistor 5.08mm
IC3, IC75: 74LS06; DIP-14_W7.62mm
IC5: 4538; DIP-16_W7.62mm
IC6, IC25, IC50, IC57: 74LS04; DIP-14_W7.62mm
IC7: 74LS26; DIP-14_W7.62mm
IC8: 74LS32; DIP-14_W7.62mm
IC10: 74LS10; DIP-14_W7.62mm
IC19, IC20, IC22, IC76: 74LS74; DIP-14_W7.62mm
IC21, IC79: 74LS00; DIP-14_W7.62mm
IC23: 74LS08; DIP-14_W7.62mm
IC51: 74LS243; DIP-14_W7.62mm
IC52: 74LS12; DIP-14_W7.62mm
IC68: 74LS244; DIP-20_W7.62mm
IC74: 74LS02; DIP-14_W7.62mm
LK9: -; LK 3-Pin 2.54mm - No Box
R17: 6K8; Resistor 3.81mm
R52: 22K; Resistor 3.81mm
R96: 1K; Resistor 4.20mm

Connections:
8MHZ: IC68.6
+5V: IC5.16 (VDD), IC6.14 (VCC), IC7.14 (VCC), IC8.14 (VCC), IC19.10 (~S), IC19.14 (VCC), IC20.4 (~S), IC20.10 (~S), IC20.14 (VCC), IC21.14 (VCC), IC22.14 (VCC), IC23.14 (VCC), IC51.14 (VCC), IC52.14 (VCC), IC76.10 (~S), IC76.13 (~R), R17.1, R52.1, R96.1
BRIAN: IC7.2, IC23.2, IC23.6, IC23.10, IC50.13, LK9.3
BUNGLE: IC51.4 (A1)
BUS8MHZ: IC68.14
BUSAK: IC10.13
CCLK: IC6.11, IC22.2 (D)
COLA: IC7.6, IC7.8
COLB: IC20.9 (Q), IC23.1
CURSOR: IC3.11, IC5.5 (Clk-)
DATAX: IC7.1, IC23.12, IC51.13 (OEb), IC57.5, IC74.4
DE: IC5.11 (Clk-), IC19.12 (D)
DELDE: IC19.9 (Q)
DSEL: IC5.3 (R), IC8.12
ENVDMA: IC10.12, IC21.5, IC74.5
ESEL: IC5.13 (R), IC8.13, IC74.6
GEORGE: IC51.10 (B1), IC52.6, IC52.8, IC57.1, R96.2
GND: C4.1, C7.1, IC5.1 (Cx), IC5.4 (Clk+), IC5.8 (VSS), IC5.12 (Clk+), IC5.15 (Cx), IC6.7 (GND), IC7.7 (GND), IC8.7 (GND), IC19.7 (GND), IC20.7 (GND), IC21.7 (GND), IC22.7 (GND), IC23.7 (GND), IC51.7 (GND), IC52.7 (GND)
IC9P5: IC76.11 (C)
KSEL: IC6.9, IC7.10
LATCHB: IC21.3
LATCHR: IC21.11
M: IC23.5, IC25.8
unnamed: C4.2, IC5.2 (RxCx), R52.2
unnamed: C7.2, IC5.14 (RxCx), R17.2
unnamed: IC5.7 (~Q), IC52.2
unnamed: IC5.9 (~Q), IC52.13
unnamed: IC6.8, IC7.5
unnamed: IC7.9, IC8.6
unnamed: IC10.1, R96.2
unnamed: IC8.11, IC10.2, IC52.1
unnamed: IC20.2 (D), IC20.6 (~Q), IC21.13
unnamed: IC20.3 (C), IC50.12
unnamed: IC8.5, IC20.8 (~Q), IC20.12 (D), IC23.9
unnamed: IC21.2, IC21.12, IC23.3, IC52.3, LK9.1
unnamed: IC22.9 (Q), IC25.9
unnamed: IC22.13 (~R), IC23.13, IC25.12
unnamed: IC23.11, IC52.4, IC52.10
unnamed: IC57.2, IC79.1, IC79.13
unnamed: IC75.11, LK9.2
P: IC7.4, IC8.4, IC20.5 (Q), IC20.11 (C), IC21.1
VCASI: IC23.8, IC52.11, IC75.13
VCLK: IC6.13, IC22.3 (C)
VCLR: IC51.1 (OEa), IC76.9 (Q)
VCNT: IC25.13
VMUX: IC22.5 (Q), IC23.4
VRESET: IC19.13 (~R), IC21.6, IC22.1 (~R), IC22.4 (~S), IC22.10 (~S), IC22.12 (D), IC76.12 (D)
VSEL: IC21.4
~BUSRQ: IC52.12
~CCLK: IC6.10, IC19.11 (C)
~DATAX: IC57.6
~EWR: IC7.3
~INT: IC3.10
~LOAD: IC20.1 (~R), IC20.13 (~R)
~RAS: IC51.3 (A0)
~TCAS: IC51.5 (A2), IC51.6 (A3)
~VCASII: IC51.9 (B2), IC75.10
~VCASI: IC51.8 (B3), IC75.12
~VCLK: IC6.12, IC22.11 (C)
~VMUX: IC22.6 (~Q)
~VRAS: IC51.11 (B0)
~WR2: IC79.11
~WR3: IC79.3
~WREN2: IC52.5, IC79.12
~WREN3: IC52.9, IC79.2

Notes on the sheet:
BI-DIRECT?? CONTROL BUFFER
