Board-Folk/Camputers-Lynx/Lynx 128/Kicad/lynx128.kicad_sch

## KiCad design Lynx 128/Kicad/lynx128.kicad_sch (2025-07-15)

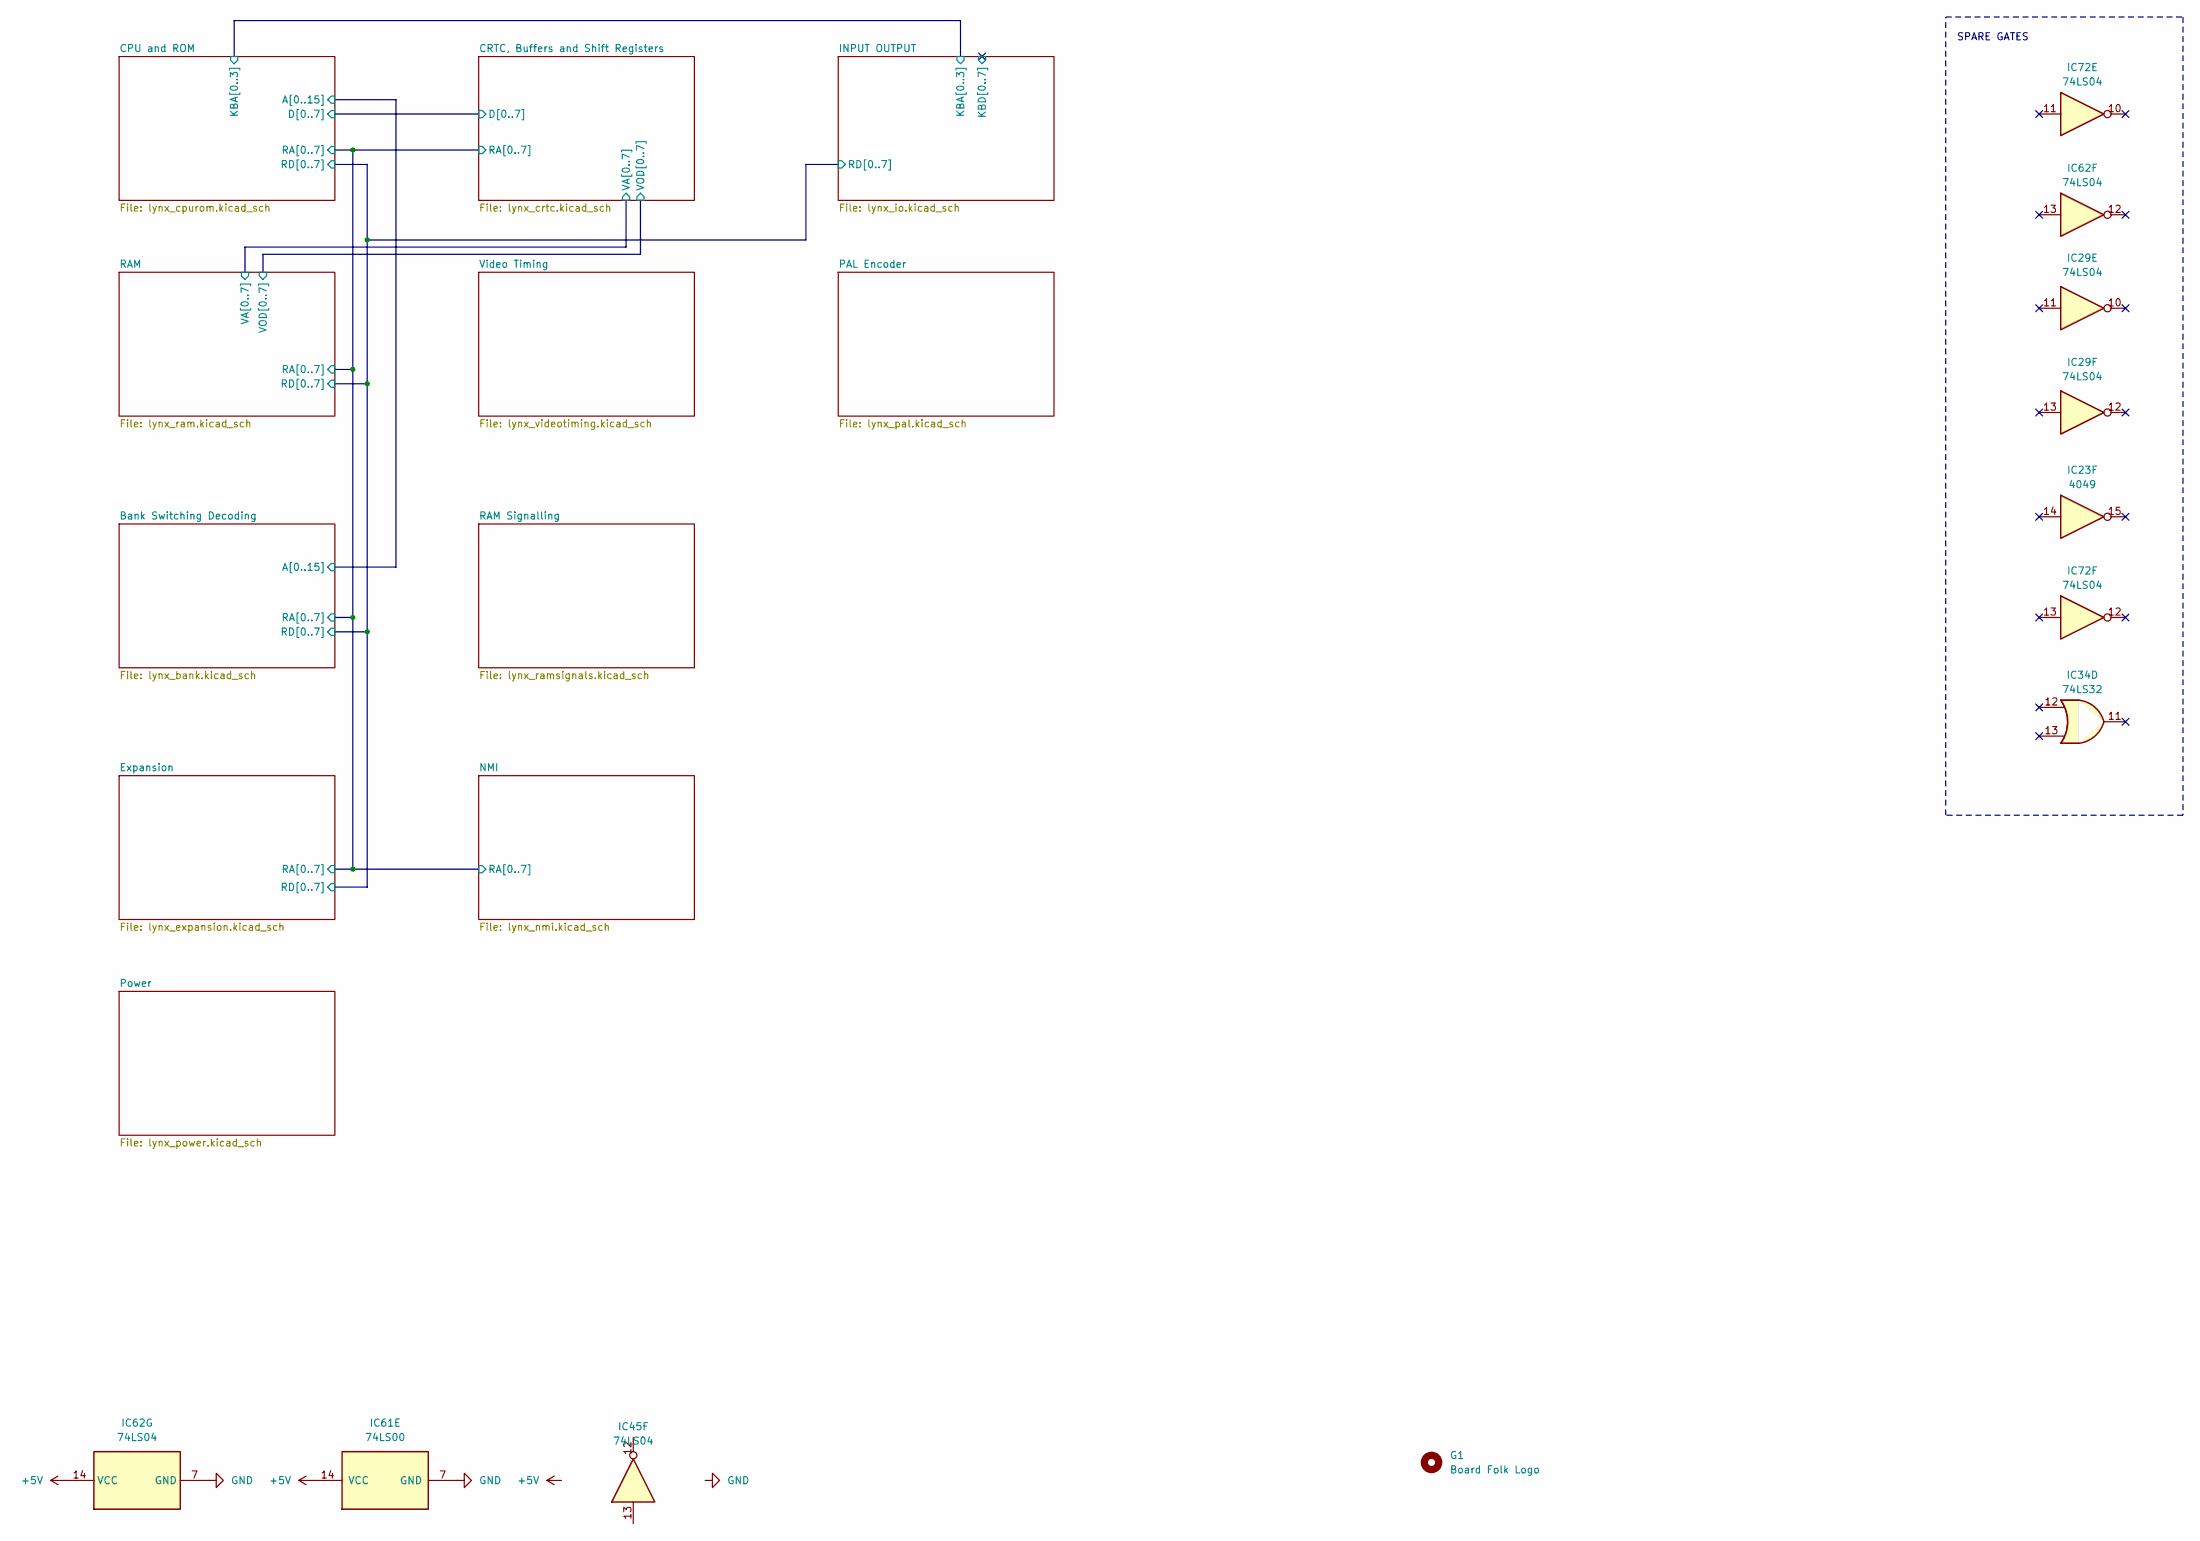
[picture p24: schematic lynx128.kicad_sch]

Parts:
G1: Board Folk Logo; BF8
IC23: 4049; DIP-16_W7.62mm
IC29, IC45, IC62, IC72: 74LS04; DIP-14_W7.62mm
IC34: 74LS32; DIP-14_W7.62mm
IC61: 74LS00; DIP-14_W7.62mm

Connections:
+5V: IC61.14 (VCC), IC62.14 (VCC)
GND: IC61.7 (GND), IC62.7 (GND)

Notes on the sheet:
SPARE GATES
