Board-Folk/Camputers-Lynx/Lynx 128/Kicad/lynx_bank.kicad_sch

## KiCad design Lynx 128/Kicad/lynx_bank.kicad_sch (2025-07-15)

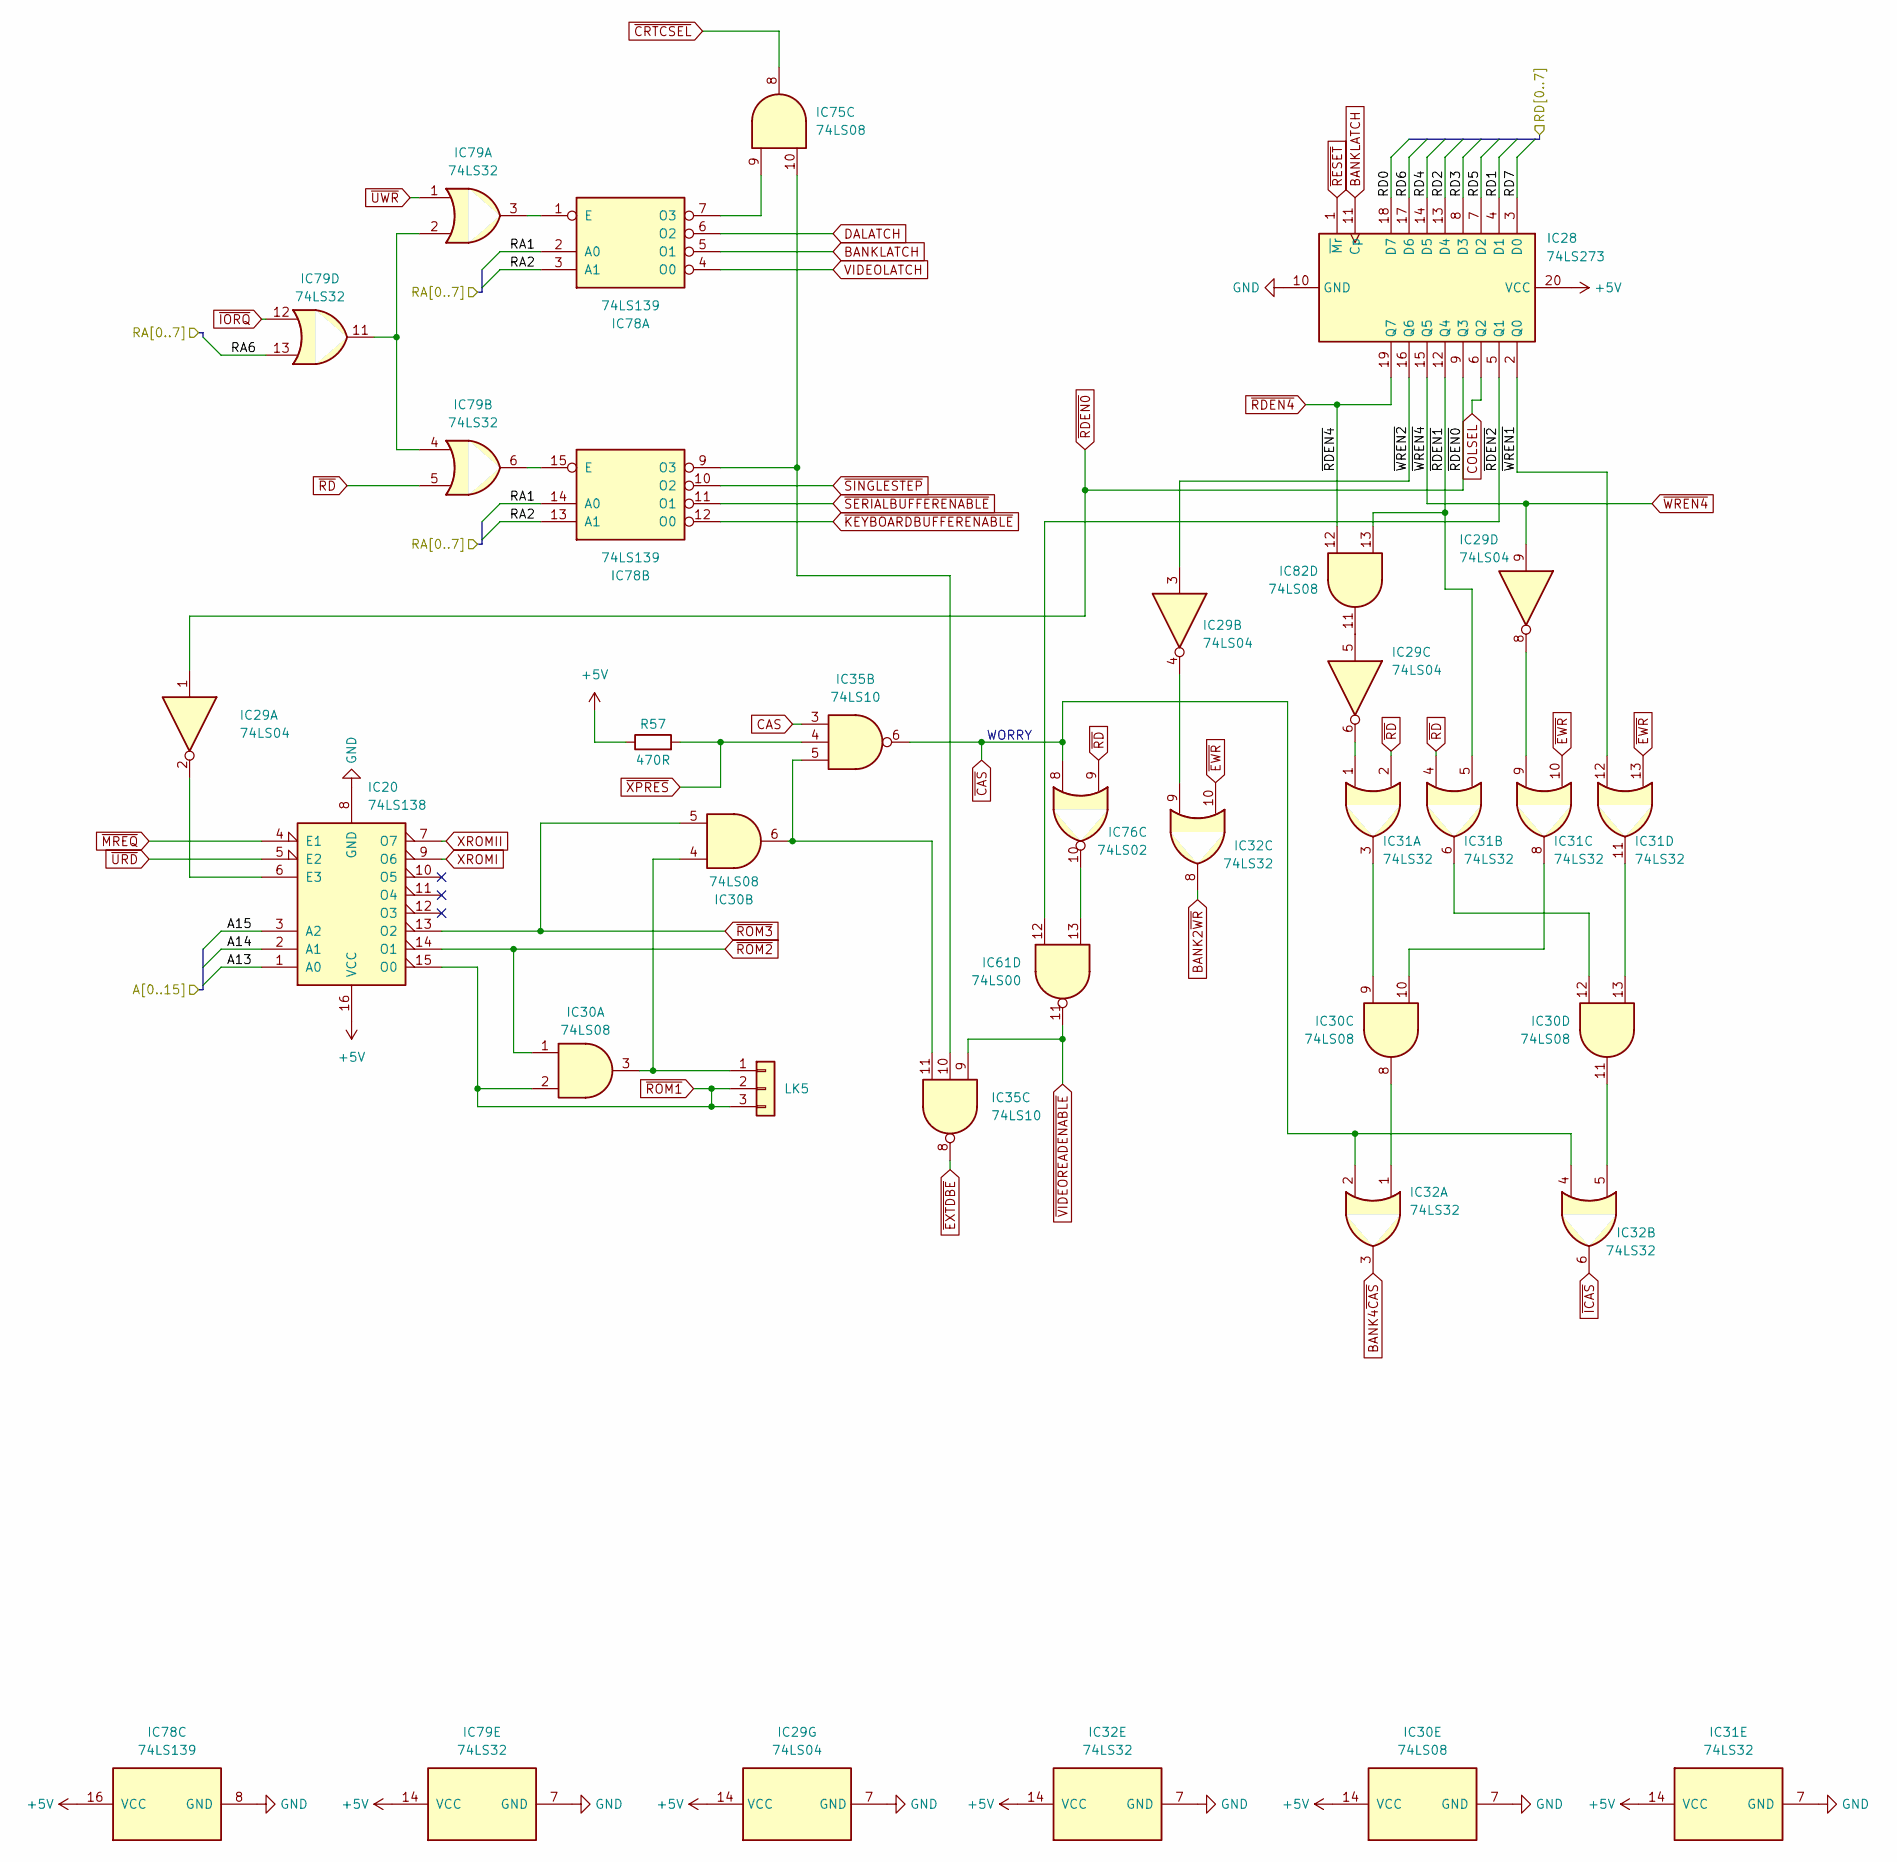
[picture p25: schematic lynx_bank.kicad_sch]

Parts:
IC20: 74LS138; DIP-16_W7.62mm
IC28: 74LS273; DIP-20_W7.62mm
IC29: 74LS04; DIP-14_W7.62mm
IC30, IC75, IC82: 74LS08; DIP-14_W7.62mm
IC31, IC32, IC79: 74LS32; DIP-14_W7.62mm
IC35: 74LS10; DIP-14_W7.62mm
IC61: 74LS00; DIP-14_W7.62mm
IC76: 74LS02; DIP-14_W7.62mm
IC78: 74LS139; DIP-16_W7.62mm
LK5: -; LK 3-Pin 2.54mm - No Box
R57: 470R; Resistor 10.16mm

Connections:
+5V: IC20.16 (VCC), IC28.20 (VCC), IC29.14 (VCC), IC30.14 (VCC), IC31.14 (VCC), IC32.14 (VCC), IC78.16 (VCC), IC79.14 (VCC), R57.1
A13: IC20.1 (A0)
A14: IC20.2 (A1)
A15: IC20.3 (A2)
BANK2~WR: IC32.8
BANK4~CAS: IC32.3
BANKLATCH: IC28.11 (Cp), IC78.5 (O1)
CAS: IC35.3
COLSEL: IC28.6 (Q2)
DALATCH: IC78.6 (O2)
GND: IC20.8 (GND), IC28.10 (GND), IC29.7 (GND), IC30.7 (GND), IC31.7 (GND), IC32.7 (GND), IC78.8 (GND), IC79.7 (GND)
unnamed: IC20.6 (E3), IC29.2
unnamed: IC29.4, IC32.9
unnamed: IC29.5, IC82.11
unnamed: IC29.6, IC31.1
unnamed: IC29.8, IC31.9
unnamed: IC30.3, IC30.4, LK5.1
unnamed: IC30.6, IC35.5, IC35.11
unnamed: IC30.8, IC32.1
unnamed: IC30.9, IC31.3
unnamed: IC30.10, IC31.8
unnamed: IC30.11, IC32.5
unnamed: IC30.12, IC31.6
unnamed: IC30.13, IC31.11
unnamed: IC35.10, IC75.10, IC78.9 (O3)
unnamed: IC61.13, IC76.10
unnamed: IC75.9, IC78.7 (O3)
unnamed: IC78.1 (E), IC79.3
unnamed: IC78.15 (E), IC79.6
unnamed: IC79.2, IC79.4, IC79.11
RA1: IC78.2 (A0), IC78.14 (A0)
RA2: IC78.3 (A1), IC78.13 (A1)
RA6: IC79.13
RD0: IC28.18 (D7)
RD1: IC28.4 (D1)
RD2: IC28.13 (D4)
RD3: IC28.8 (D3)
RD4: IC28.14 (D5)
RD5: IC28.7 (D2)
RD6: IC28.17 (D6)
RD7: IC28.3 (D0)
VIDEOLATCH: IC78.4 (O0)
XROMI: IC20.9 (O6)
XROMII: IC20.7 (O7)
~CAS: IC32.2, IC32.4, IC35.6, IC76.8
~CRTCSEL: IC75.8
~EWR: IC31.10, IC31.13, IC32.10
~EXTDBE: IC35.8
~ICAS: IC32.6
~IORQ: IC79.12
~KEYBOARDBUFFERENABLE: IC78.12 (O0)
~MREQ: IC20.4 (E1)
~RDEN0: IC28.9 (Q3), IC29.1
~RDEN1: IC28.12 (Q4), IC31.5, IC82.13
~RDEN2: IC28.5 (Q1), IC61.12
~RDEN4: IC28.19 (Q7), IC82.12
~RD: IC31.2, IC31.4, IC76.9, IC79.5
~RESET: IC28.1 (~Mr)
~ROM1: IC20.15 (O0), IC30.2, LK5.2, LK5.3
~ROM2: IC20.14 (O1), IC30.1
~ROM3: IC20.13 (O2), IC30.5
~SERIALBUFFERENABLE: IC78.11 (O1)
~SINGLESTEP: IC78.10 (O2)
~URD: IC20.5 (E2)
~UWR: IC79.1
~VIDEOREADENABLE: IC35.9, IC61.11
~WREN1: IC28.2 (Q0), IC31.12
~WREN2: IC28.16 (Q6), IC29.3
~WREN4: IC28.15 (Q5), IC29.9
~XPRES: IC35.4, R57.2

Notes on the sheet:
WORRY
