Board-Folk/Camputers-Lynx/Lynx 128/Kicad/lynx_cpurom.kicad_sch

## KiCad design Lynx 128/Kicad/lynx_cpurom.kicad_sch (2025-07-15)

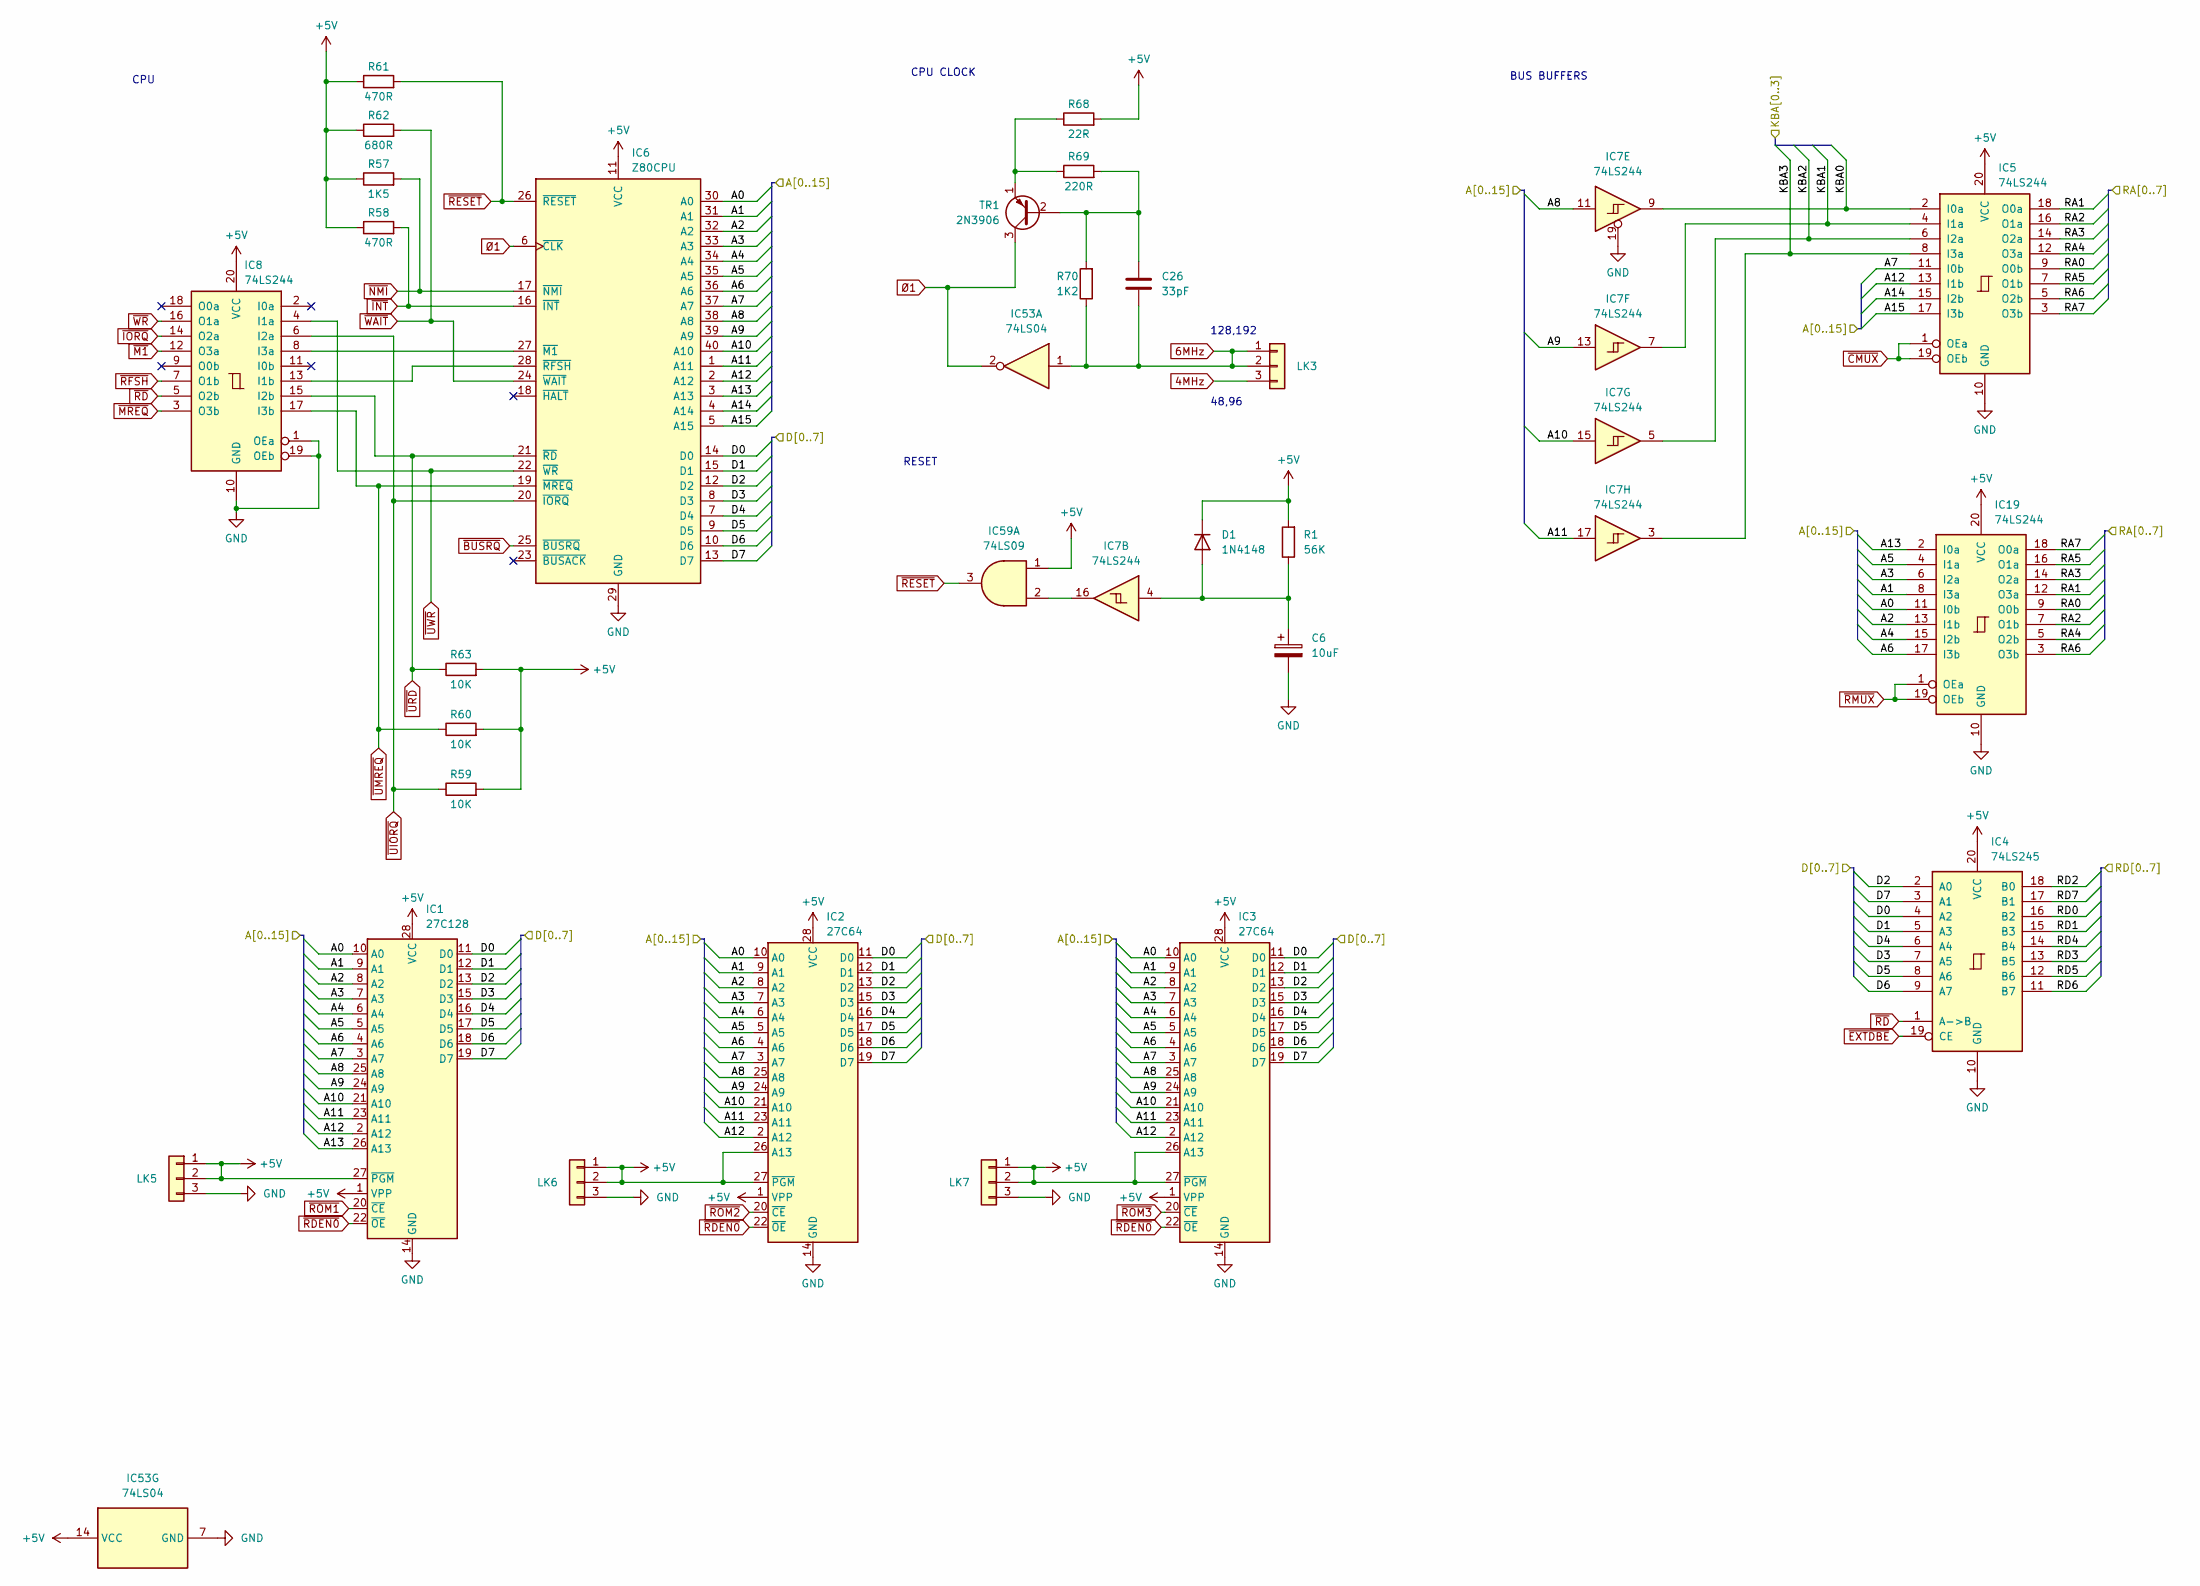
[picture p26: schematic lynx_cpurom.kicad_sch]

Parts:
C6: 10uF; Elec_5.08mm - No Box
C26: 33pF; C_Disc_5.08mm - Large Box
D1: 1N4148; Diode 7.62mm
IC1: 27C128; DIP-28_W15.24mm
IC2, IC3: 27C64; DIP-28_W15.24mm
IC4: 74LS245; DIP-20_W7.62mm
IC5, IC7, IC8, IC19: 74LS244; DIP-20_W7.62mm
IC6: Z80CPU; DIP-40_W15.24mm
IC53: 74LS04; DIP-14_W7.62mm
IC59: 74LS09; DIP-14_W7.62mm
LK3, LK5, LK6, LK7: -; LK 3-Pin 2.54mm - No Box
R1: 56K; Resistor 10.16mm
R57: 1K5; Resistor 10.16mm
R58, R61: 470R; Resistor 10.16mm
R59, R60, R63: 10K; Resistor 10.16mm
R62: 680R; Resistor 10.16mm
R68: 22R; Resistor 10.16mm
R69: 220R; Resistor 10.16mm
R70: 1K2; Resistor 10.16mm
TR1: 2N3906; Transistor - No Box

Connections:
4MHz: LK3.3
6MHz: C26.2, IC53.1, LK3.1, LK3.2, R70.1
+5V: D1.1 (K), IC1.1 (VPP), IC1.27 (~PGM), IC1.28 (VCC), IC2.1 (VPP), IC2.26 (A13), IC2.27 (~PGM), IC2.28 (VCC), IC3.1 (VPP), IC3.26 (A13), IC3.27 (~PGM), IC3.28 (VCC), IC4.20 (VCC), IC5.20 (VCC), IC6.11 (VCC), IC8.20 (VCC), IC19.20 (VCC), IC53.14 (VCC), IC59.1, LK5.1, LK5.2, LK6.1, LK6.2, LK7.1, LK7.2, R1.2, R57.1, R58.1, R59.2, R60.2, R61.1, R62.1, R63.2, R68.2
A0: IC1.10 (A0), IC2.10 (A0), IC3.10 (A0), IC6.30 (A0), IC19.11 (I0b)
A1: IC1.9 (A1), IC2.9 (A1), IC3.9 (A1), IC6.31 (A1), IC19.8 (I3a)
A2: IC1.8 (A2), IC2.8 (A2), IC3.8 (A2), IC6.32 (A2), IC19.13 (I1b)
A3: IC1.7 (A3), IC2.7 (A3), IC3.7 (A3), IC6.33 (A3), IC19.6 (I2a)
A4: IC1.6 (A4), IC2.6 (A4), IC3.6 (A4), IC6.34 (A4), IC19.15 (I2b)
A5: IC1.5 (A5), IC2.5 (A5), IC3.5 (A5), IC6.35 (A5), IC19.4 (I1a)
A6: IC1.4 (A6), IC2.4 (A6), IC3.4 (A6), IC6.36 (A6), IC19.17 (I3b)
A7: IC1.3 (A7), IC2.3 (A7), IC3.3 (A7), IC5.11 (I0b), IC6.37 (A7)
A8: IC1.25 (A8), IC2.25 (A8), IC3.25 (A8), IC6.38 (A8), IC7.11
A9: IC1.24 (A9), IC2.24 (A9), IC3.24 (A9), IC6.39 (A9), IC7.13
A10: IC1.21 (A10), IC2.21 (A10), IC3.21 (A10), IC6.40 (A10), IC7.15
A11: IC1.23 (A11), IC2.23 (A11), IC3.23 (A11), IC6.1 (A11), IC7.17
A12: IC1.2 (A12), IC2.2 (A12), IC3.2 (A12), IC5.13 (I1b), IC6.2 (A12)
A13: IC1.26 (A13), IC6.3 (A13), IC19.2 (I0a)
A14: IC5.15 (I2b), IC6.4 (A14)
A15: IC5.17 (I3b), IC6.5 (A15)
D0: IC1.11 (D0), IC2.11 (D0), IC3.11 (D0), IC4.4 (A2), IC6.14 (D0)
D1: IC1.12 (D1), IC2.12 (D1), IC3.12 (D1), IC4.5 (A3), IC6.15 (D1)
D2: IC1.13 (D2), IC2.13 (D2), IC3.13 (D2), IC4.2 (A0), IC6.12 (D2)
D3: IC1.15 (D3), IC2.15 (D3), IC3.15 (D3), IC4.7 (A5), IC6.8 (D3)
D4: IC1.16 (D4), IC2.16 (D4), IC3.16 (D4), IC4.6 (A4), IC6.7 (D4)
D5: IC1.17 (D5), IC2.17 (D5), IC3.17 (D5), IC4.8 (A6), IC6.9 (D5)
D6: IC1.18 (D6), IC2.18 (D6), IC3.18 (D6), IC4.9 (A7), IC6.10 (D6)
D7: IC1.19 (D7), IC2.19 (D7), IC3.19 (D7), IC4.3 (A1), IC6.13 (D7)
GND: C6.2, IC1.14 (GND), IC2.14 (GND), IC3.14 (GND), IC4.10 (GND), IC5.10 (GND), IC6.29 (GND), IC7.19, IC8.1 (OEa), IC8.10 (GND), IC8.19 (OEb), IC19.10 (GND), IC53.7 (GND), LK5.3, LK6.3, LK7.3
KBA0: IC5.2 (I0a), IC7.9
KBA1: IC5.4 (I1a), IC7.7
KBA2: IC5.6 (I2a), IC7.5
KBA3: IC5.8 (I3a), IC7.3
unnamed: C6.1, D1.2 (A), IC7.4, R1.1
unnamed: C26.1, R69.2, R70.2, TR1.2 (B)
unnamed: IC6.27 (~M1), IC8.8 (I3a)
unnamed: IC6.28 (~RFSH), IC8.13 (I1b)
unnamed: IC7.16, IC59.2
unnamed: R68.1, R69.1, TR1.1 (E)
RA0: IC5.9 (O0b), IC19.9 (O0b)
RA1: IC5.18 (O0a), IC19.12 (O3a)
RA2: IC5.16 (O1a), IC19.7 (O1b)
RA3: IC5.14 (O2a), IC19.14 (O2a)
RA4: IC5.12 (O3a), IC19.5 (O2b)
RA5: IC5.7 (O1b), IC19.16 (O1a)
RA6: IC5.5 (O2b), IC19.3 (O3b)
RA7: IC5.3 (O3b), IC19.18 (O0a)
RD0: IC4.16 (B2)
RD1: IC4.15 (B3)
RD2: IC4.18 (B0)
RD3: IC4.13 (B5)
RD4: IC4.14 (B4)
RD5: IC4.12 (B6)
RD6: IC4.11 (B7)
RD7: IC4.17 (B1)
~BUSRQ: IC6.25 (~BUSRQ)
~CMUX: IC5.1 (OEa), IC5.19 (OEb)
~EXTDBE: IC4.19 (CE)
~INT: IC6.16 (~INT), R58.2
~IORQ: IC8.14 (O2a)
~M1: IC8.12 (O3a)
~MREQ: IC8.3 (O3b)
~NMI: IC6.17 (~NMI), R57.2
~RDEN0: IC1.22 (~OE), IC2.22 (~OE), IC3.22 (~OE)
~RD: IC4.1 (A->B), IC8.5 (O2b)
~RESET: IC6.26 (~RESET), IC59.3, R61.2
~RFSH: IC8.7 (O1b)
~RMUX: IC19.1 (OEa), IC19.19 (OEb)
~ROM1: IC1.20 (~CE)
~ROM2: IC2.20 (~CE)
~ROM3: IC3.20 (~CE)
~UIORQ: IC6.20 (~IORQ), IC8.6 (I2a), R59.1
~UMREQ: IC6.19 (~MREQ), IC8.17 (I3b), R60.1
~URD: IC6.21 (~RD), IC8.15 (I2b), R63.1
~UWR: IC6.22 (~WR), IC8.4 (I1a)
~WAIT: IC6.24 (~WAIT), R62.2
~WR: IC8.16 (O1a)
Ø1: IC6.6 (~CLK), IC53.2, TR1.3 (C)

Notes on the sheet:
128,192
RESET
CPU
BUS BUFFERS
48,96
CPU CLOCK
