Board-Folk/Camputers-Lynx/Lynx 128/Kicad/lynx_crtc.kicad_sch

## KiCad design Lynx 128/Kicad/lynx_crtc.kicad_sch (2025-07-15)

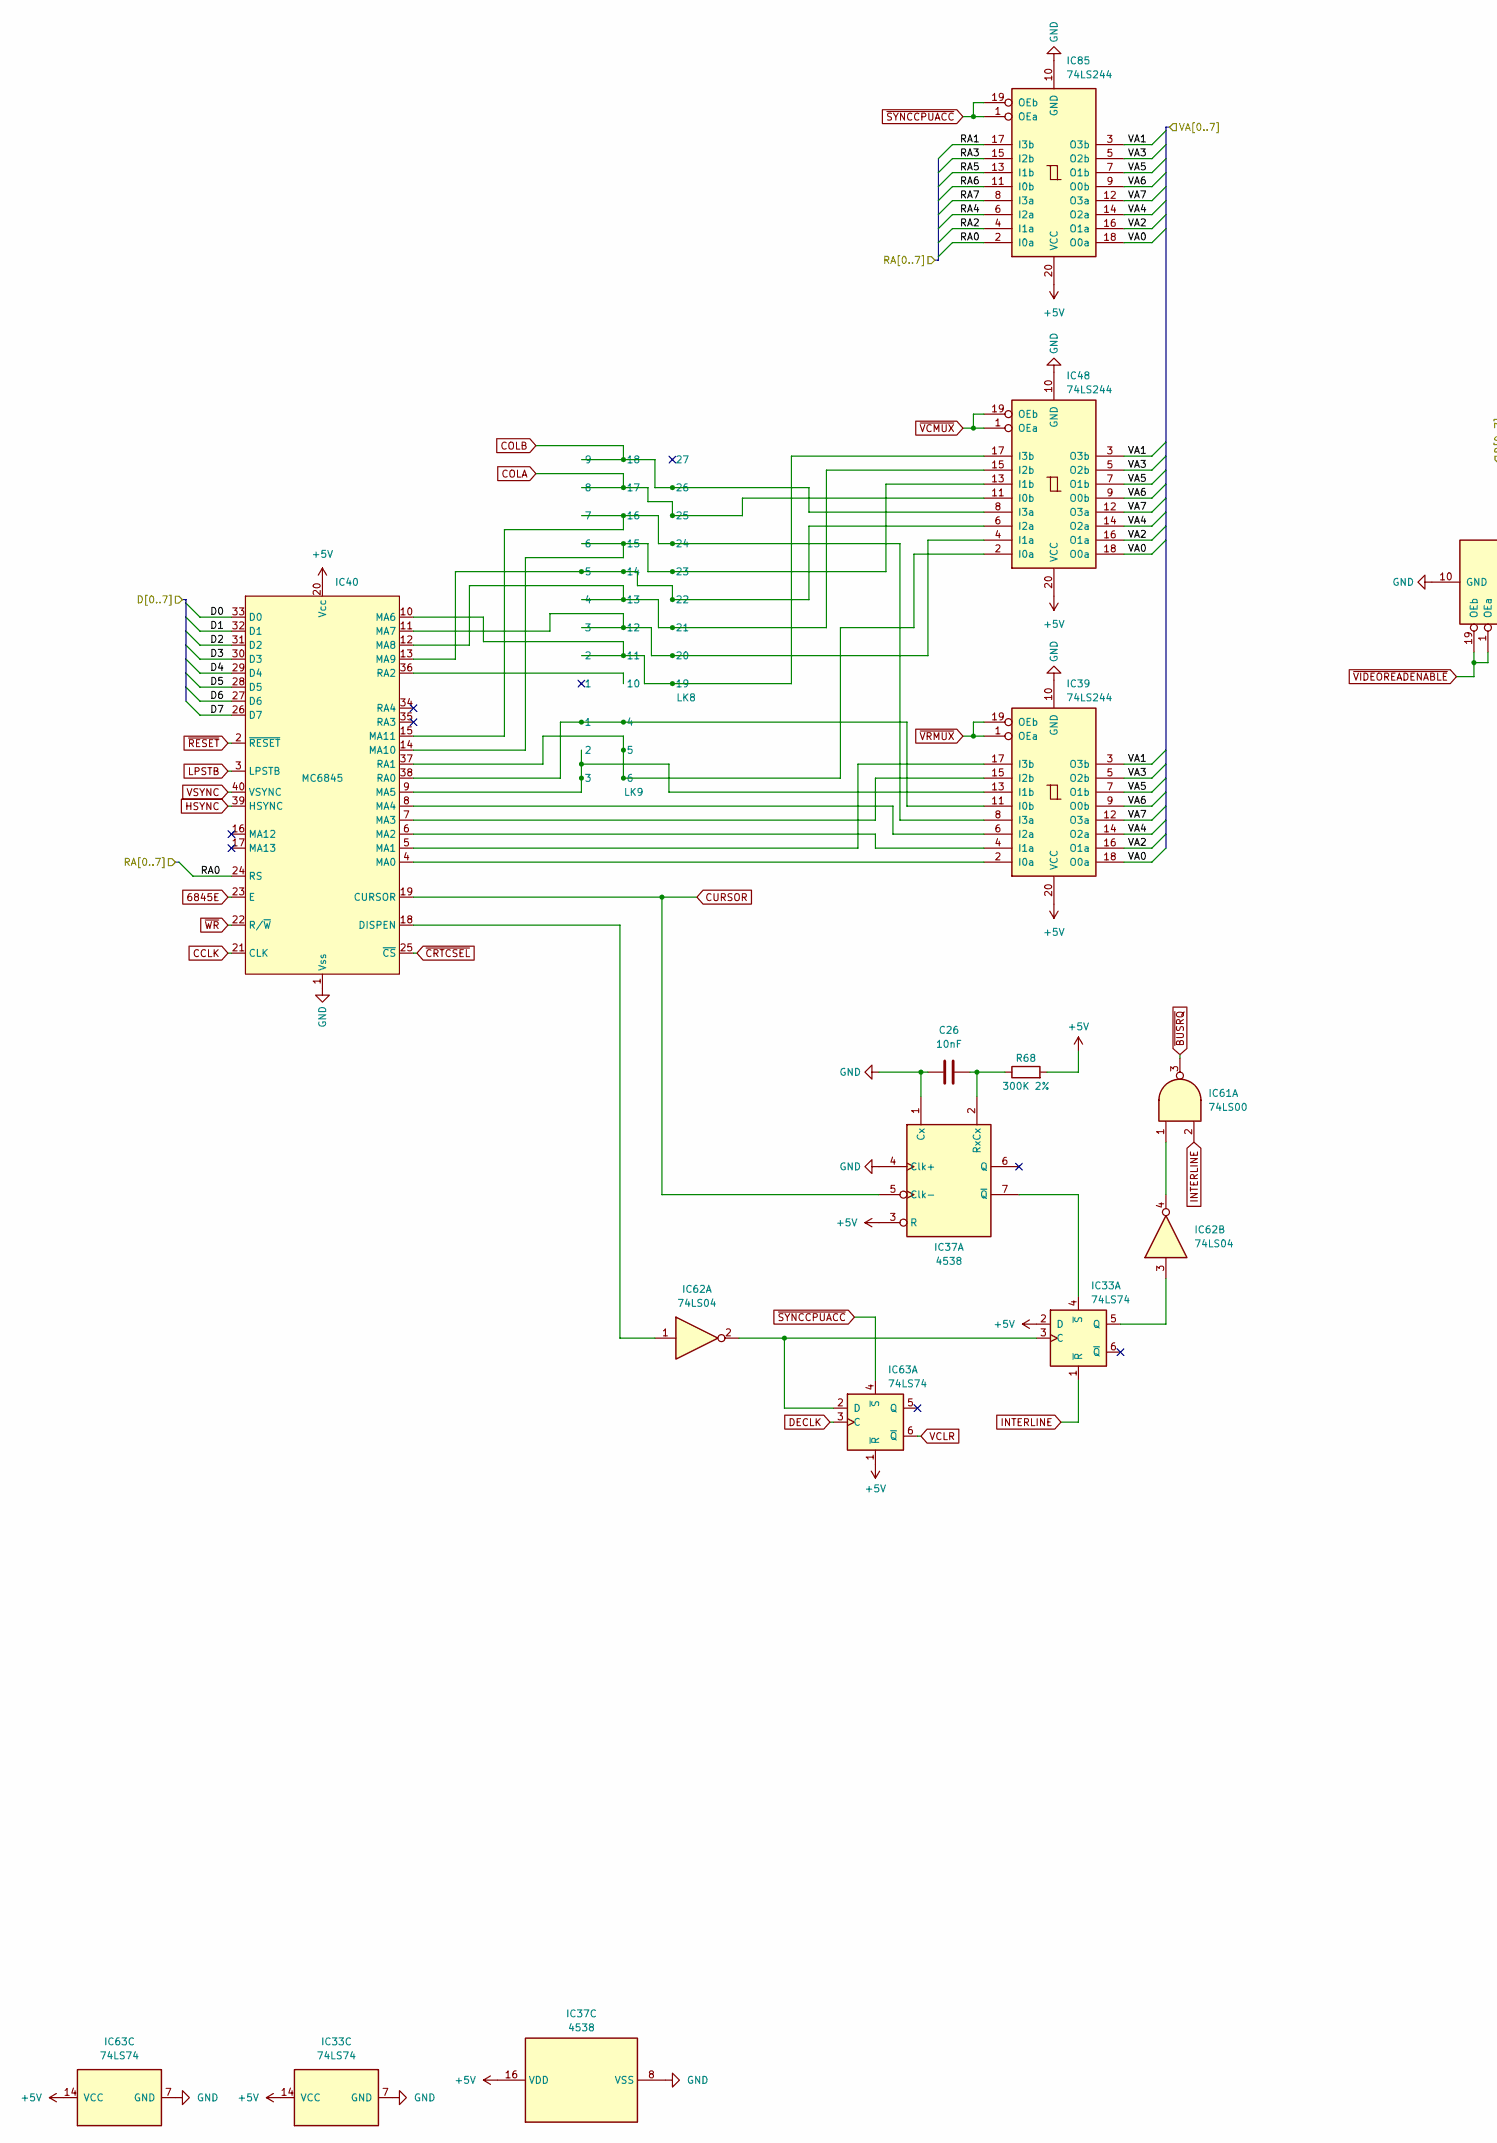
[picture p27: schematic lynx_crtc.kicad_sch, part in row 1, column 1]

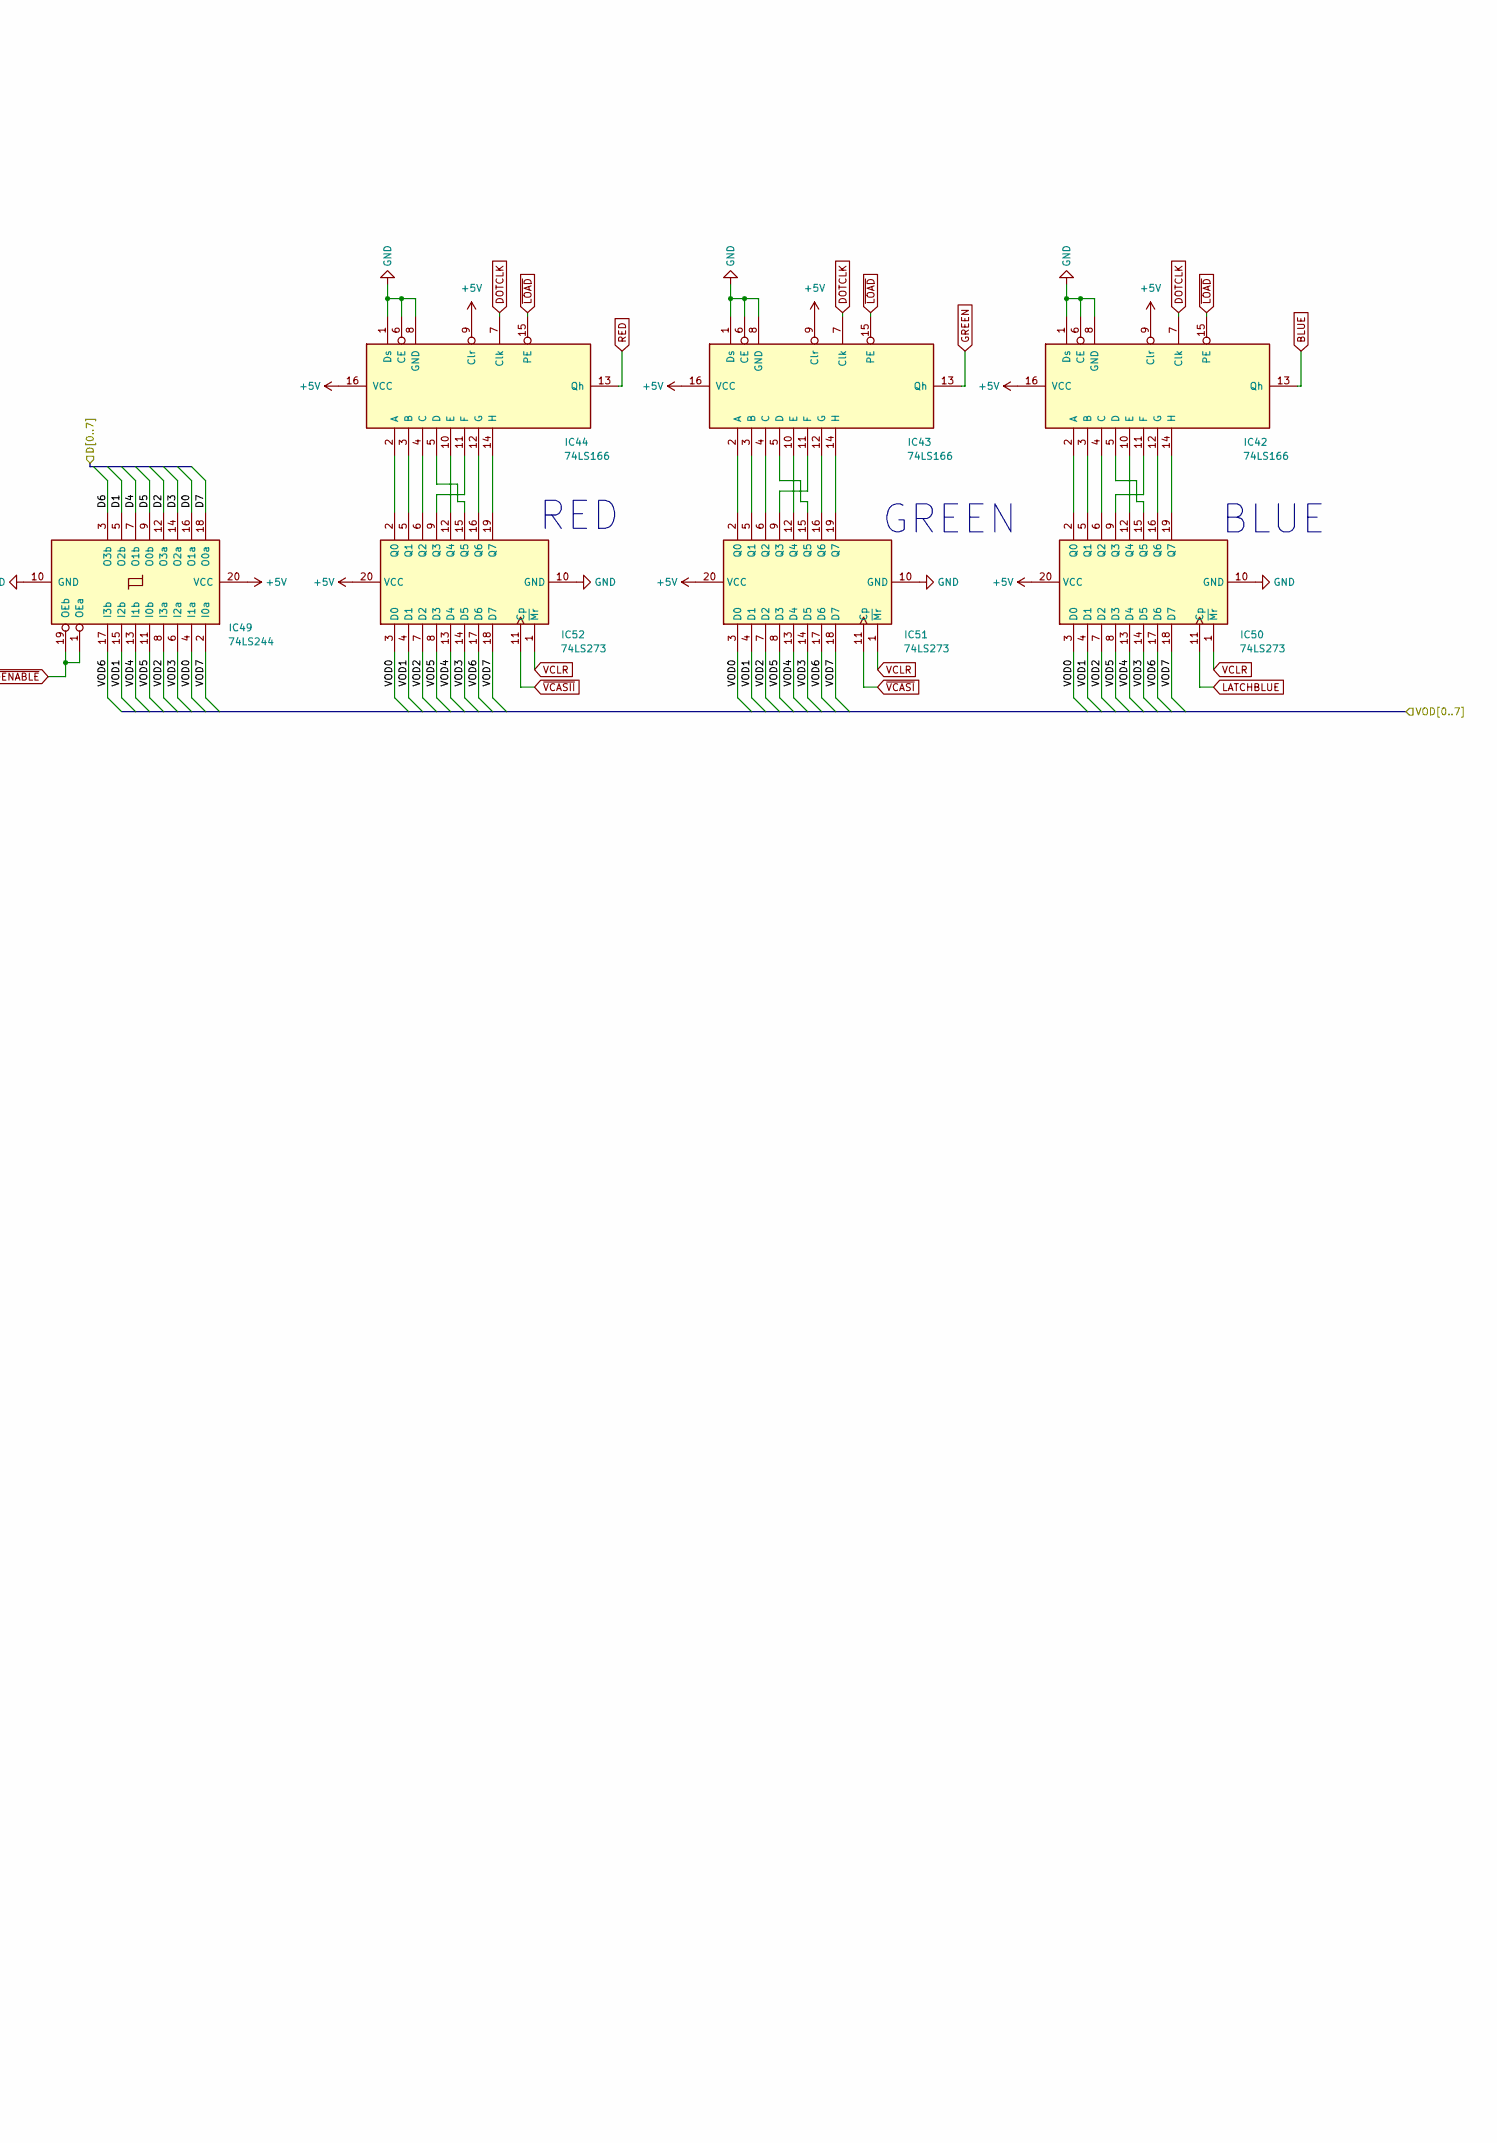
[picture p28: schematic lynx_crtc.kicad_sch, part in row 1, column 2]

Parts:
C26: 10nF; C_Disc_5.08mm - Large Box
IC33, IC63: 74LS74; DIP-14_W7.62mm
IC37: 4538; DIP-16_W7.62mm
IC39, IC48, IC49, IC85: 74LS244; DIP-20_W7.62mm
IC40: MC6845; DIP-40_W15.24mm
IC42, IC43, IC44: 74LS166; DIP-16_W7.62mm
IC50, IC51, IC52: 74LS273; DIP-20_W7.62mm
IC61: 74LS00; DIP-14_W7.62mm
IC62: 74LS04; DIP-14_W7.62mm
LK8: LK8
LK9: LK9
R68: 300K 2%; Resistor 10.16mm

Connections:
6845E: IC40.23 (E)
+5V: IC33.2 (D), IC33.14 (VCC), IC37.3 (R), IC37.16 (VDD), IC39.20 (VCC), IC40.20 (Vcc), IC42.9 (Clr), IC42.16 (VCC), IC43.9 (Clr), IC43.16 (VCC), IC44.9 (Clr), IC44.16 (VCC), IC48.20 (VCC), IC49.20 (VCC), IC50.20 (VCC), IC51.20 (VCC), IC52.20 (VCC), IC63.1 (~R), IC63.14 (VCC), IC85.20 (VCC), R68.2
BLUE: IC42.13 (Qh)
CCLK: IC40.21 (CLK)
COLA: IC48.11 (I0b), LK8.8, LK8.17, LK8.25
COLB: IC48.8 (I3a), LK8.9, LK8.18, LK8.26
CURSOR: IC37.5 (Clk-), IC40.19 (CURSOR)
D0: IC40.33 (D0), IC49.16 (O1a)
D1: IC40.32 (D1), IC49.5 (O2b)
D2: IC40.31 (D2), IC49.12 (O3a)
D3: IC40.30 (D3), IC49.14 (O2a)
D4: IC40.29 (D4), IC49.7 (O1b)
D5: IC40.28 (D5), IC49.9 (O0b)
D6: IC40.27 (D6), IC49.3 (O3b)
D7: IC40.26 (D7), IC49.18 (O0a)
DECLK: IC63.3 (C)
DOTCLK: IC42.7 (Clk), IC43.7 (Clk), IC44.7 (Clk)
GND: C26.1, IC33.7 (GND), IC37.1 (Cx), IC37.4 (Clk+), IC37.8 (VSS), IC39.10 (GND), IC40.1 (Vss), IC42.1 (Ds), IC42.6 (CE), IC42.8 (GND), IC43.1 (Ds), IC43.6 (CE), IC43.8 (GND), IC44.1 (Ds), IC44.6 (CE), IC44.8 (GND), IC48.10 (GND), IC49.10 (GND), IC50.10 (GND), IC51.10 (GND), IC52.10 (GND), IC63.7 (GND), IC85.10 (GND)
GREEN: IC43.13 (Qh)
HSYNC: IC40.39 (HSYNC)
INTERLINE: IC33.1 (~R), IC61.2
LATCHBLUE: IC50.11 (Cp)
LPSTB: IC40.3 (LPSTB)
unnamed: C26.2, IC37.2 (RxCx), R68.1
unnamed: IC33.3 (C), IC62.2, IC63.2 (D)
unnamed: IC33.4 (~S), IC37.7 (~Q)
unnamed: IC33.5 (Q), IC62.3
unnamed: IC39.2 (I0a), IC40.4 (MA0)
unnamed: IC39.4 (I1a), IC40.6 (MA2)
unnamed: IC39.6 (I2a), IC40.8 (MA4)
unnamed: IC39.8 (I3a), IC40.15 (MA11), LK8.7, LK8.16, LK8.24
unnamed: IC39.11 (I0b), IC40.38 (RA0), LK9.1, LK9.4
unnamed: IC39.13 (I1b), IC40.9 (MA5), LK9.2, LK9.3
unnamed: IC39.15 (I2b), IC40.7 (MA3)
unnamed: IC39.17 (I3b), IC40.5 (MA1)
unnamed: IC40.10 (MA6), IC48.17 (I3b), LK8.2, LK8.11, LK8.19
unnamed: IC40.11 (MA7), IC48.4 (I1a), LK8.3, LK8.12, LK8.20
unnamed: IC40.12 (MA8), IC48.15 (I2b), LK8.4, LK8.13, LK8.21
unnamed: IC40.13 (MA9), IC48.6 (I2a), LK8.5, LK8.14, LK8.22
unnamed: IC40.14 (MA10), IC48.13 (I1b), LK8.6, LK8.15, LK8.23
unnamed: IC40.18 (DISPEN), IC62.1
unnamed: IC40.36 (RA2), LK8.10
unnamed: IC40.37 (RA1), IC48.2 (I0a), LK9.5, LK9.6
unnamed: IC42.2 (A), IC50.2 (Q0)
unnamed: IC42.3 (B), IC50.5 (Q1)
unnamed: IC42.4 (C), IC50.6 (Q2)
unnamed: IC42.5 (D), IC50.15 (Q5)
unnamed: IC42.10 (E), IC50.12 (Q4)
unnamed: IC42.11 (F), IC50.9 (Q3)
unnamed: IC42.12 (G), IC50.16 (Q6)
unnamed: IC42.14 (H), IC50.19 (Q7)
unnamed: IC43.2 (A), IC51.2 (Q0)
unnamed: IC43.3 (B), IC51.5 (Q1)
unnamed: IC43.4 (C), IC51.6 (Q2)
unnamed: IC43.5 (D), IC51.15 (Q5)
unnamed: IC43.10 (E), IC51.12 (Q4)
unnamed: IC43.11 (F), IC51.9 (Q3)
unnamed: IC43.12 (G), IC51.16 (Q6)
unnamed: IC43.14 (H), IC51.19 (Q7)
unnamed: IC44.2 (A), IC52.2 (Q0)
unnamed: IC44.3 (B), IC52.5 (Q1)
unnamed: IC44.4 (C), IC52.6 (Q2)
unnamed: IC44.5 (D), IC52.15 (Q5)
unnamed: IC44.10 (E), IC52.12 (Q4)
unnamed: IC44.11 (F), IC52.9 (Q3)
unnamed: IC44.12 (G), IC52.16 (Q6)
unnamed: IC44.14 (H), IC52.19 (Q7)
unnamed: IC61.1, IC62.4
RA0: IC40.24 (RS), IC85.2 (I0a)
RA1: IC85.17 (I3b)
RA2: IC85.4 (I1a)
RA3: IC85.15 (I2b)
RA4: IC85.6 (I2a)
RA5: IC85.13 (I1b)
RA6: IC85.11 (I0b)
RA7: IC85.8 (I3a)
RED: IC44.13 (Qh)
VA0: IC39.18 (O0a), IC48.18 (O0a), IC85.18 (O0a)
VA1: IC39.3 (O3b), IC48.3 (O3b), IC85.3 (O3b)
VA2: IC39.16 (O1a), IC48.16 (O1a), IC85.16 (O1a)
VA3: IC39.5 (O2b), IC48.5 (O2b), IC85.5 (O2b)
VA4: IC39.14 (O2a), IC48.14 (O2a), IC85.14 (O2a)
VA5: IC39.7 (O1b), IC48.7 (O1b), IC85.7 (O1b)
VA6: IC39.9 (O0b), IC48.9 (O0b), IC85.9 (O0b)
VA7: IC39.12 (O3a), IC48.12 (O3a), IC85.12 (O3a)
VCLR: IC50.1 (~Mr), IC51.1 (~Mr), IC52.1 (~Mr), IC63.6 (~Q)
VOD0: IC49.4 (I1a), IC50.3 (D0), IC51.3 (D0), IC52.3 (D0)
VOD1: IC49.15 (I2b), IC50.4 (D1), IC51.4 (D1), IC52.4 (D1)
VOD2: IC49.8 (I3a), IC50.7 (D2), IC51.7 (D2), IC52.7 (D2)
VOD3: IC49.6 (I2a), IC50.14 (D5), IC51.14 (D5), IC52.14 (D5)
VOD4: IC49.13 (I1b), IC50.13 (D4), IC51.13 (D4), IC52.13 (D4)
VOD5: IC49.11 (I0b), IC50.8 (D3), IC51.8 (D3), IC52.8 (D3)
VOD6: IC49.17 (I3b), IC50.17 (D6), IC51.17 (D6), IC52.17 (D6)
VOD7: IC49.2 (I0a), IC50.18 (D7), IC51.18 (D7), IC52.18 (D7)
VSYNC: IC40.40 (VSYNC)
~BUSRQ: IC61.3
~CRTCSEL: IC40.25 (~CS)
~LOAD: IC42.15 (PE), IC43.15 (PE), IC44.15 (PE)
~RESET: IC40.2 (~RESET)
~SYNCCPUACC: IC63.4 (~S), IC85.1 (OEa), IC85.19 (OEb)
~VCASII: IC52.11 (Cp)
~VCASI: IC51.11 (Cp)
~VCMUX: IC48.1 (OEa), IC48.19 (OEb)
~VIDEOREADENABLE: IC49.1 (OEa), IC49.19 (OEb)
~VRMUX: IC39.1 (OEa), IC39.19 (OEb)
~WR: IC40.22 (R/~W)

Notes on the sheet:
BLUE
GREEN
RED
