Board-Folk/Camputers-Lynx/Lynx 128/Kicad/lynx_io.kicad_sch

## KiCad design Lynx 128/Kicad/lynx_io.kicad_sch (2025-07-15)

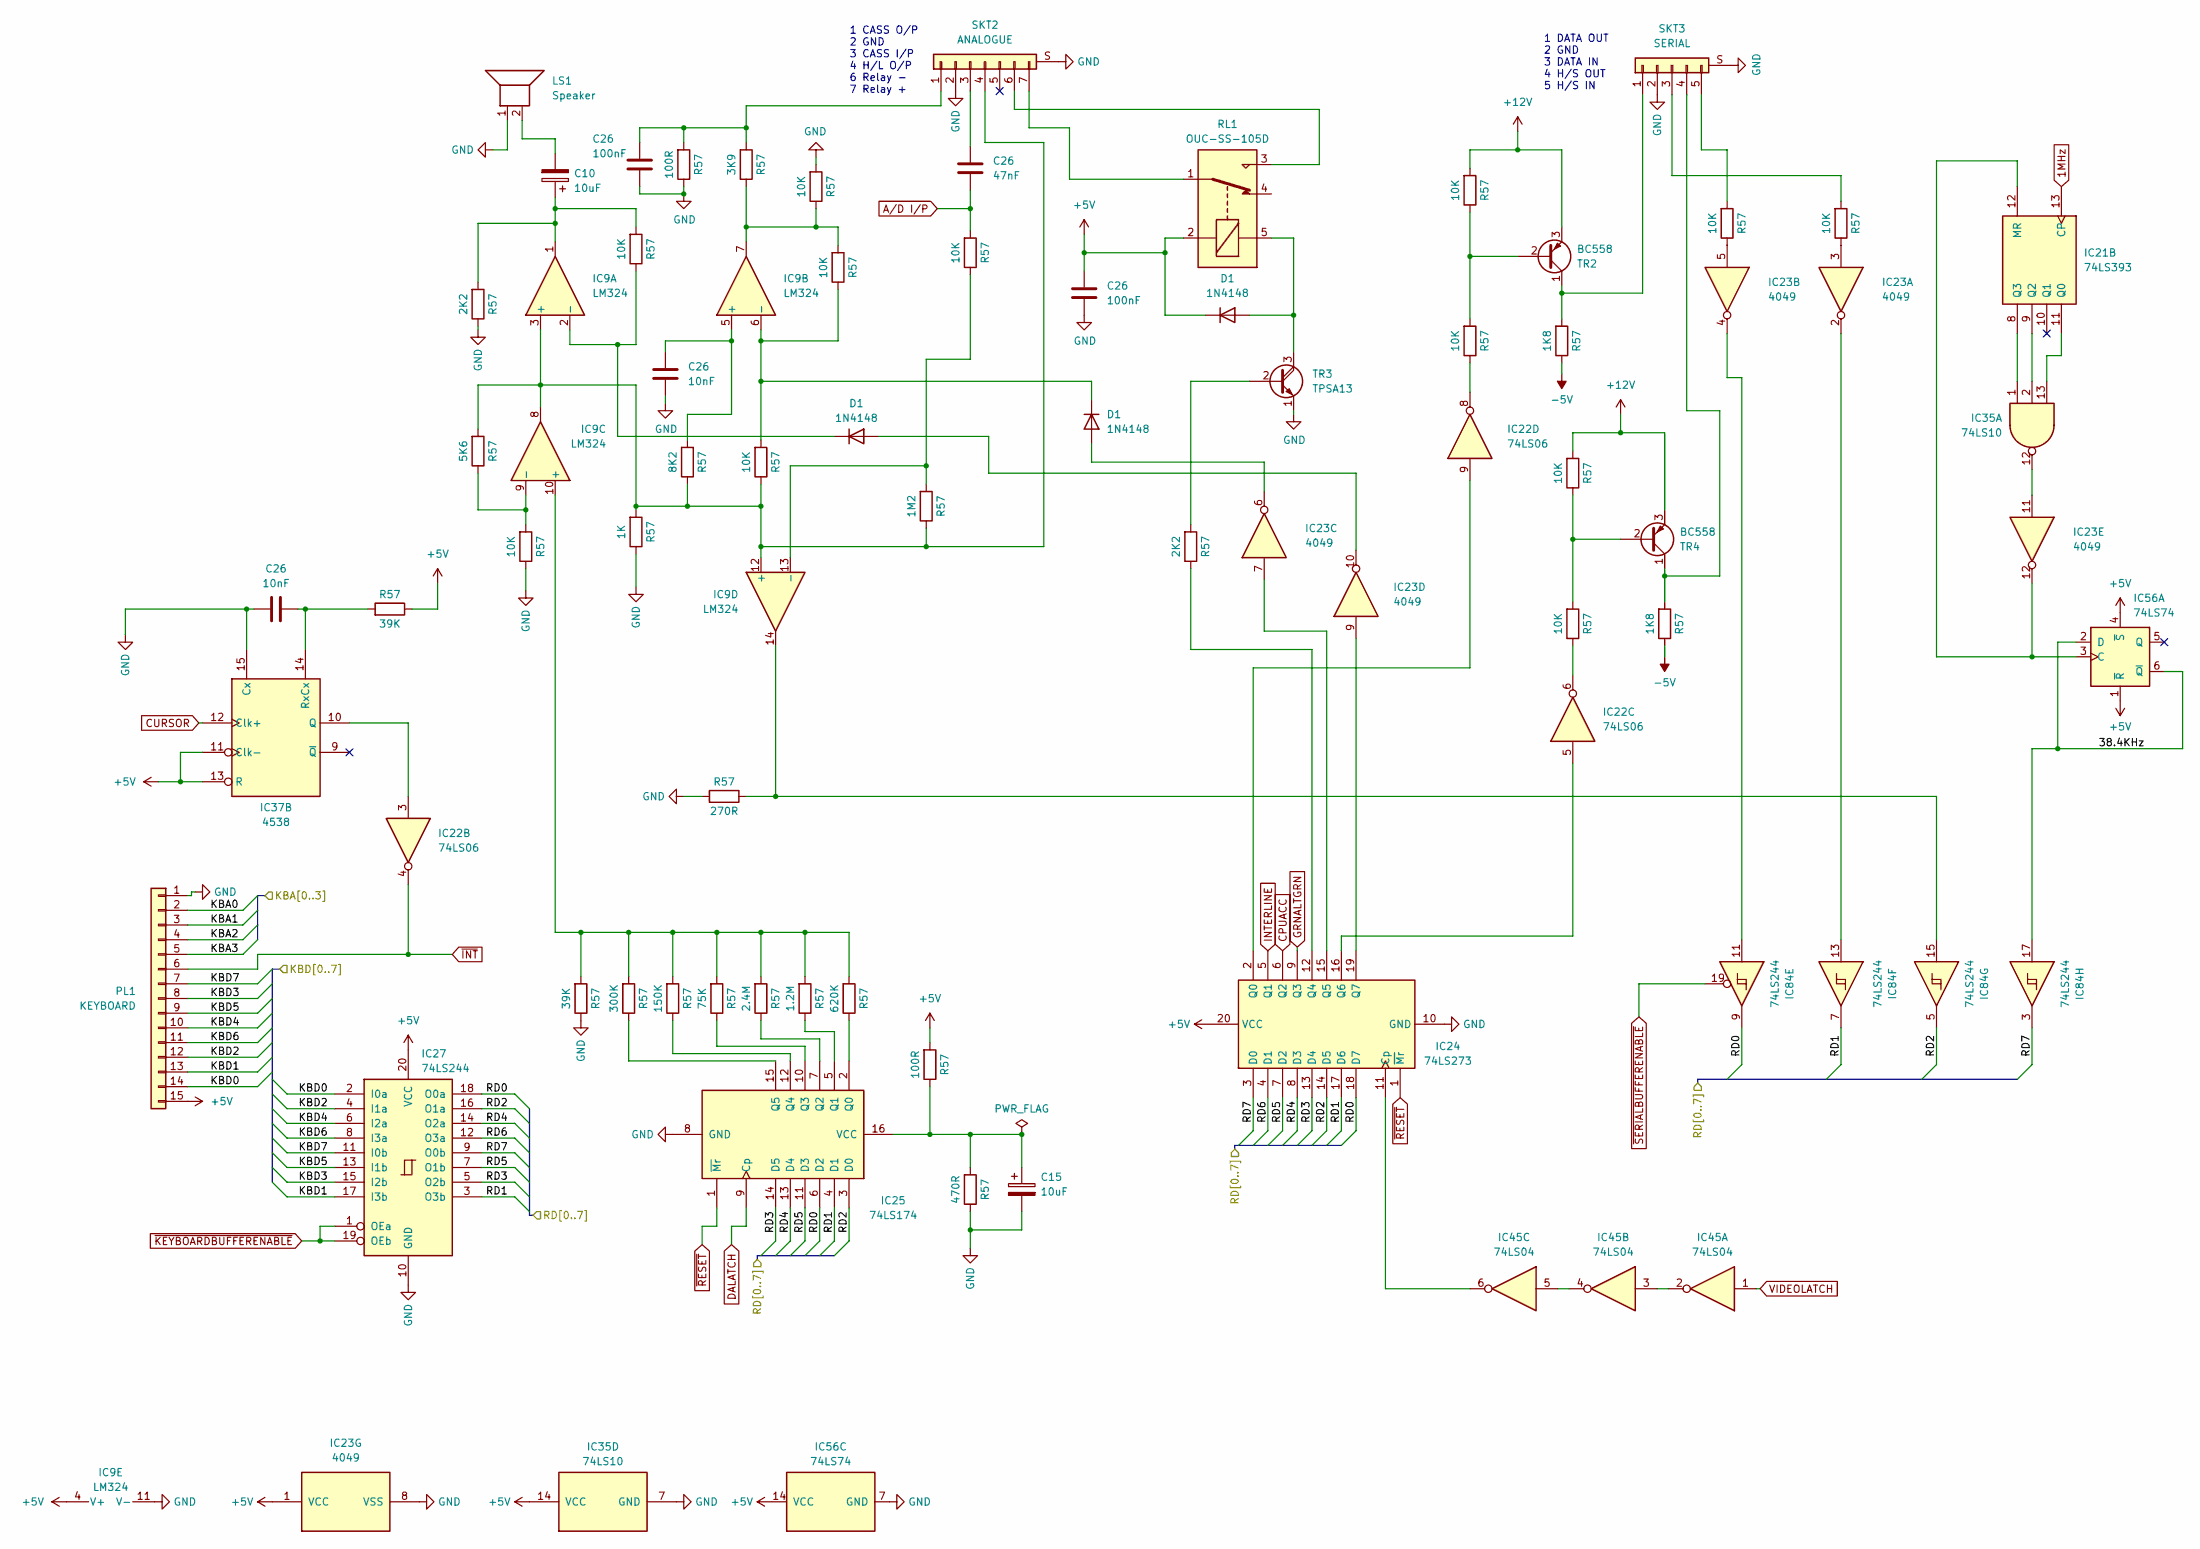
[picture p29: schematic lynx_io.kicad_sch]

Parts:
C10, C15: 10uF; Elec_5.08mm - No Box
C26: 10nF; C_Disc_5.08mm - Large Box
D1: 1N4148; Diode 7.62mm
IC9: LM324; DIP-14_W7.62mm
IC21: 74LS393; DIP-14_W7.62mm
IC22: 74LS06; DIP-14_W7.62mm
IC23: 4049; DIP-16_W7.62mm
IC24: 74LS273; DIP-20_W7.62mm
IC25: 74LS174; DIP-16_W7.62mm
IC27, IC84: 74LS244; DIP-20_W7.62mm
IC35: 74LS10; DIP-14_W7.62mm
IC37: 4538; DIP-16_W7.62mm
IC45: 74LS04; DIP-14_W7.62mm
IC56: 74LS74; DIP-14_W7.62mm
LS1: Speaker; LK 2-pin 2.54mm - No Box
PL1: KEYBOARD; PL1 - No Box
R57: 2.4M; Resistor 10.16mm
RL1: OUC-SS-105D; RL1 Relay
SKT2: ANALOGUE; DIN7
SKT3: SERIAL; DIN5
TR2, TR4: BC558; Transistor - No Box
TR3: TPSA13; Transistor - No Box

Connections:
1MHz: IC21.13 (CP)
38.4KHz: IC56.2 (D), IC56.6 (~Q), IC84.17
+5V: C26.2, D1.1 (K), IC9.4 (V+), IC23.1 (VCC), IC24.20 (VCC), IC27.20 (VCC), IC35.14 (VCC), IC37.11 (Clk-), IC37.13 (R), IC56.1 (~R), IC56.4 (~S), IC56.14 (VCC), PL1.15, R57.1, R57.2, RL1.2
+12V: R57.2, TR2.3 (E), TR4.3 (E)
-5V: R57.1
A/D I/P: C26.1, R57.2
CPUACC: IC24.6 (Q2)
CURSOR: IC37.12 (Clk+)
DALATCH: IC25.9 (Cp)
GND: C15.2, C26.1, IC9.11 (V-), IC23.8 (VSS), IC24.10 (GND), IC25.8 (GND), IC27.10 (GND), IC35.7 (GND), IC37.15 (Cx), IC56.7 (GND), LS1.1, PL1.1, R57.1, R57.2, SKT2.2, SKT2.S (SHIELD), SKT3.2, SKT3.S (SHIELD), TR3.1 (E)
GRNALTGRN: IC24.9 (Q3)
INTERLINE: IC24.5 (Q1)
KBA0: PL1.2
KBA1: PL1.3
KBA2: PL1.4
KBA3: PL1.5
KBD0: IC27.2 (I0a), PL1.14
KBD1: IC27.17 (I3b), PL1.13
KBD2: IC27.4 (I1a), PL1.12
KBD3: IC27.15 (I2b), PL1.8
KBD4: IC27.6 (I2a), PL1.10
KBD5: IC27.13 (I1b), PL1.9
KBD6: IC27.8 (I3a), PL1.11
KBD7: IC27.11 (I0b), PL1.7
unnamed: C10.1, IC9.1, R57.2
unnamed: C10.2, LS1.2
unnamed: C15.1, IC25.16 (VCC), R57.1, R57.2
unnamed: C26.2, IC9.5 (+), IC37.14 (RxCx), R57.2, SKT2.1, SKT2.3
unnamed: D1.1 (K), IC9.2 (-), IC9.6 (-), R57.1, R57.2
unnamed: D1.2 (A), IC23.6, IC23.10, RL1.5, TR3.3 (C)
unnamed: IC9.7, R57.1, R57.2
unnamed: IC9.9 (-), R57.1, R57.2
unnamed: IC9.10 (+), R57.2
unnamed: IC9.3 (+), IC9.8, IC9.12 (+), R57.1, R57.2, SKT2.4
unnamed: IC9.13 (-), R57.1, R57.2
unnamed: IC21.8 (Q3), IC35.1
unnamed: IC21.9 (Q2), IC35.2
unnamed: IC21.11 (Q0), IC35.13
unnamed: IC21.12 (MR), IC23.12, IC56.3 (C)
unnamed: IC22.3, IC37.10 (Q)
unnamed: IC22.5, IC24.16 (Q6)
unnamed: IC22.6, R57.1
unnamed: IC22.8, R57.1
unnamed: IC22.9, IC24.2 (Q0)
unnamed: IC23.2, IC84.13
unnamed: IC23.3, R57.1
unnamed: IC23.4, IC84.11
unnamed: IC23.5, R57.1
unnamed: IC23.7, IC24.15 (Q5)
unnamed: IC23.9, IC24.19 (Q7)
unnamed: IC23.11, IC35.12
unnamed: IC24.11 (Cp), IC45.6
unnamed: IC24.12 (Q4), R57.1
unnamed: IC25.2 (Q0), R57.1
unnamed: IC25.5 (Q1), R57.1
unnamed: IC25.7 (Q2), R57.1
unnamed: IC25.10 (Q3), R57.1
unnamed: IC25.12 (Q4), R57.1
unnamed: IC25.15 (Q5), R57.1
unnamed: IC45.2, IC45.3
unnamed: IC45.4, IC45.5
unnamed: IC9.14, IC84.15, R57.1
unnamed: R57.1, R57.2, TR2.2 (B), TR4.2 (B)
unnamed: R57.2, SKT3.1, SKT3.3, SKT3.4, SKT3.5, TR2.1 (C), TR3.2 (B), TR4.1 (C)
unnamed: RL1.1, SKT2.7
unnamed: RL1.3, SKT2.6
RD0: IC24.18 (D7), IC25.6 (D2), IC27.18 (O0a), IC84.9
RD1: IC24.17 (D6), IC25.4 (D1), IC27.3 (O3b), IC84.7
RD2: IC24.14 (D5), IC25.3 (D0), IC27.16 (O1a), IC84.5
RD3: IC24.13 (D4), IC25.14 (D5), IC27.5 (O2b)
RD4: IC24.8 (D3), IC25.13 (D4), IC27.14 (O2a)
RD5: IC24.7 (D2), IC25.11 (D3), IC27.7 (O1b)
RD6: IC24.4 (D1), IC27.12 (O3a)
RD7: IC24.3 (D0), IC27.9 (O0b), IC84.3
VIDEOLATCH: IC45.1
~INT: IC22.4, PL1.6
~KEYBOARDBUFFERENABLE: IC27.1 (OEa), IC27.19 (OEb)
~RESET: IC24.1 (~Mr), IC25.1 (~Mr)
~SERIALBUFFERENABLE: IC84.19

Notes on the sheet:
1 DATA OUT 2 GND 3 DATA IN 4 H/S OUT 5 H/S IN
1 CASS O/P 2 GND 3 CASS I/P 4 H/L O/P 6 Relay - 7 Relay +
