Board-Folk/Camputers-Lynx/Lynx 128/Kicad/lynx_nmi.kicad_sch

## KiCad design Lynx 128/Kicad/lynx_nmi.kicad_sch (2025-07-15)

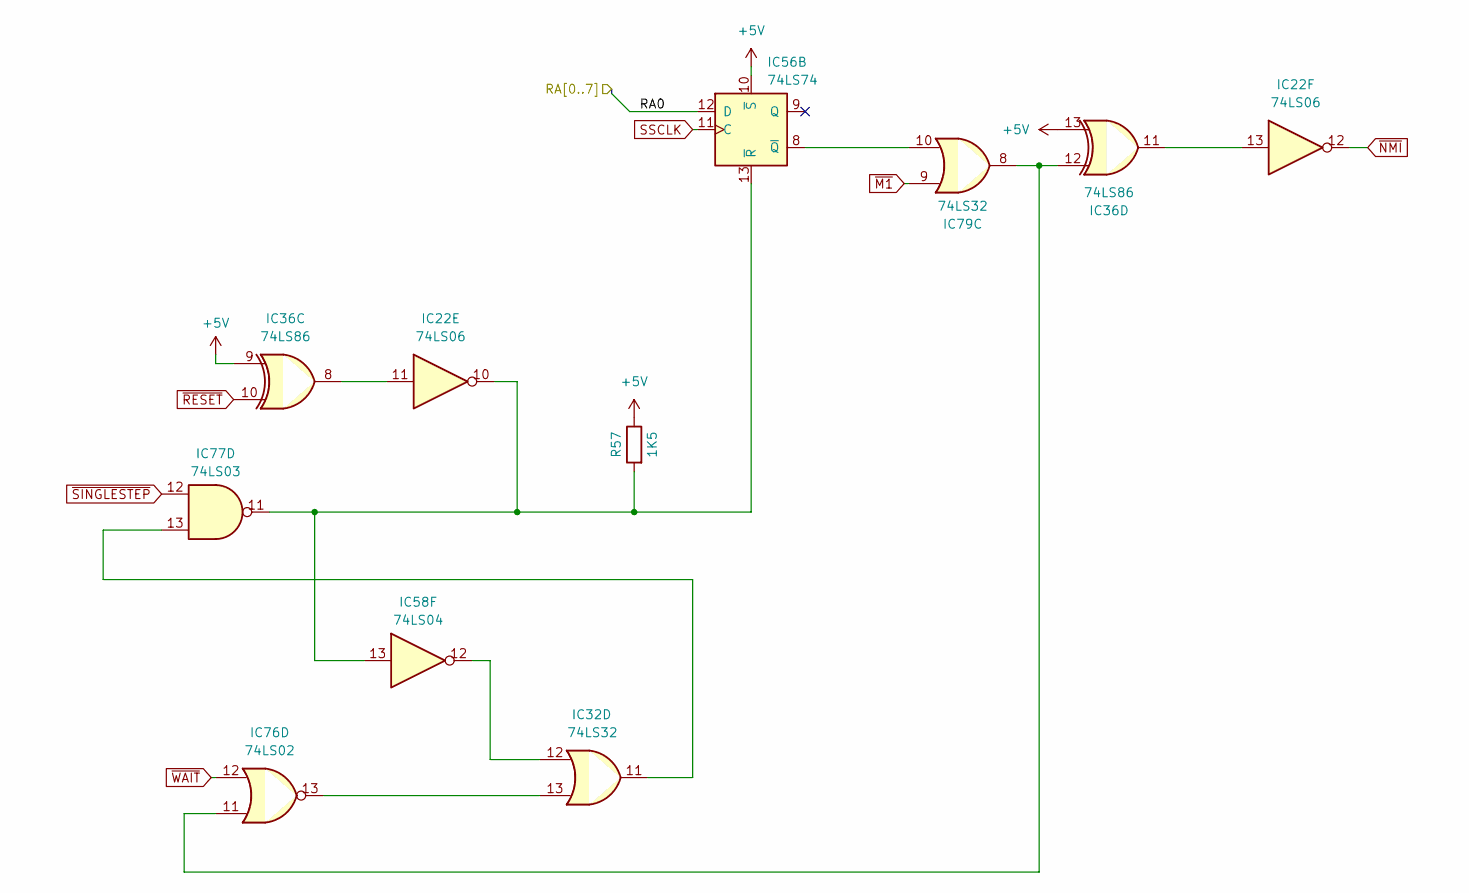
[picture p30: schematic lynx_nmi.kicad_sch]

Parts:
IC22: 74LS06; DIP-14_W7.62mm
IC32, IC79: 74LS32; DIP-14_W7.62mm
IC36: 74LS86; DIP-14_W7.62mm
IC56: 74LS74; DIP-14_W7.62mm
IC58: 74LS04; DIP-14_W7.62mm
IC76: 74LS02; DIP-14_W7.62mm
IC77: 74LS03; DIP-14_W7.62mm
R57: 1K5; Resistor 10.16mm

Connections:
+5V: IC36.9, IC36.13, IC56.10 (~S), R57.1
unnamed: IC22.10, IC56.13 (~R), IC58.13, IC77.11, R57.2
unnamed: IC22.11, IC36.8
unnamed: IC22.13, IC36.11
unnamed: IC32.11, IC77.13
unnamed: IC32.12, IC58.12
unnamed: IC32.13, IC76.13
unnamed: IC36.12, IC76.11, IC79.8
unnamed: IC56.8 (~Q), IC79.10
RA0: IC56.12 (D)
SSCLK: IC56.11 (C)
~M1: IC79.9
~NMI: IC22.12
~RESET: IC36.10
~SINGLESTEP: IC77.12
~WAIT: IC76.12
