Board-Folk/Camputers-Lynx/Lynx 128/Kicad/lynx_pal.kicad_sch

## KiCad design Lynx 128/Kicad/lynx_pal.kicad_sch (2025-07-15)

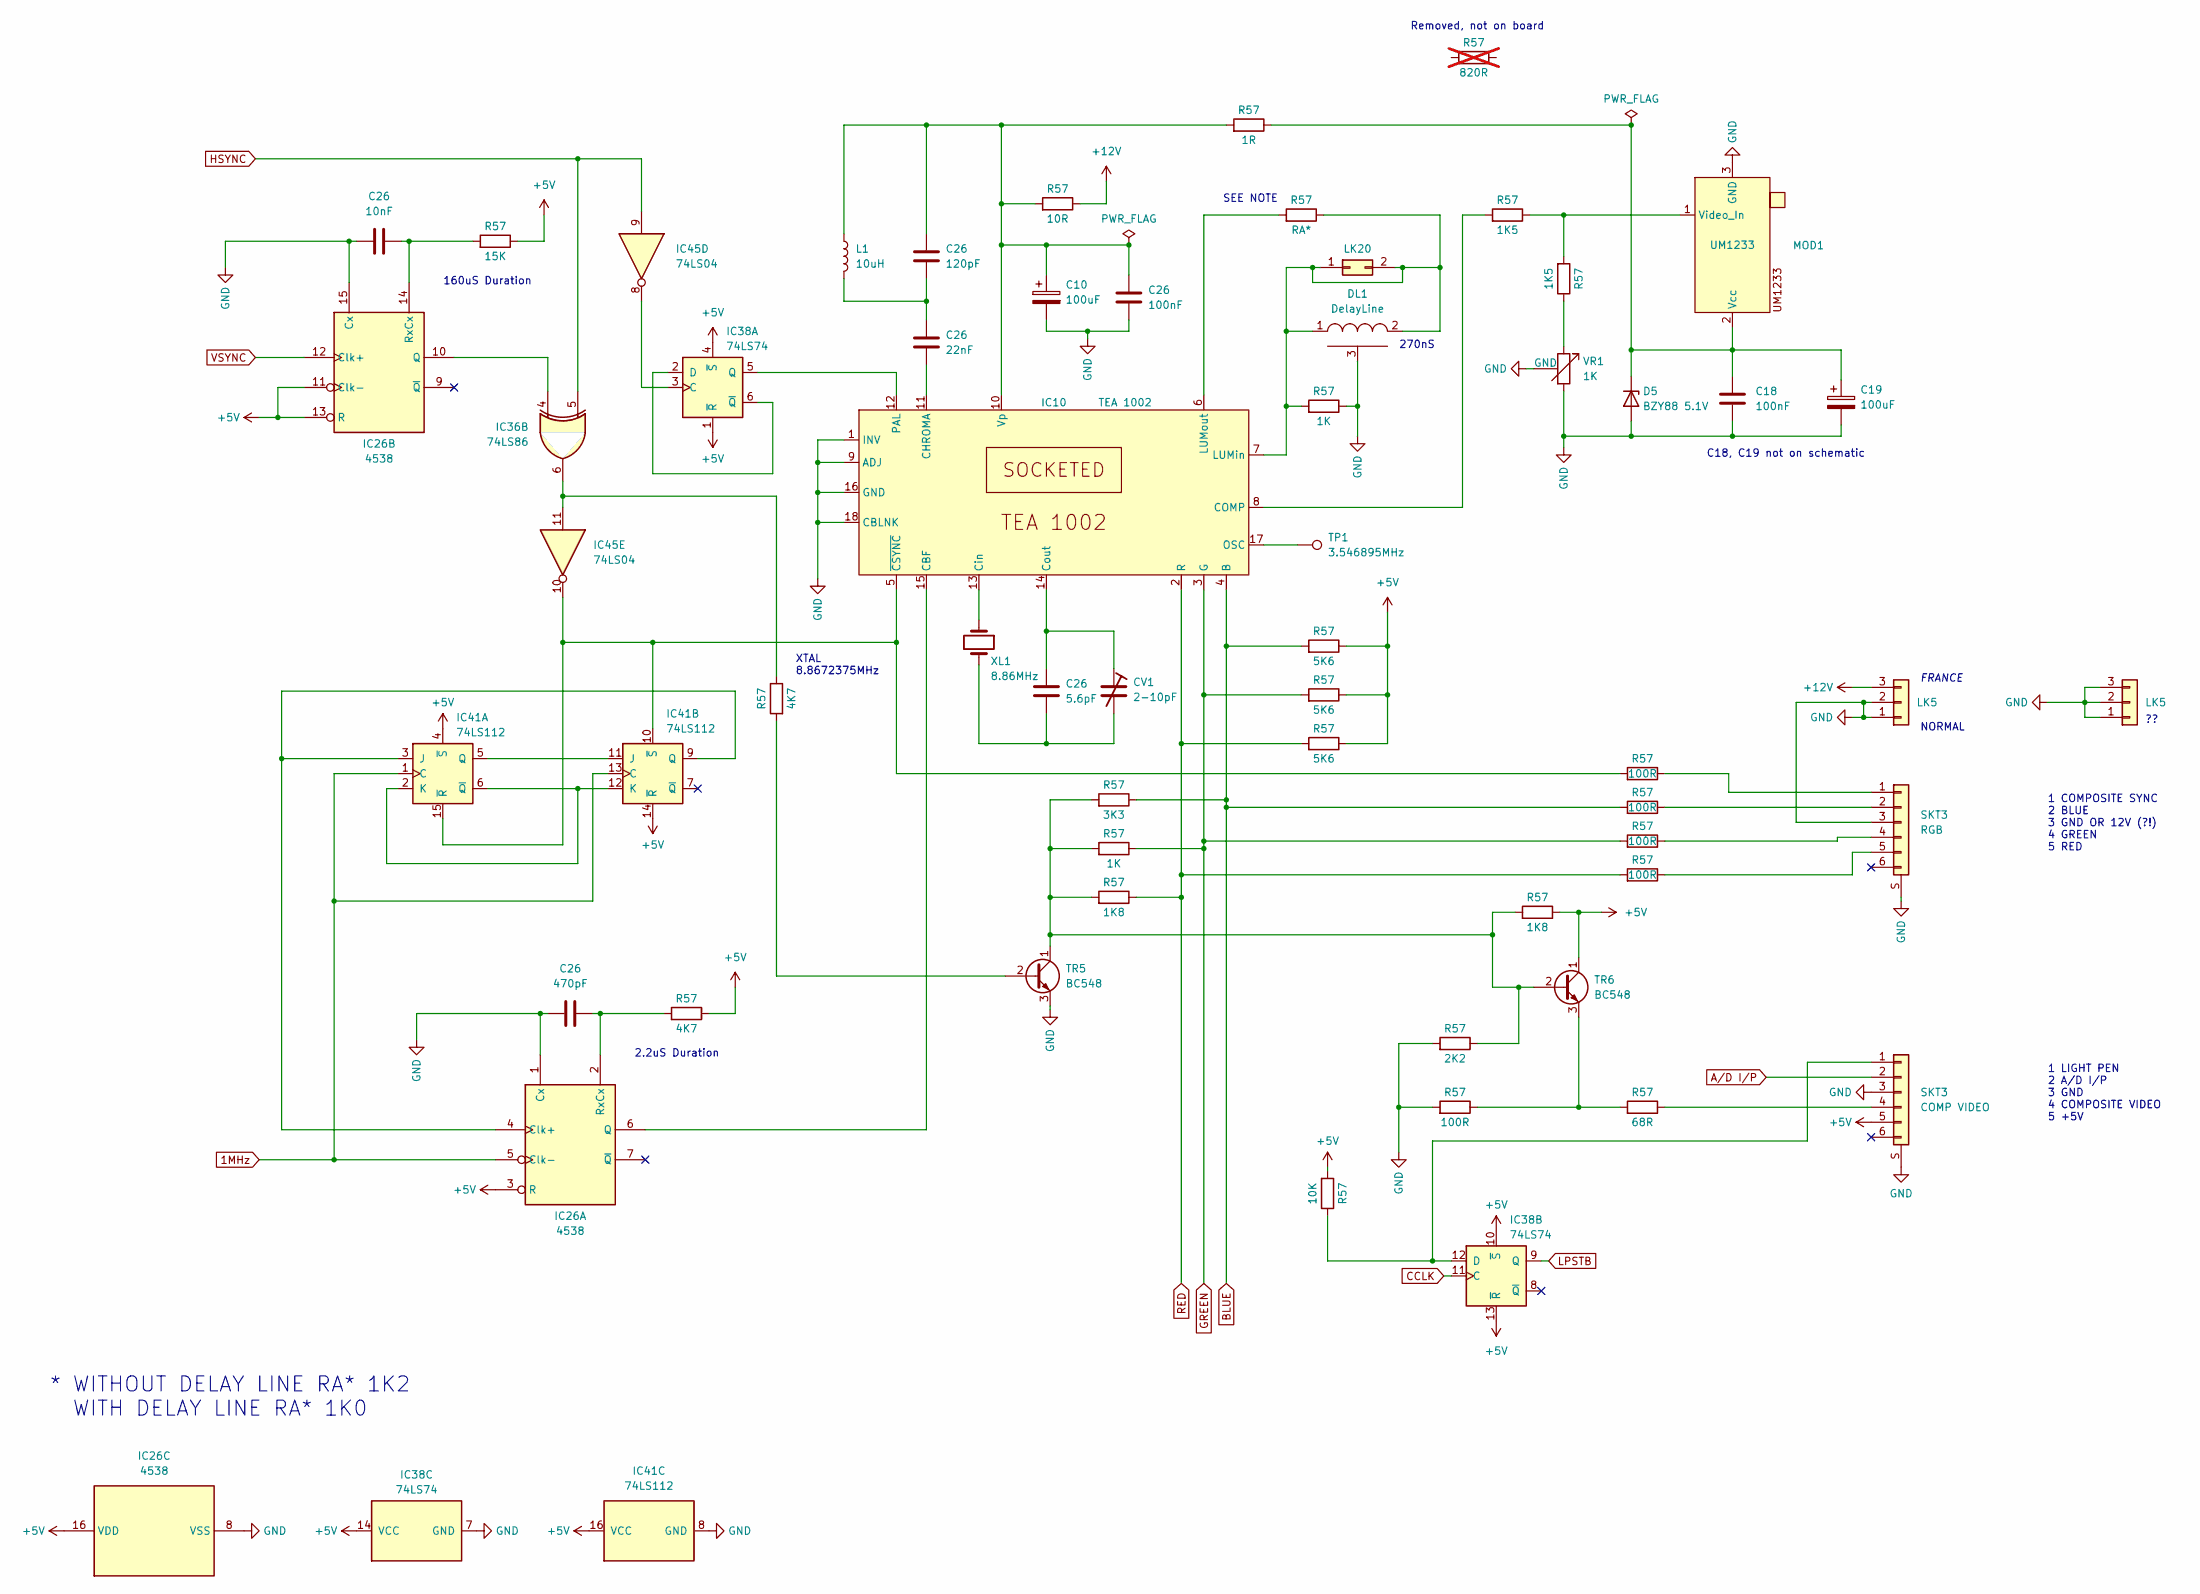
[picture p31: schematic lynx_pal.kicad_sch]

Parts:
C10, C19: 100uF; Elec_5.08mm - No Box
C18, C26: 100nF; C_Disc_5.08mm - Large Box
CV1: 2-10pF; CV1 Trimmer
D5: BZY88 5.1V; Diode 7.62mm
DL1: DelayLine; DL1
IC10: TEA 1002; DIP-18_W7.62mm
IC26: 4538; DIP-16_W7.62mm
IC36: 74LS86; DIP-14_W7.62mm
IC38: 74LS74; DIP-14_W7.62mm
IC41: 74LS112; DIP-16_W7.62mm
IC45: 74LS04; DIP-14_W7.62mm
L1: 10uH; 5.08mm Misc - No Box
LK5: EARTH; LK21
LK20: LK 2-pin 2.54mm - No Box
MOD1: UM1233; Modulator
R57: 68R; Resistor 10.16mm
SKT3: COMP VIDEO; DIN6
TP1: 3.546895MHz; Test Point
TR5, TR6: BC548; Transistor - No Box
VR1: 1K; VR1
XL1: 8.86MHz; 5.08mm Misc - No Box

Connections:
1MHz: IC26.5 (Clk-), IC41.1 (C), IC41.13 (C)
+5V: IC26.3 (R), IC26.11 (Clk-), IC26.13 (R), IC26.16 (VDD), IC38.1 (~R), IC38.4 (~S), IC38.10 (~S), IC38.13 (~R), IC38.14 (VCC), IC41.4 (~S), IC41.14 (~R), IC41.16 (VCC), R57.1, R57.2, SKT3.5, TR6.1 (C)
+12V: LK5.3, R57.1
A/D I/P: SKT3.2
BLUE: IC10.4 (B), R57.1, R57.2
CCLK: IC38.11 (C)
GND: C10.2, C18.2, C19.2, C26.1, D5.2 (A), DL1.3 (COMMUN), IC10.1 (INV), IC10.9 (ADJ), IC10.16 (GND), IC10.18 (CBLNK), IC26.1 (Cx), IC26.8 (VSS), IC26.15 (Cx), IC38.7 (GND), IC41.8 (GND), LK5.1, LK5.2, LK5.3, MOD1.3 (GND), R57.1, R57.2, SKT3.3, SKT3.S (SHIELD), TR5.3 (E), VR1.2, VR1.3 (GND)
GREEN: IC10.3 (G), R57.1, R57.2
HSYNC: IC36.5, IC45.9
LPSTB: IC38.9 (Q)
unnamed: C10.1, C26.2, IC10.10 (Vp), L1.1, R57.2
unnamed: C18.1, C19.1, D5.1 (K), MOD1.2 (Vcc), R57.1
unnamed: C26.1, C26.2, CV1.2, IC10.11 (CHROMA), L1.2, XL1.2
unnamed: C26.2, CV1.1, IC10.14 (Cout), IC26.2 (RxCx), IC26.14 (RxCx), R57.2
unnamed: DL1.1, DL1.2, IC10.7 (LUMin), LK20.1, LK20.2, R57.1, R57.2
unnamed: IC10.5 (~CSYNC), IC41.10 (~S), IC41.15 (~R), IC45.10, R57.2
unnamed: IC10.6 (LUMout), R57.2
unnamed: IC10.8 (COMP), R57.2
unnamed: IC10.12 (PAL), IC38.5 (Q)
unnamed: IC10.13 (Cin), XL1.1
unnamed: IC10.15 (CBF), IC26.6 (Q)
unnamed: IC10.17 (OSC), TP1.1
unnamed: IC26.4 (Clk+), IC41.3 (J), IC41.9 (Q)
unnamed: IC26.10 (Q), IC36.4
unnamed: IC36.6, IC45.11, R57.1
unnamed: IC38.2 (D), IC38.6 (~Q)
unnamed: IC38.3 (C), IC45.8
unnamed: IC38.12 (D), R57.1, SKT3.1
unnamed: IC41.5 (Q), IC41.11 (J)
unnamed: IC41.2 (K), IC41.6 (~Q), IC41.12 (K)
unnamed: MOD1.1 (Video_In), R57.1, R57.2
unnamed: R57.1, R57.2, SKT3.1, SKT3.2, SKT3.4, SKT3.5, TR5.1 (C), TR6.2 (B), TR6.3 (E), VR1.1
unnamed: R57.2, TR5.2 (B)
RED: IC10.2 (R), R57.1, R57.2
VSYNC: IC26.12 (Clk+)

Notes on the sheet:
NORMAL
SEE NOTE
Removed, not on board
1 COMPOSITE SYNC 2 BLUE 3 GND OR 12V (?!) 4 GREEN 5 RED
2.2uS Duration
FRANCE
160uS Duration
C18, C19 not on schematic
1 LIGHT PEN 2 A/D I/P 3 GND 4 COMPOSITE VIDEO 5 +5V
XTAL 8.8672375MHz
* WITHOUT DELAY LINE RA* 1K2 WITH DELAY LINE RA* 1K0
270nS
