Board-Folk/Camputers-Lynx/Lynx 128/Kicad/lynx_power.kicad_sch

## KiCad design Lynx 128/Kicad/lynx_power.kicad_sch (2025-07-15)

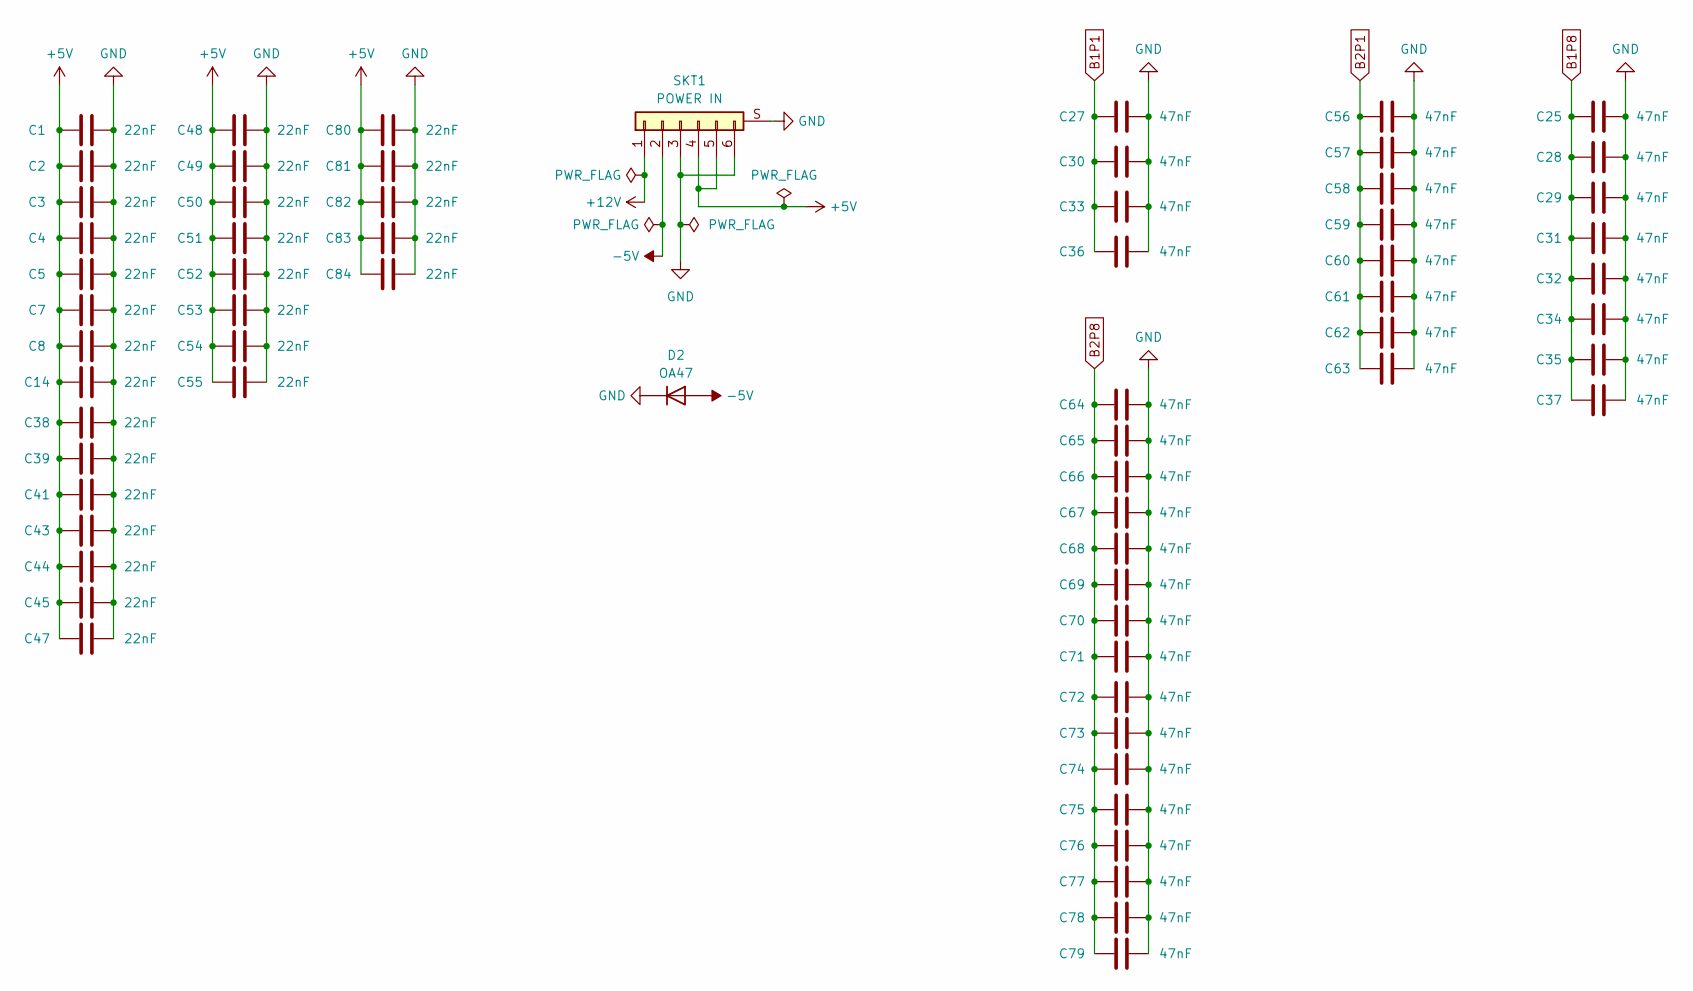
[picture p32: schematic lynx_power.kicad_sch]

Parts:
C1, C2, C3, C4, C5, C7, C8, C14, C38, C39, C41, C43, C44, C45, C47, C48, C49, C50, C51, C52, C53, C54, C55, C81, C82: 22nF; C_Disc_5.08mm - Large Box
C25, C27, C28, C29, C30, C31, C32, C33, C34, C35, C36, C37, C56, C57, C58, C59, C60, C61, C62, C63, C64, C65, C66, C67, C68, C69, C70, C71, C72, C73, C74, C75, C76, C77, C78, C79: 47nF; C_Disc_5.08mm
C80, C83, C84: 22nF; C_Disc_5.08mm
D2: OA47; Diode 10.16mm
SKT1: POWER IN; DIN6

Connections:
+5V: C1.1, C2.1, C3.1, C4.1, C5.1, C7.1, C8.1, C14.1, C38.1, C39.1, C41.1, C43.1, C44.1, C45.1, C47.1, C48.1, C49.1, C50.1, C51.1, C52.1, C53.1, C54.1, C55.1, C80.1, C81.1, C82.1, C83.1, C84.1, SKT1.4, SKT1.5
+12V: SKT1.1
-5V: D2.2 (A), SKT1.2
B1P1: C27.1, C30.1, C33.1, C36.1
B1P8: C25.1, C28.1, C29.1, C31.1, C32.1, C34.1, C35.1, C37.1
B2P1: C56.1, C57.1, C58.1, C59.1, C60.1, C61.1, C62.1, C63.1
B2P8: C64.1, C65.1, C66.1, C67.1, C68.1, C69.1, C70.1, C71.1, C72.1, C73.1, C74.1, C75.1, C76.1, C77.1, C78.1, C79.1
GND: C1.2, C2.2, C3.2, C4.2, C5.2, C7.2, C8.2, C14.2, C25.2, C27.2, C28.2, C29.2, C30.2, C31.2, C32.2, C33.2, C34.2, C35.2, C36.2, C37.2, C38.2, C39.2, C41.2, C43.2, C44.2, C45.2, C47.2, C48.2, C49.2, C50.2, C51.2, C52.2, C53.2, C54.2, C55.2, C56.2, C57.2, C58.2, C59.2, C60.2, C61.2, C62.2, C63.2, C64.2, C65.2, C66.2, C67.2, C68.2, C69.2, C70.2, C71.2, C72.2, C73.2, C74.2, C75.2, C76.2, C77.2, C78.2, C79.2, C80.2, C81.2, C82.2, C83.2, C84.2, D2.1 (K), SKT1.3, SKT1.6, SKT1.S (SHIELD)
