Board-Folk/Camputers-Lynx/Lynx 128/Kicad/lynx_ram.kicad_sch

## KiCad design Lynx 128/Kicad/lynx_ram.kicad_sch (2025-07-15)

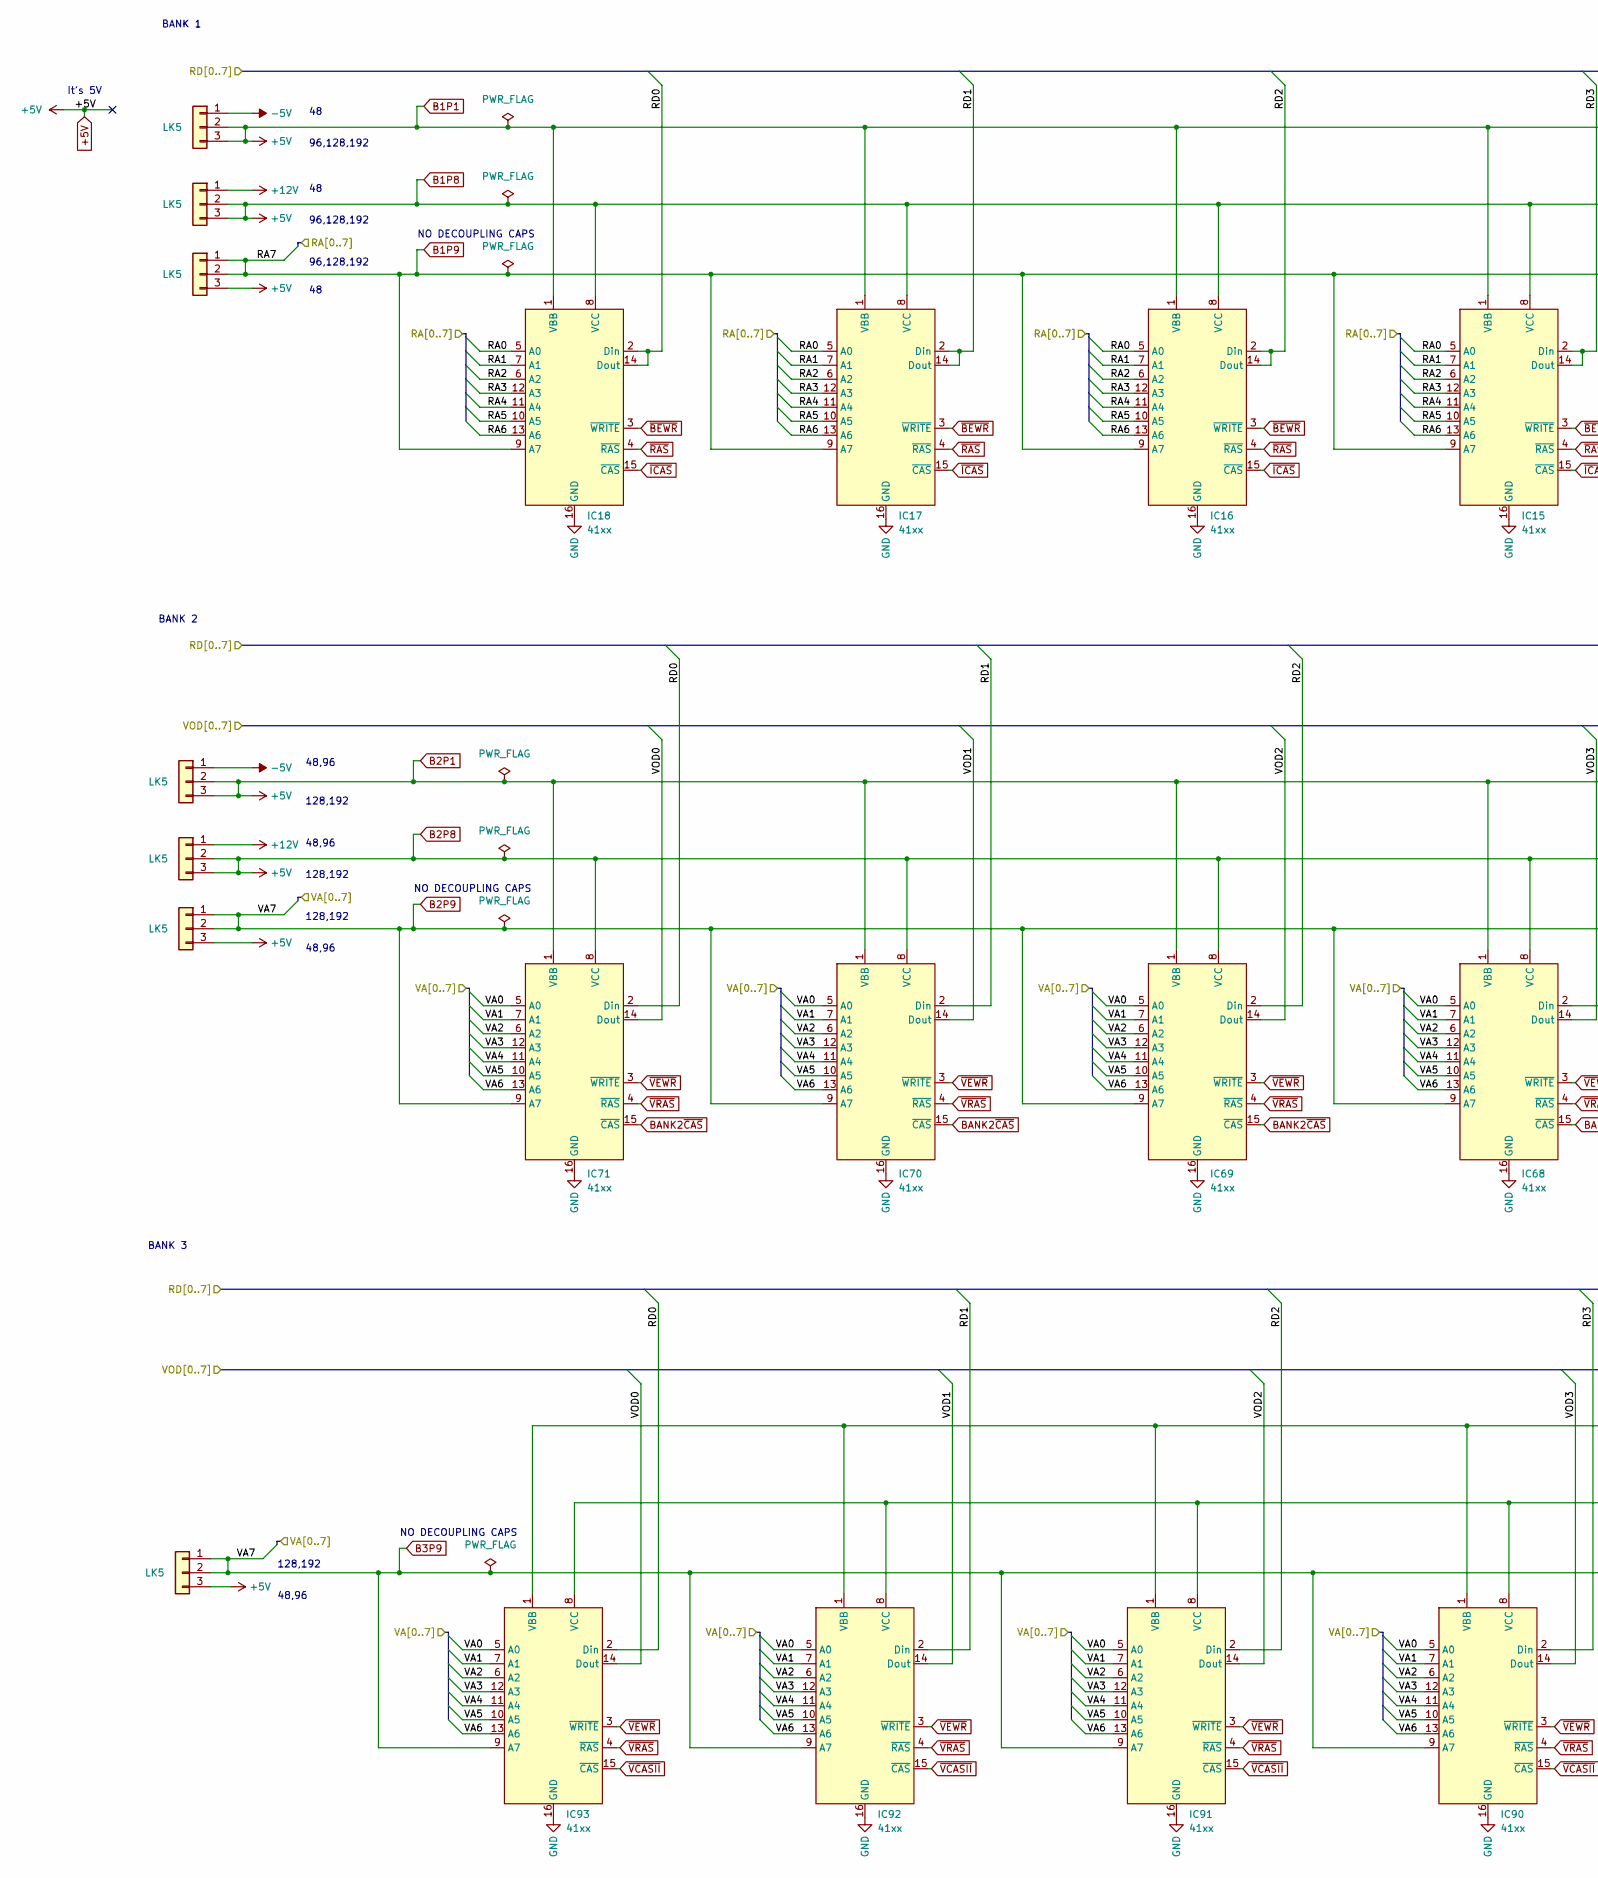
[picture p33: schematic lynx_ram.kicad_sch, part in row 1, column 1]

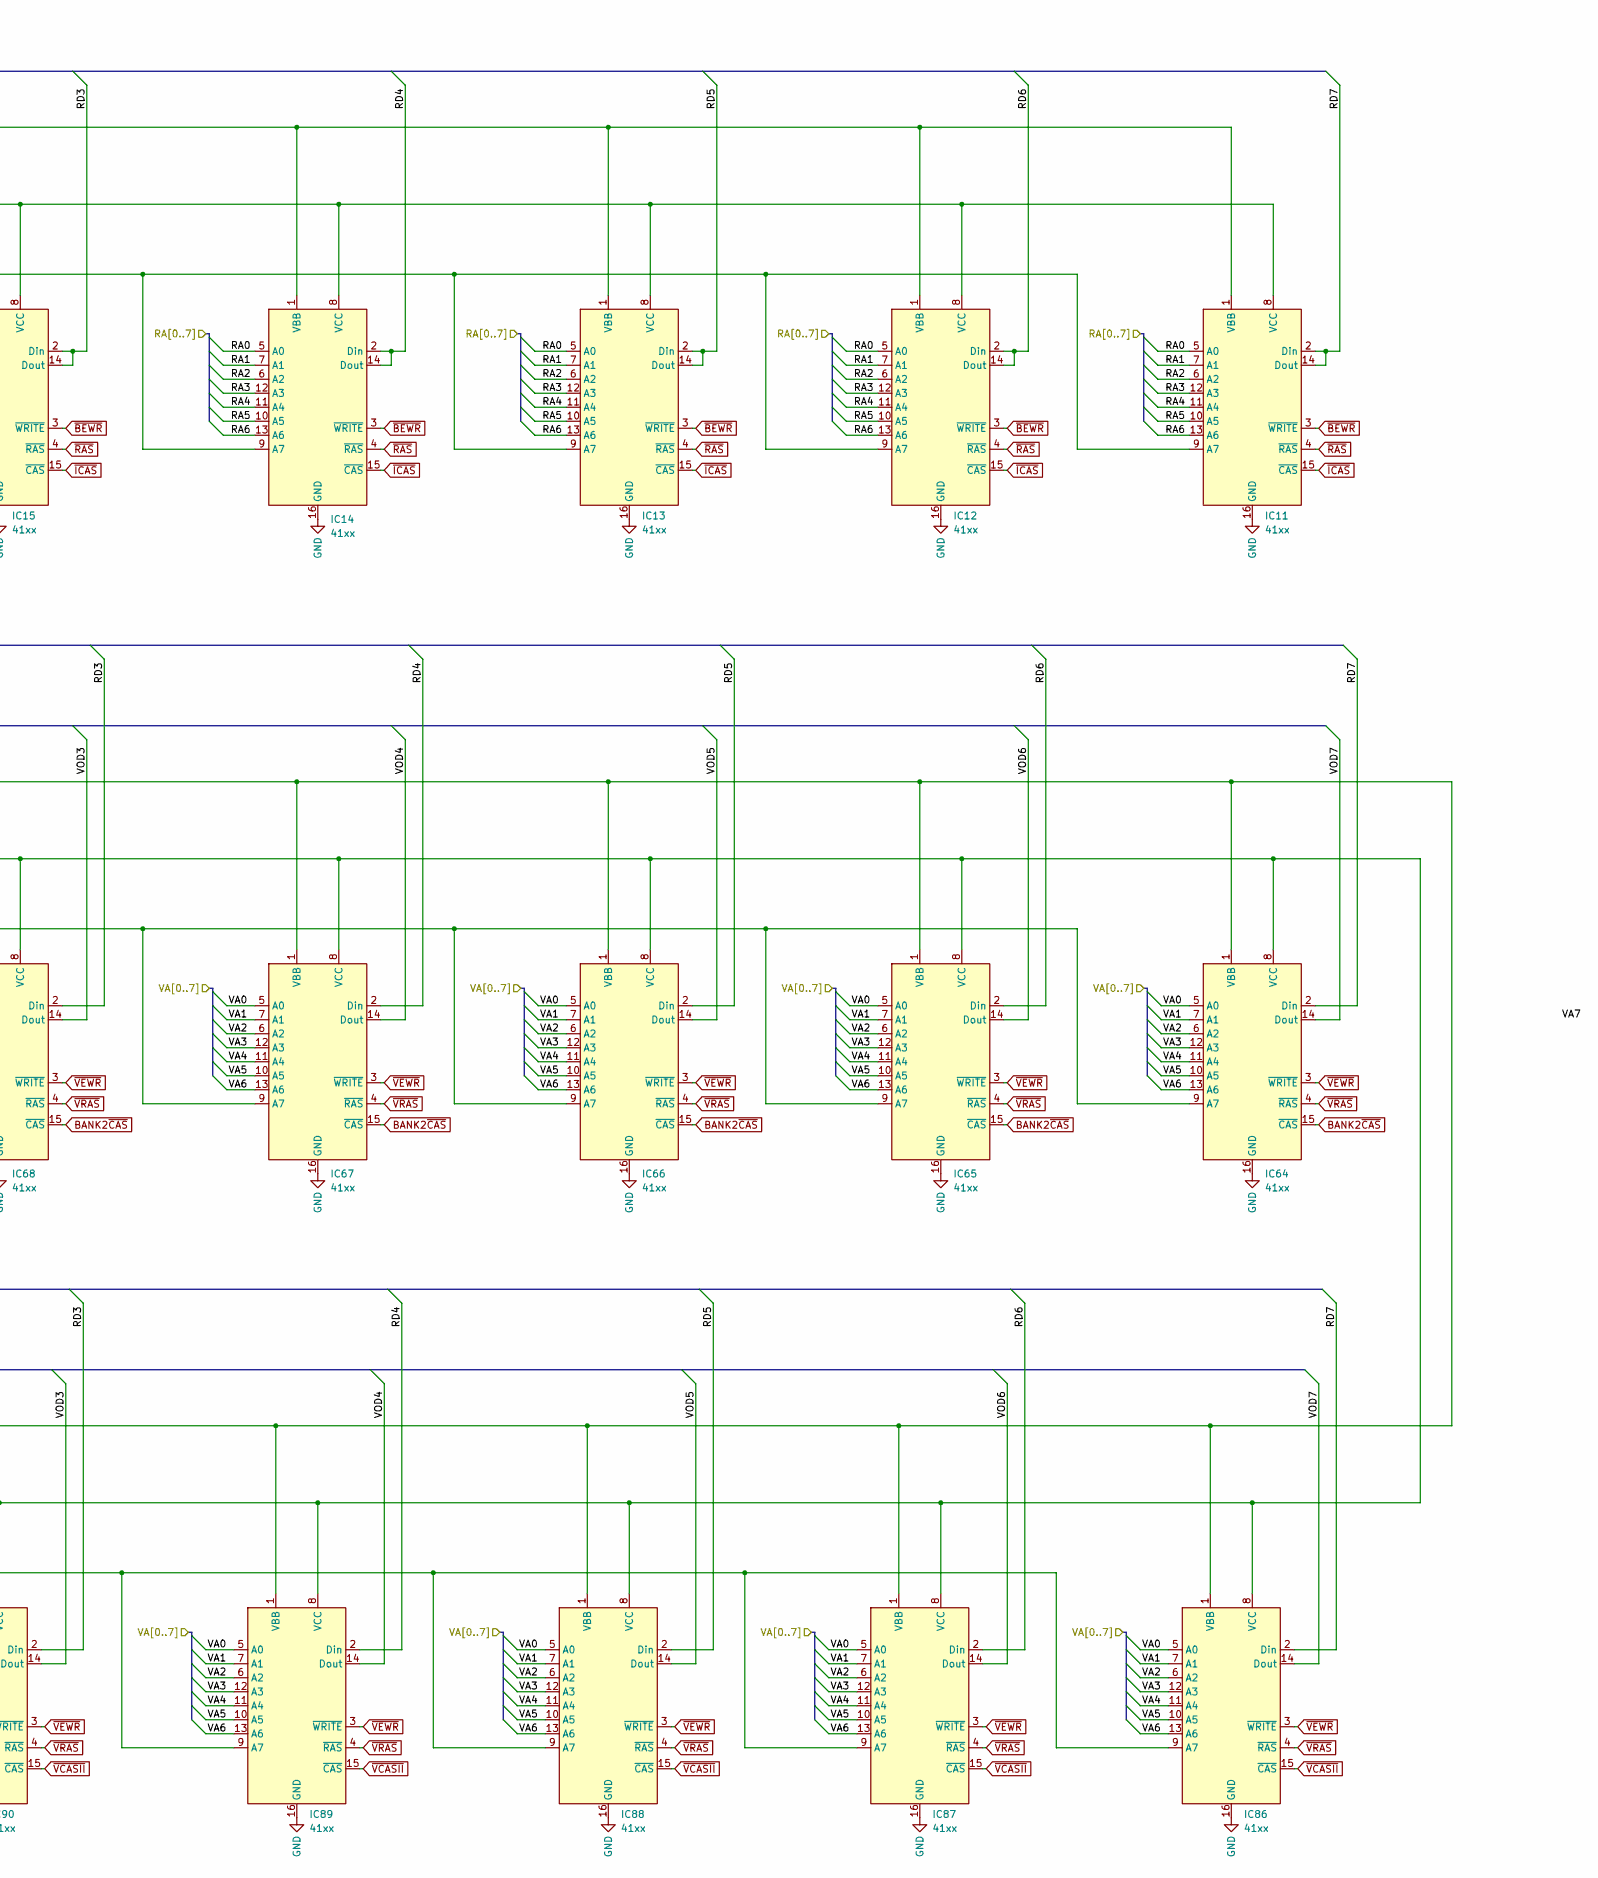
[picture p34: schematic lynx_ram.kicad_sch, part in row 1, column 2]

Parts:
IC11, IC12, IC13, IC14, IC15, IC16, IC17, IC18, IC64, IC65, IC66, IC67, IC68, IC69, IC70, IC71, IC86, IC87, IC88, IC89, IC90, IC91, IC92, IC93: 41xx; DIP-16_W7.62mm
LK5: -; LK 3-Pin 2.54mm - No Box

Connections:
+5V: IC11.1 (VBB), IC11.8 (VCC), IC12.1 (VBB), IC12.8 (VCC), IC13.1 (VBB), IC13.8 (VCC), IC14.1 (VBB), IC14.8 (VCC), IC15.1 (VBB), IC15.8 (VCC), IC16.1 (VBB), IC16.8 (VCC), IC17.1 (VBB), IC17.8 (VCC), IC18.1 (VBB), IC18.8 (VCC), IC64.1 (VBB), IC64.8 (VCC), IC65.1 (VBB), IC65.8 (VCC), IC66.1 (VBB), IC66.8 (VCC), IC67.1 (VBB), IC67.8 (VCC), IC68.1 (VBB), IC68.8 (VCC), IC69.1 (VBB), IC69.8 (VCC), IC70.1 (VBB), IC70.8 (VCC), IC71.1 (VBB), IC71.8 (VCC), IC86.1 (VBB), IC86.8 (VCC), IC87.1 (VBB), IC87.8 (VCC), IC88.1 (VBB), IC88.8 (VCC), IC89.1 (VBB), IC89.8 (VCC), IC90.1 (VBB), IC90.8 (VCC), IC91.1 (VBB), IC91.8 (VCC), IC92.1 (VBB), IC92.8 (VCC), IC93.1 (VBB), IC93.8 (VCC), LK5.2, LK5.3
+12V: LK5.1
-5V: LK5.1
B1P9: IC11.9 (A7), IC12.9 (A7), IC13.9 (A7), IC14.9 (A7), IC15.9 (A7), IC16.9 (A7), IC17.9 (A7), IC18.9 (A7), LK5.1, LK5.2
B2P9: IC64.9 (A7), IC65.9 (A7), IC66.9 (A7), IC67.9 (A7), IC68.9 (A7), IC69.9 (A7), IC70.9 (A7), IC71.9 (A7), IC86.9 (A7), IC87.9 (A7), IC88.9 (A7), IC89.9 (A7), IC90.9 (A7), IC91.9 (A7), IC92.9 (A7), IC93.9 (A7), LK5.1, LK5.2
BANK2~CAS: IC64.15 (~CAS), IC65.15 (~CAS), IC66.15 (~CAS), IC67.15 (~CAS), IC68.15 (~CAS), IC69.15 (~CAS), IC70.15 (~CAS), IC71.15 (~CAS)
GND: IC11.16 (GND), IC12.16 (GND), IC13.16 (GND), IC14.16 (GND), IC15.16 (GND), IC16.16 (GND), IC17.16 (GND), IC18.16 (GND), IC64.16 (GND), IC65.16 (GND), IC66.16 (GND), IC67.16 (GND), IC68.16 (GND), IC69.16 (GND), IC70.16 (GND), IC71.16 (GND), IC86.16 (GND), IC87.16 (GND), IC88.16 (GND), IC89.16 (GND), IC90.16 (GND), IC91.16 (GND), IC92.16 (GND), IC93.16 (GND)
RA0: IC11.5 (A0), IC12.5 (A0), IC13.5 (A0), IC14.5 (A0), IC15.5 (A0), IC16.5 (A0), IC17.5 (A0), IC18.5 (A0)
RA1: IC11.7 (A1), IC12.7 (A1), IC13.7 (A1), IC14.7 (A1), IC15.7 (A1), IC16.7 (A1), IC17.7 (A1), IC18.7 (A1)
RA2: IC11.6 (A2), IC12.6 (A2), IC13.6 (A2), IC14.6 (A2), IC15.6 (A2), IC16.6 (A2), IC17.6 (A2), IC18.6 (A2)
RA3: IC11.12 (A3), IC12.12 (A3), IC13.12 (A3), IC14.12 (A3), IC15.12 (A3), IC16.12 (A3), IC17.12 (A3), IC18.12 (A3)
RA4: IC11.11 (A4), IC12.11 (A4), IC13.11 (A4), IC14.11 (A4), IC15.11 (A4), IC16.11 (A4), IC17.11 (A4), IC18.11 (A4)
RA5: IC11.10 (A5), IC12.10 (A5), IC13.10 (A5), IC14.10 (A5), IC15.10 (A5), IC16.10 (A5), IC17.10 (A5), IC18.10 (A5)
RA6: IC11.13 (A6), IC12.13 (A6), IC13.13 (A6), IC14.13 (A6), IC15.13 (A6), IC16.13 (A6), IC17.13 (A6), IC18.13 (A6)
RD0: IC18.2 (Din), IC18.14 (Dout), IC71.2 (Din), IC93.2 (Din)
RD1: IC17.2 (Din), IC17.14 (Dout), IC70.2 (Din), IC92.2 (Din)
RD2: IC16.2 (Din), IC16.14 (Dout), IC69.2 (Din), IC91.2 (Din)
RD3: IC15.2 (Din), IC15.14 (Dout), IC68.2 (Din), IC90.2 (Din)
RD4: IC14.2 (Din), IC14.14 (Dout), IC67.2 (Din), IC89.2 (Din)
RD5: IC13.2 (Din), IC13.14 (Dout), IC66.2 (Din), IC88.2 (Din)
RD6: IC12.2 (Din), IC12.14 (Dout), IC65.2 (Din), IC87.2 (Din)
RD7: IC11.2 (Din), IC11.14 (Dout), IC64.2 (Din), IC86.2 (Din)
VA0: IC64.5 (A0), IC65.5 (A0), IC66.5 (A0), IC67.5 (A0), IC68.5 (A0), IC69.5 (A0), IC70.5 (A0), IC71.5 (A0), IC86.5 (A0), IC87.5 (A0), IC88.5 (A0), IC89.5 (A0), IC90.5 (A0), IC91.5 (A0), IC92.5 (A0), IC93.5 (A0)
VA1: IC64.7 (A1), IC65.7 (A1), IC66.7 (A1), IC67.7 (A1), IC68.7 (A1), IC69.7 (A1), IC70.7 (A1), IC71.7 (A1), IC86.7 (A1), IC87.7 (A1), IC88.7 (A1), IC89.7 (A1), IC90.7 (A1), IC91.7 (A1), IC92.7 (A1), IC93.7 (A1)
VA2: IC64.6 (A2), IC65.6 (A2), IC66.6 (A2), IC67.6 (A2), IC68.6 (A2), IC69.6 (A2), IC70.6 (A2), IC71.6 (A2), IC86.6 (A2), IC87.6 (A2), IC88.6 (A2), IC89.6 (A2), IC90.6 (A2), IC91.6 (A2), IC92.6 (A2), IC93.6 (A2)
VA3: IC64.12 (A3), IC65.12 (A3), IC66.12 (A3), IC67.12 (A3), IC68.12 (A3), IC69.12 (A3), IC70.12 (A3), IC71.12 (A3), IC86.12 (A3), IC87.12 (A3), IC88.12 (A3), IC89.12 (A3), IC90.12 (A3), IC91.12 (A3), IC92.12 (A3), IC93.12 (A3)
VA4: IC64.11 (A4), IC65.11 (A4), IC66.11 (A4), IC67.11 (A4), IC68.11 (A4), IC69.11 (A4), IC70.11 (A4), IC71.11 (A4), IC86.11 (A4), IC87.11 (A4), IC88.11 (A4), IC89.11 (A4), IC90.11 (A4), IC91.11 (A4), IC92.11 (A4), IC93.11 (A4)
VA5: IC64.10 (A5), IC65.10 (A5), IC66.10 (A5), IC67.10 (A5), IC68.10 (A5), IC69.10 (A5), IC70.10 (A5), IC71.10 (A5), IC86.10 (A5), IC87.10 (A5), IC88.10 (A5), IC89.10 (A5), IC90.10 (A5), IC91.10 (A5), IC92.10 (A5), IC93.10 (A5)
VA6: IC64.13 (A6), IC65.13 (A6), IC66.13 (A6), IC67.13 (A6), IC68.13 (A6), IC69.13 (A6), IC70.13 (A6), IC71.13 (A6), IC86.13 (A6), IC87.13 (A6), IC88.13 (A6), IC89.13 (A6), IC90.13 (A6), IC91.13 (A6), IC92.13 (A6), IC93.13 (A6)
VOD0: IC71.14 (Dout), IC93.14 (Dout)
VOD1: IC70.14 (Dout), IC92.14 (Dout)
VOD2: IC69.14 (Dout), IC91.14 (Dout)
VOD3: IC68.14 (Dout), IC90.14 (Dout)
VOD4: IC67.14 (Dout), IC89.14 (Dout)
VOD5: IC66.14 (Dout), IC88.14 (Dout)
VOD6: IC65.14 (Dout), IC87.14 (Dout)
VOD7: IC64.14 (Dout), IC86.14 (Dout)
~BEWR: IC11.3 (~WRITE), IC12.3 (~WRITE), IC13.3 (~WRITE), IC14.3 (~WRITE), IC15.3 (~WRITE), IC16.3 (~WRITE), IC17.3 (~WRITE), IC18.3 (~WRITE)
~ICAS: IC11.15 (~CAS), IC12.15 (~CAS), IC13.15 (~CAS), IC14.15 (~CAS), IC15.15 (~CAS), IC16.15 (~CAS), IC17.15 (~CAS), IC18.15 (~CAS)
~RAS: IC11.4 (~RAS), IC12.4 (~RAS), IC13.4 (~RAS), IC14.4 (~RAS), IC15.4 (~RAS), IC16.4 (~RAS), IC17.4 (~RAS), IC18.4 (~RAS)
~VCASII: IC86.15 (~CAS), IC87.15 (~CAS), IC88.15 (~CAS), IC89.15 (~CAS), IC90.15 (~CAS), IC91.15 (~CAS), IC92.15 (~CAS), IC93.15 (~CAS)
~VEWR: IC64.3 (~WRITE), IC65.3 (~WRITE), IC66.3 (~WRITE), IC67.3 (~WRITE), IC68.3 (~WRITE), IC69.3 (~WRITE), IC70.3 (~WRITE), IC71.3 (~WRITE), IC86.3 (~WRITE), IC87.3 (~WRITE), IC88.3 (~WRITE), IC89.3 (~WRITE), IC90.3 (~WRITE), IC91.3 (~WRITE), IC92.3 (~WRITE), IC93.3 (~WRITE)
~VRAS: IC64.4 (~RAS), IC65.4 (~RAS), IC66.4 (~RAS), IC67.4 (~RAS), IC68.4 (~RAS), IC69.4 (~RAS), IC70.4 (~RAS), IC71.4 (~RAS), IC86.4 (~RAS), IC87.4 (~RAS), IC88.4 (~RAS), IC89.4 (~RAS), IC90.4 (~RAS), IC91.4 (~RAS), IC92.4 (~RAS), IC93.4 (~RAS)

Notes on the sheet:
BANK 2
128,192
48,96
BANK 1
BANK 3
96,128,192
NO DECOUPLING CAPS
It's 5V
