Board-Folk/Camputers-Lynx/Lynx 128/Kicad/lynx_ramsignals.kicad_sch

## KiCad design Lynx 128/Kicad/lynx_ramsignals.kicad_sch (2025-07-15)

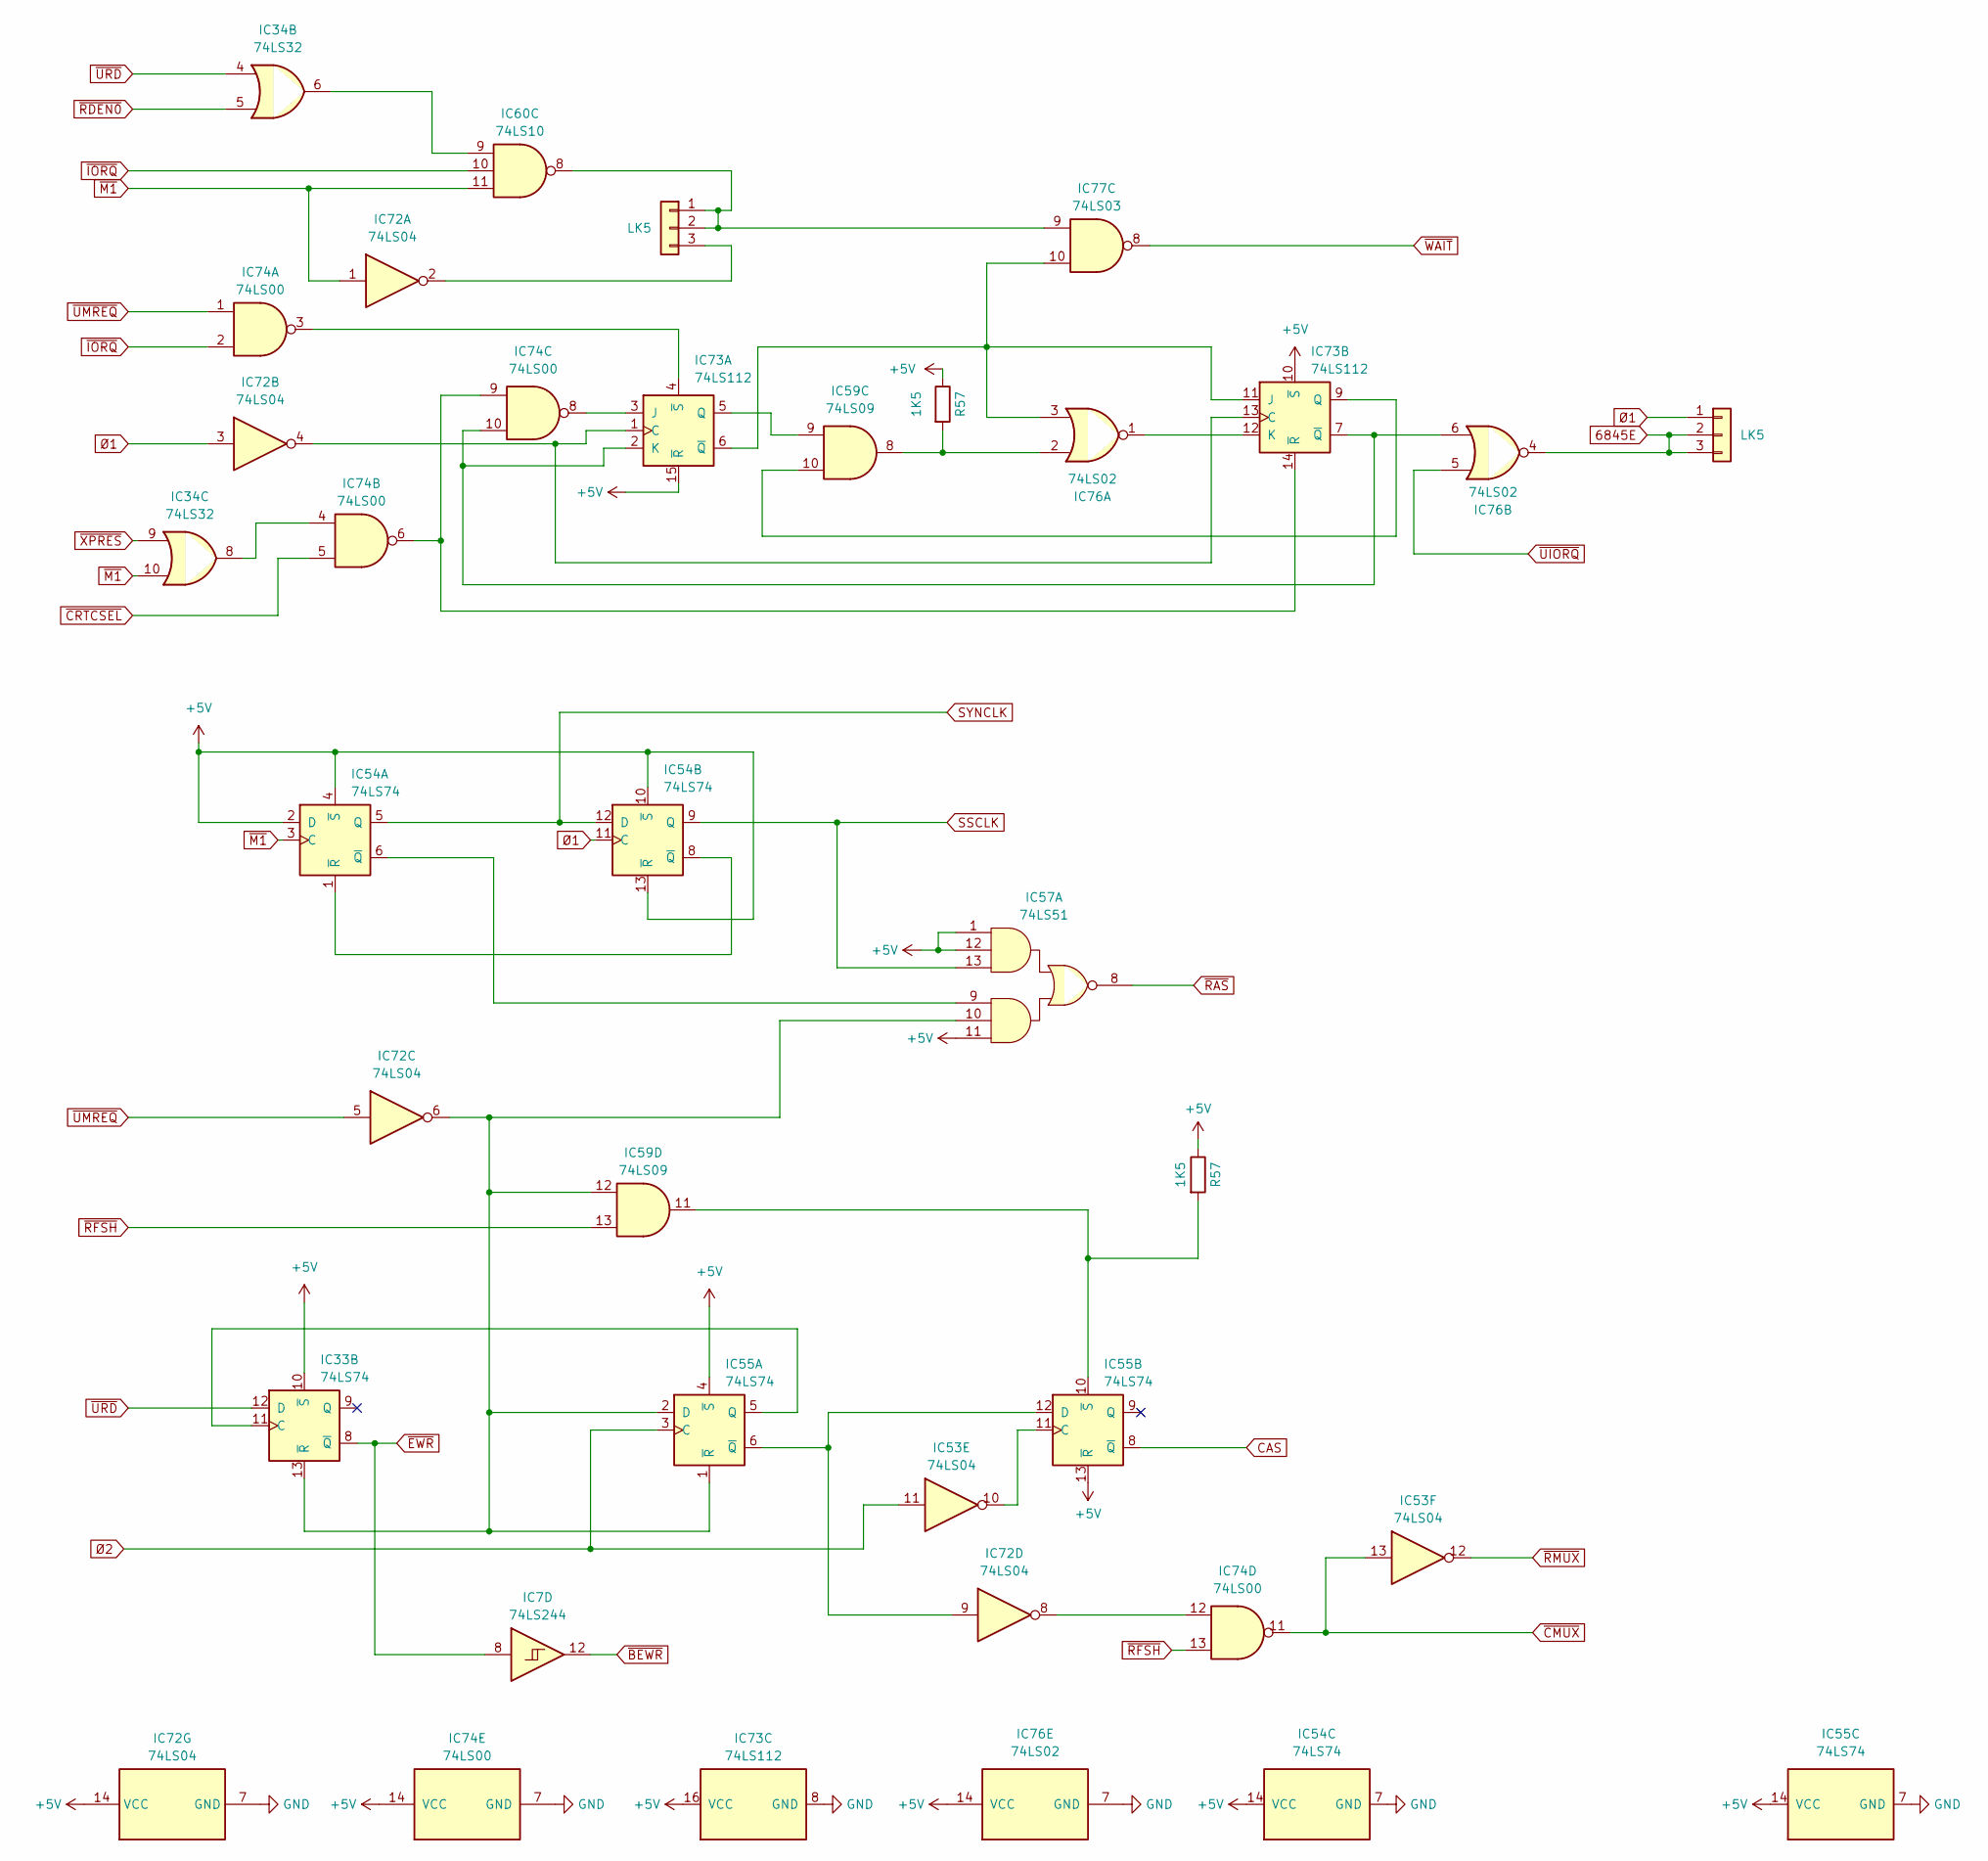
[picture p35: schematic lynx_ramsignals.kicad_sch]

Parts:
IC7: 74LS244; DIP-20_W7.62mm
IC33, IC54, IC55: 74LS74; DIP-14_W7.62mm
IC34: 74LS32; DIP-14_W7.62mm
IC53, IC72: 74LS04; DIP-14_W7.62mm
IC57: 74LS51; DIP-14_W7.62mm
IC59: 74LS09; DIP-14_W7.62mm
IC60: 74LS10; DIP-14_W7.62mm
IC73: 74LS112; DIP-16_W7.62mm
IC74: 74LS00; DIP-14_W7.62mm
IC76: 74LS02; DIP-14_W7.62mm
IC77: 74LS03; DIP-14_W7.62mm
LK5: -; LK 3-Pin 2.54mm - No Box
R57: 1K5; Resistor 10.16mm

Connections:
6845E: IC76.4, LK5.2, LK5.3
+5V: IC33.10 (~S), IC54.2 (D), IC54.4 (~S), IC54.10 (~S), IC54.13 (~R), IC54.14 (VCC), IC55.4 (~S), IC55.13 (~R), IC55.14 (VCC), IC57.1, IC57.11, IC57.12, IC72.14 (VCC), IC73.10 (~S), IC73.15 (~R), IC73.16 (VCC), IC74.14 (VCC), IC76.14 (VCC), R57.1
CAS: IC55.8 (~Q)
GND: IC54.7 (GND), IC55.7 (GND), IC72.7 (GND), IC73.8 (GND), IC74.7 (GND), IC76.7 (GND)
unnamed: IC33.11 (C), IC55.5 (Q)
unnamed: IC33.13 (~R), IC55.1 (~R), IC55.2 (D), IC57.10, IC59.12, IC72.6
unnamed: IC34.6, IC60.9
unnamed: IC34.8, IC74.4
unnamed: IC53.10, IC55.11 (C)
unnamed: IC54.1 (~R), IC54.8 (~Q)
unnamed: IC54.6 (~Q), IC57.9
unnamed: IC55.10 (~S), IC59.11, R57.2
unnamed: IC55.6 (~Q), IC55.12 (D), IC72.9
unnamed: IC59.8, IC76.2, R57.2
unnamed: IC59.9, IC73.5 (Q)
unnamed: IC59.10, IC73.9 (Q)
unnamed: IC60.8, IC77.9, LK5.1, LK5.2
unnamed: IC72.2, LK5.3
unnamed: IC72.4, IC73.1 (C), IC73.13 (C)
unnamed: IC72.8, IC74.12
unnamed: IC73.2 (K), IC73.7 (~Q), IC74.10, IC76.6
unnamed: IC73.3 (J), IC74.8
unnamed: IC73.4 (~S), IC74.3
unnamed: IC73.6 (~Q), IC73.11 (J), IC76.3, IC77.10
unnamed: IC73.12 (K), IC76.1
unnamed: IC73.14 (~R), IC74.6, IC74.9
SSCLK: IC54.9 (Q), IC57.13
SYNCLK: IC54.5 (Q), IC54.12 (D)
~BEWR: IC7.12
~CMUX: IC53.13, IC74.11
~CRTCSEL: IC74.5
~EWR: IC7.8, IC33.8 (~Q)
~IORQ: IC60.10, IC74.2
~M1: IC34.10, IC54.3 (C), IC60.11, IC72.1
~RAS: IC57.8
~RDEN0: IC34.5
~RFSH: IC59.13, IC74.13
~RMUX: IC53.12
~UIORQ: IC76.5
~UMREQ: IC72.5, IC74.1
~URD: IC33.12 (D), IC34.4
~WAIT: IC77.8
~XPRES: IC34.9
Ø1: IC54.11 (C), IC72.3, LK5.1
Ø2: IC53.11, IC55.3 (C)
