Board-Folk/Camputers-Lynx/Lynx 128/Kicad/lynx_videotiming.kicad_sch

## KiCad design Lynx 128/Kicad/lynx_videotiming.kicad_sch (2025-07-15)

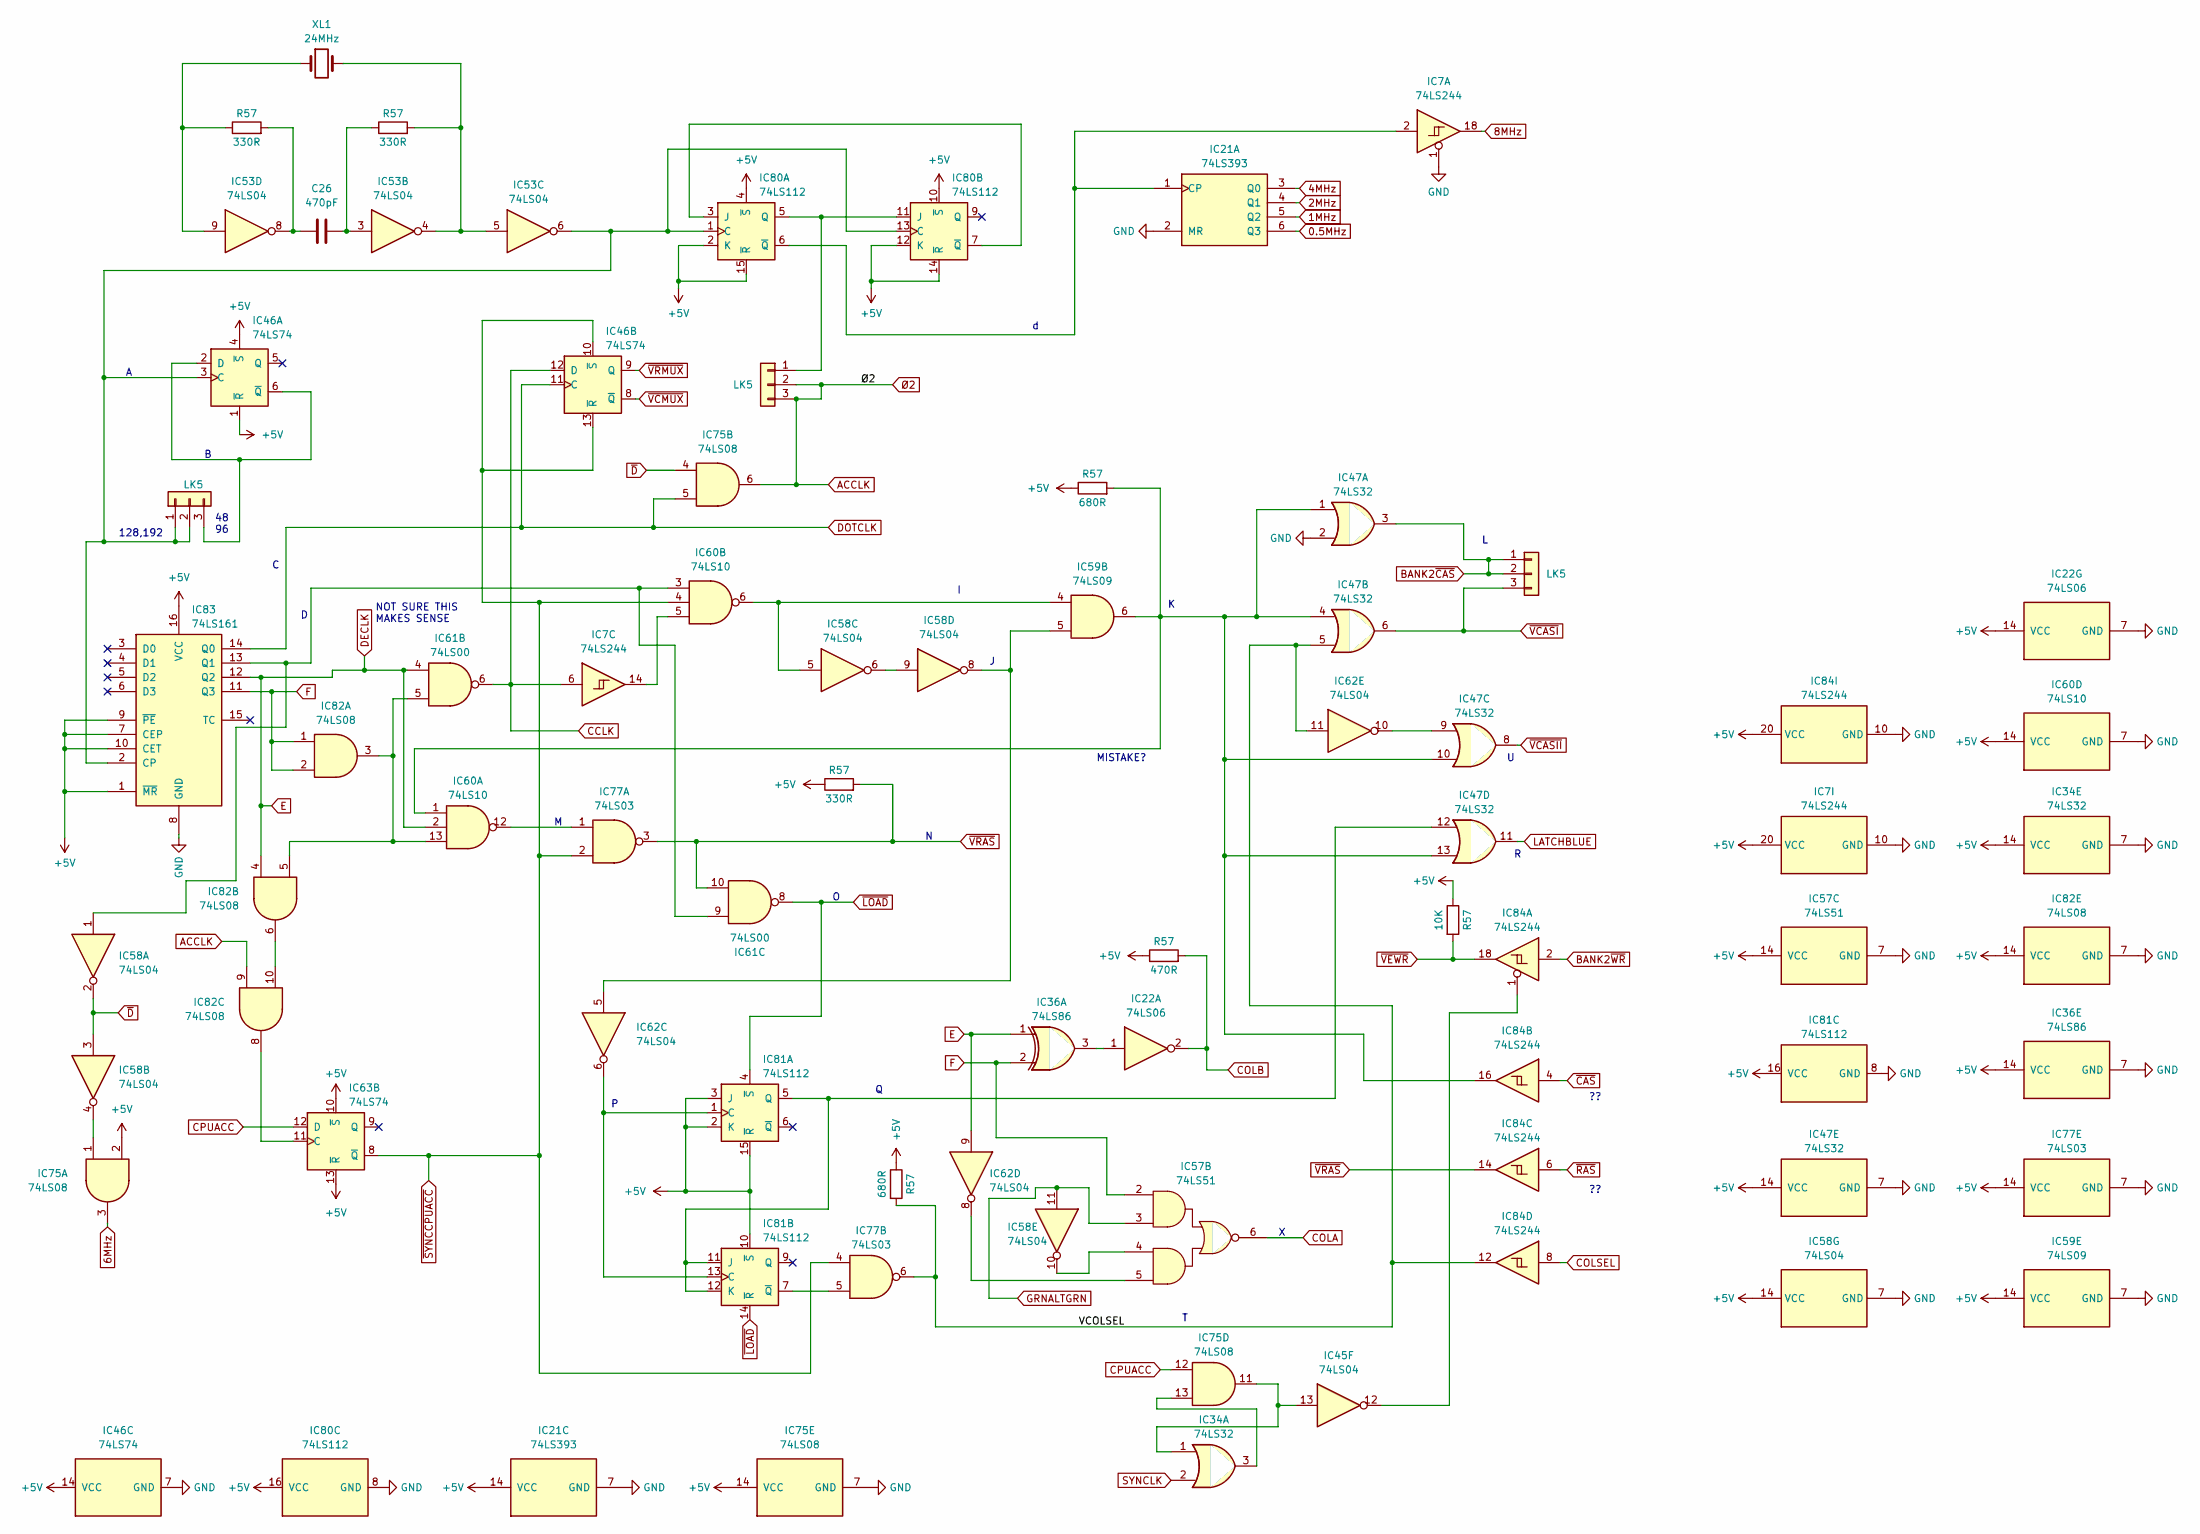
[picture p36: schematic lynx_videotiming.kicad_sch]

Parts:
C26: 470pF; C_Disc_5.08mm - Large Box
IC7, IC84: 74LS244; DIP-20_W7.62mm
IC21: 74LS393; DIP-14_W7.62mm
IC22: 74LS06; DIP-14_W7.62mm
IC34, IC47: 74LS32; DIP-14_W7.62mm
IC36: 74LS86; DIP-14_W7.62mm
IC45, IC53, IC58, IC62: 74LS04; DIP-14_W7.62mm
IC46, IC63: 74LS74; DIP-14_W7.62mm
IC57: 74LS51; DIP-14_W7.62mm
IC59: 74LS09; DIP-14_W7.62mm
IC60: 74LS10; DIP-14_W7.62mm
IC61: 74LS00; DIP-14_W7.62mm
IC75, IC82: 74LS08; DIP-14_W7.62mm
IC77: 74LS03; DIP-14_W7.62mm
IC80, IC81: 74LS112; DIP-16_W7.62mm
IC83: 74LS161; DIP-16_W7.62mm
LK5: -; LK 3-Pin 2.54mm - No Box
R57: 10K; Resistor 10.16mm
XL1: 24MHz; 5.08mm Misc - No Box

Connections:
0.5MHz: IC21.6 (Q3)
1MHz: IC21.5 (Q2)
2MHz: IC21.4 (Q1)
4MHz: IC21.3 (Q0)
6MHz: IC75.3
8MHz: IC7.18
+5V: IC7.20 (VCC), IC21.14 (VCC), IC22.14 (VCC), IC34.14 (VCC), IC36.14 (VCC), IC46.1 (~R), IC46.4 (~S), IC46.14 (VCC), IC47.14 (VCC), IC57.14 (VCC), IC58.14 (VCC), IC59.14 (VCC), IC60.14 (VCC), IC63.10 (~S), IC63.13 (~R), IC75.2, IC75.14 (VCC), IC77.14 (VCC), IC80.2 (K), IC80.4 (~S), IC80.10 (~S), IC80.12 (K), IC80.14 (~R), IC80.15 (~R), IC80.16 (VCC), IC81.2 (K), IC81.3 (J), IC81.10 (~S), IC81.15 (~R), IC81.16 (VCC), IC82.14 (VCC), IC83.1 (~MR), IC83.7 (CEP), IC83.9 (~PE), IC83.10 (CET), IC83.16 (VCC), IC84.20 (VCC), R57.1
ACCLK: IC75.6, IC82.9, LK5.2, LK5.3
BANK2~CAS: IC47.3, LK5.1, LK5.2
BANK2~WR: IC84.2
CCLK: IC7.6, IC46.12 (D), IC61.6
COLA: IC57.6
COLB: IC22.2, R57.2
COLSEL: IC84.8
CPUACC: IC63.12 (D), IC75.12
DECLK: IC36.1, IC60.2, IC61.4, IC62.9, IC82.4, IC83.12 (Q2)
DOTCLK: IC46.11 (C), IC75.5, IC83.14 (Q0)
F: IC36.2, IC57.2, IC82.1, IC82.2, IC83.11 (Q3)
GND: IC7.1, IC7.10 (GND), IC21.2 (MR), IC21.7 (GND), IC22.7 (GND), IC34.7 (GND), IC36.7 (GND), IC46.7 (GND), IC47.2, IC47.7 (GND), IC57.7 (GND), IC58.7 (GND), IC59.7 (GND), IC60.7 (GND), IC75.7 (GND), IC77.7 (GND), IC80.8 (GND), IC81.8 (GND), IC82.7 (GND), IC83.8 (GND), IC84.10 (GND)
GRNALTGRN: IC57.3, IC58.11
LATCHBLUE: IC47.11
unnamed: C26.1, IC53.8, R57.2
unnamed: C26.2, IC53.3, R57.1
unnamed: IC7.2, IC21.1 (CP), IC80.6 (~Q)
unnamed: IC22.1, IC36.3
unnamed: IC34.1, IC45.13, IC75.11
unnamed: IC34.3, IC75.13
unnamed: IC45.12, IC84.1
unnamed: IC46.2 (D), IC46.6 (~Q), LK5.3
unnamed: IC46.3 (C), IC53.6, IC80.1 (C), IC80.13 (C), IC83.2 (CP), LK5.1, LK5.2
unnamed: IC47.1, IC47.4, IC47.10, IC47.13, IC59.6, IC60.1, IC84.16, R57.2
unnamed: IC47.9, IC62.10
unnamed: IC47.12, IC81.5 (Q), IC81.11 (J), IC81.12 (K)
unnamed: IC53.4, IC53.5, R57.2, XL1.2
unnamed: IC53.9, R57.1, XL1.1
unnamed: IC57.4, IC58.10
unnamed: IC57.5, IC62.8
unnamed: IC58.1, IC60.3, IC61.9, IC83.13 (Q1)
unnamed: IC58.4, IC75.1
unnamed: IC58.5, IC59.4, IC60.6
unnamed: IC58.6, IC58.9
unnamed: IC58.8, IC59.5, IC62.5
unnamed: IC7.14, IC60.5
unnamed: IC60.12, IC77.1
unnamed: IC60.13, IC61.5, IC82.3, IC82.5
unnamed: IC62.6, IC81.1 (C), IC81.13 (C)
unnamed: IC63.11 (C), IC82.8
unnamed: IC77.5, IC81.7 (~Q)
unnamed: IC80.3 (J), IC80.7 (~Q)
unnamed: IC80.5 (Q), IC80.11 (J), LK5.1
unnamed: IC82.6, IC82.10
SYNCLK: IC34.2
VCOLSEL: IC47.5, IC62.11, IC77.6, IC84.12, R57.2
~CAS: IC84.4
~D: IC58.2, IC58.3, IC75.4
~LOAD: IC61.8, IC81.4 (~S), IC81.14 (~R)
~RAS: IC84.6
~SYNCCPUACC: IC46.10 (~S), IC46.13 (~R), IC60.4, IC63.8 (~Q), IC77.2, IC77.4
~VCASII: IC47.8
~VCASI: IC47.6, LK5.3
~VCMUX: IC46.8 (~Q)
~VEWR: IC84.18, R57.2
~VRAS: IC61.10, IC77.3, IC84.14, R57.2
~VRMUX: IC46.9 (Q)

Notes on the sheet:
128,192
48 96
NOT SURE THIS MAKES SENSE
MISTAKE?
