Board-Folk/Camputers-Lynx/Lynx 96/Expansions/Lynx-MK1-MEM-Original/Kicad/Lynx-MK1-MEM.kicad_sch

## KiCad design Lynx 96/Expansions/Lynx-MK1-MEM-Original/Kicad/Lynx-MK1-MEM.kicad_sch (2025-07-15)

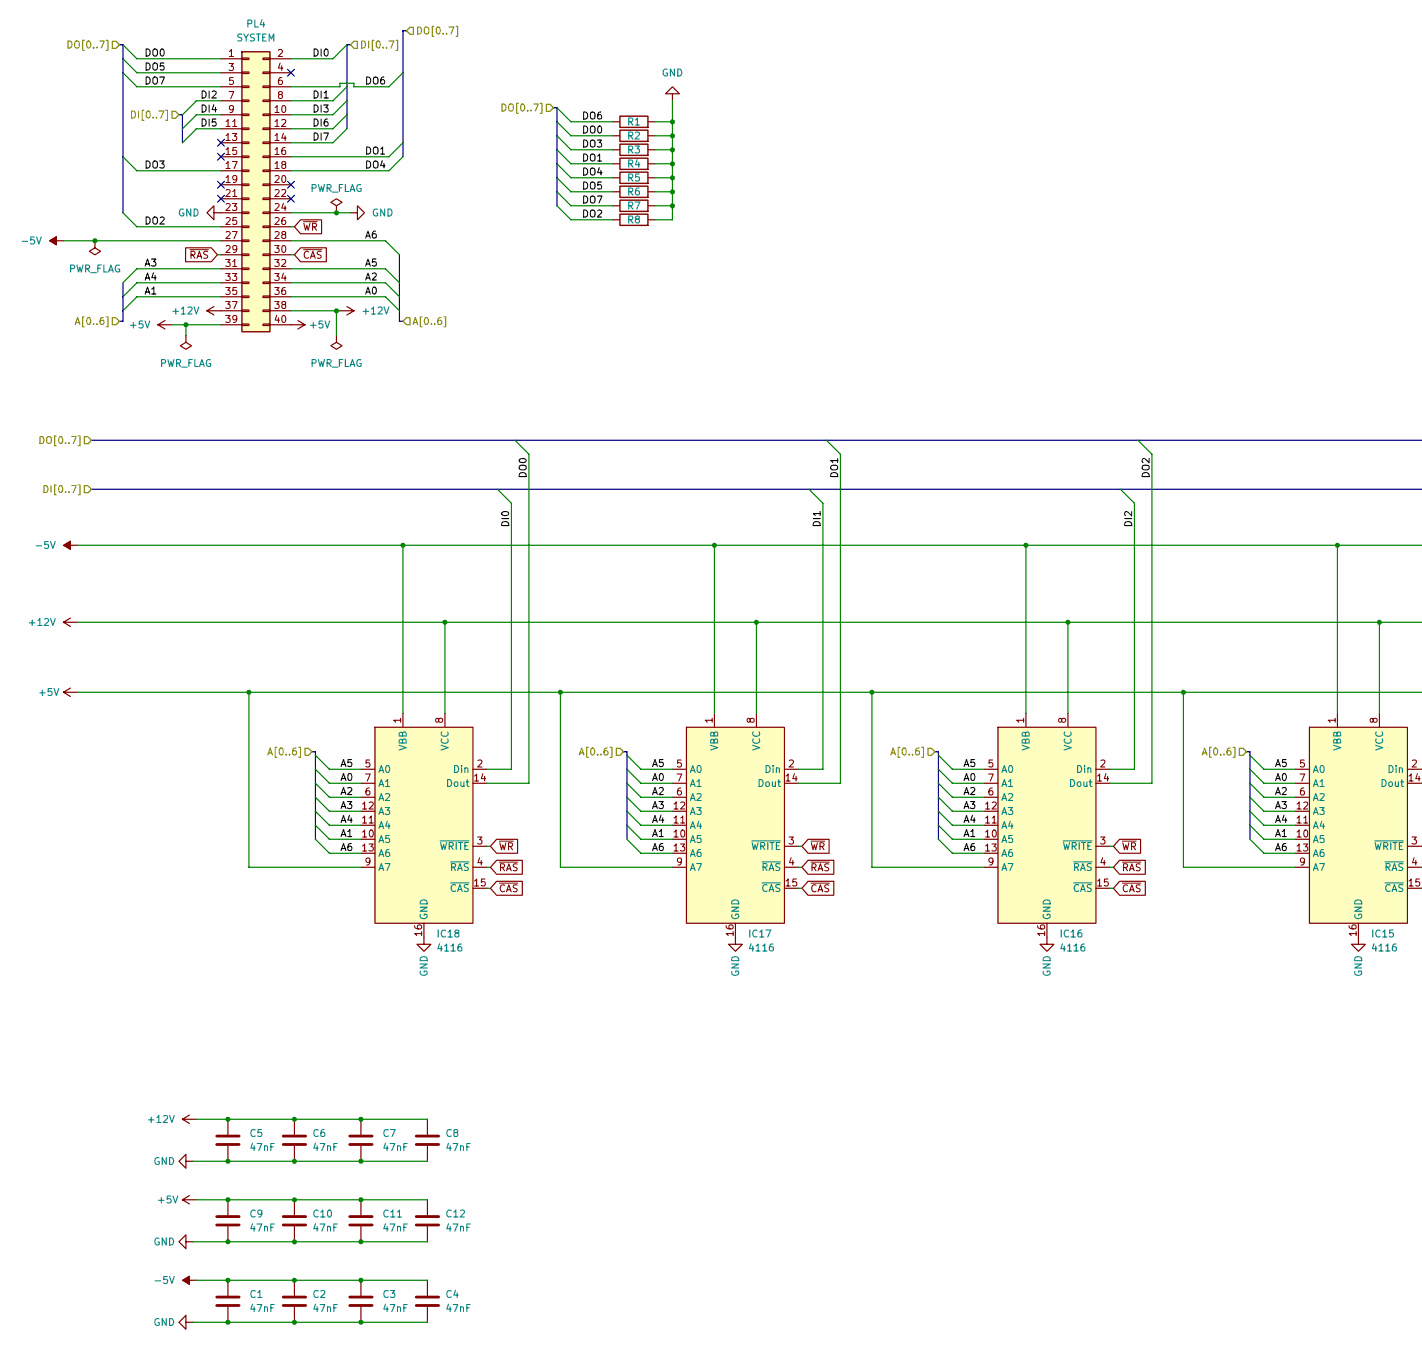
[picture p37: schematic Lynx-MK1-MEM.kicad_sch, part in row 1, column 1]

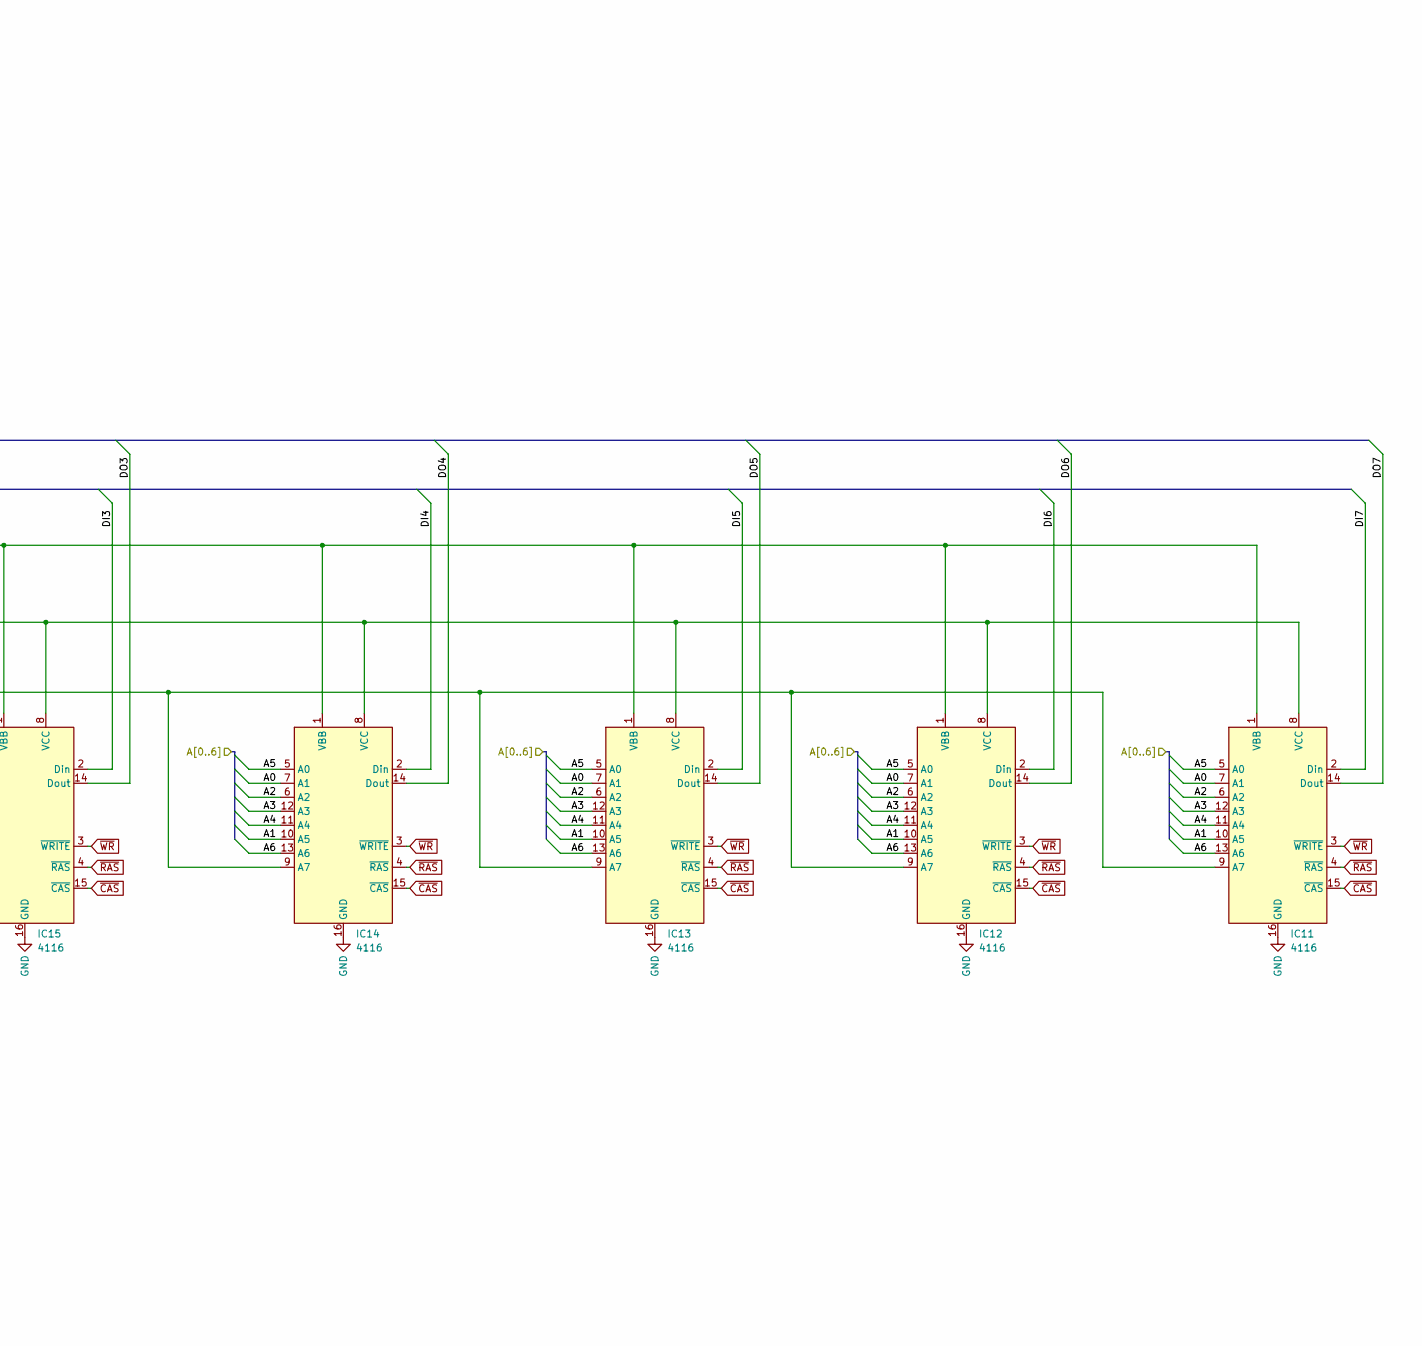
[picture p38: schematic Lynx-MK1-MEM.kicad_sch, part in row 1, column 2]

Parts:
C1, C2, C3, C4, C5, C6, C7, C8, C9, C10, C11, C12: 47nF; C_Disc_P5.00mm
IC11, IC12, IC13, IC14, IC15, IC16, IC17, IC18: 4116; DIP-16_W7.62mm
PL4: SYSTEM; PinHeader_40_WIDE
R1, R2, R3, R4, R5, R6, R7, R8: 1K; R_Axial_P10.16mm

Connections:
+5V: C9.1, C10.1, C11.1, C12.1, IC11.9 (A7), IC12.9 (A7), IC13.9 (A7), IC14.9 (A7), IC15.9 (A7), IC16.9 (A7), IC17.9 (A7), IC18.9 (A7), PL4.39, PL4.40
+12V: C5.1, C6.1, C7.1, C8.1, IC11.8 (VCC), IC12.8 (VCC), IC13.8 (VCC), IC14.8 (VCC), IC15.8 (VCC), IC16.8 (VCC), IC17.8 (VCC), IC18.8 (VCC), PL4.37, PL4.38
-5V: C1.1, C2.1, C3.1, C4.1, IC11.1 (VBB), IC12.1 (VBB), IC13.1 (VBB), IC14.1 (VBB), IC15.1 (VBB), IC16.1 (VBB), IC17.1 (VBB), IC18.1 (VBB), PL4.27
A0: IC11.7 (A1), IC12.7 (A1), IC13.7 (A1), IC14.7 (A1), IC15.7 (A1), IC16.7 (A1), IC17.7 (A1), IC18.7 (A1), PL4.36
A1: IC11.10 (A5), IC12.10 (A5), IC13.10 (A5), IC14.10 (A5), IC15.10 (A5), IC16.10 (A5), IC17.10 (A5), IC18.10 (A5), PL4.35
A2: IC11.6 (A2), IC12.6 (A2), IC13.6 (A2), IC14.6 (A2), IC15.6 (A2), IC16.6 (A2), IC17.6 (A2), IC18.6 (A2), PL4.34
A3: IC11.12 (A3), IC12.12 (A3), IC13.12 (A3), IC14.12 (A3), IC15.12 (A3), IC16.12 (A3), IC17.12 (A3), IC18.12 (A3), PL4.31
A4: IC11.11 (A4), IC12.11 (A4), IC13.11 (A4), IC14.11 (A4), IC15.11 (A4), IC16.11 (A4), IC17.11 (A4), IC18.11 (A4), PL4.33
A5: IC11.5 (A0), IC12.5 (A0), IC13.5 (A0), IC14.5 (A0), IC15.5 (A0), IC16.5 (A0), IC17.5 (A0), IC18.5 (A0), PL4.32
A6: IC11.13 (A6), IC12.13 (A6), IC13.13 (A6), IC14.13 (A6), IC15.13 (A6), IC16.13 (A6), IC17.13 (A6), IC18.13 (A6), PL4.28
DI0: IC18.2 (Din), PL4.2
DI1: IC17.2 (Din), PL4.8
DI2: IC16.2 (Din), PL4.7
DI3: IC15.2 (Din), PL4.10
DI4: IC14.2 (Din), PL4.9
DI5: IC13.2 (Din), PL4.11
DI6: IC12.2 (Din), PL4.12
DI7: IC11.2 (Din), PL4.14
DO0: IC18.14 (Dout), PL4.1, R2.1
DO1: IC17.14 (Dout), PL4.16, R4.1
DO2: IC16.14 (Dout), PL4.25, R8.1
DO3: IC15.14 (Dout), PL4.17, R3.1
DO4: IC14.14 (Dout), PL4.18, R5.1
DO5: IC13.14 (Dout), PL4.3, R6.1
DO6: IC12.14 (Dout), PL4.6, R1.1
DO7: IC11.14 (Dout), PL4.5, R7.1
GND: C1.2, C2.2, C3.2, C4.2, C5.2, C6.2, C7.2, C8.2, C9.2, C10.2, C11.2, C12.2, IC11.16 (GND), IC12.16 (GND), IC13.16 (GND), IC14.16 (GND), IC15.16 (GND), IC16.16 (GND), IC17.16 (GND), IC18.16 (GND), PL4.23, PL4.24, R1.2, R2.2, R3.2, R4.2, R5.2, R6.2, R7.2, R8.2
~CAS: IC11.15 (~CAS), IC12.15 (~CAS), IC13.15 (~CAS), IC14.15 (~CAS), IC15.15 (~CAS), IC16.15 (~CAS), IC17.15 (~CAS), IC18.15 (~CAS), PL4.30
~RAS: IC11.4 (~RAS), IC12.4 (~RAS), IC13.4 (~RAS), IC14.4 (~RAS), IC15.4 (~RAS), IC16.4 (~RAS), IC17.4 (~RAS), IC18.4 (~RAS), PL4.29
~WR: IC11.3 (~WRITE), IC12.3 (~WRITE), IC13.3 (~WRITE), IC14.3 (~WRITE), IC15.3 (~WRITE), IC16.3 (~WRITE), IC17.3 (~WRITE), IC18.3 (~WRITE), PL4.26
